jensenr30/cad/cheatsheets/CNC G Codes_files/g41-g42-Cutter-compensation.jpg

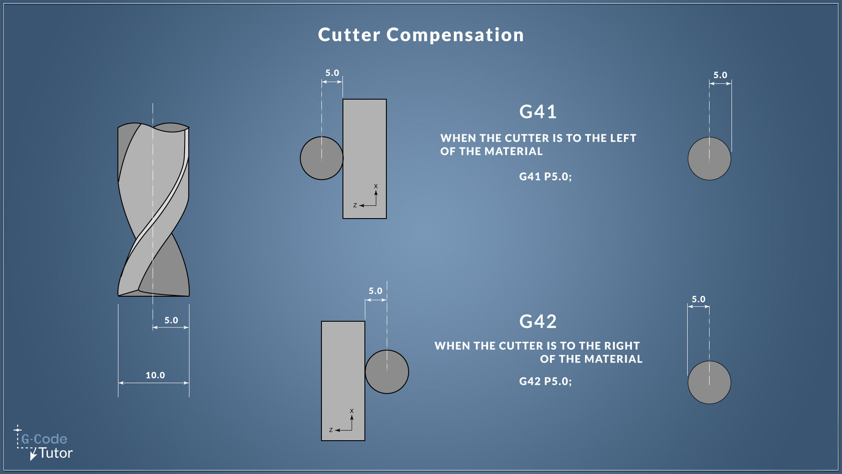
cheatsheets/CNC G Codes_files/g41-g42-Cutter-compensation.jpg
