jensenr30/cad/eagle6/555 stuff/555 blinker pcb.png

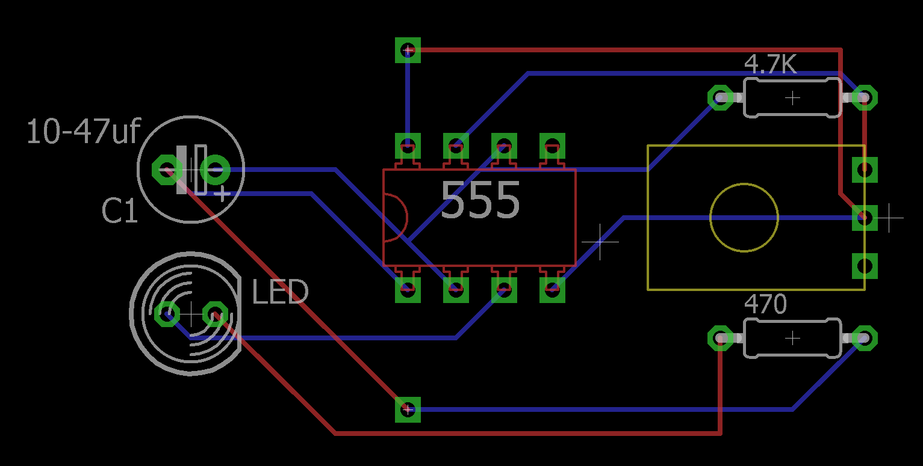
eagle6/555 stuff/555 blinker pcb.png
