jensenr30/cad/eagle6/dir.png

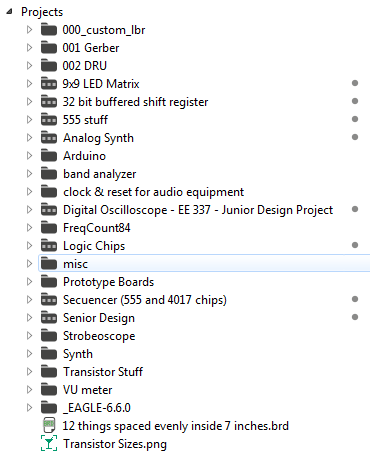
eagle6/dir.png
