jensenr30/cad/eagle6/misc/Logic Chips/AND gate.png

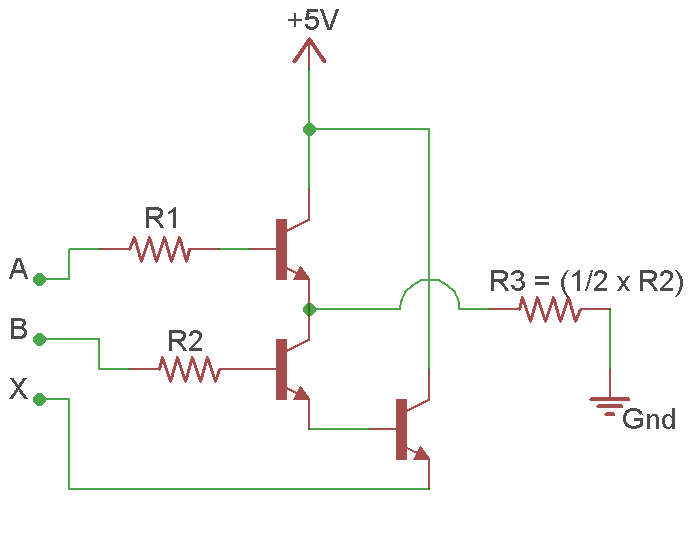
eagle6/misc/Logic Chips/AND gate.png
