jensenr30/cad/eagle6/misc/Logic Chips/D Latch Memory.png

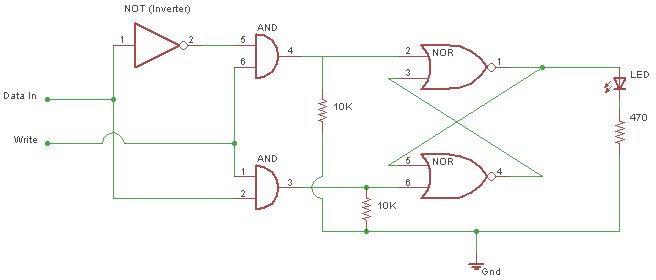
eagle6/misc/Logic Chips/D Latch Memory.png
