jensenr30/cad/eagle6/misc/noise generator output.jpg

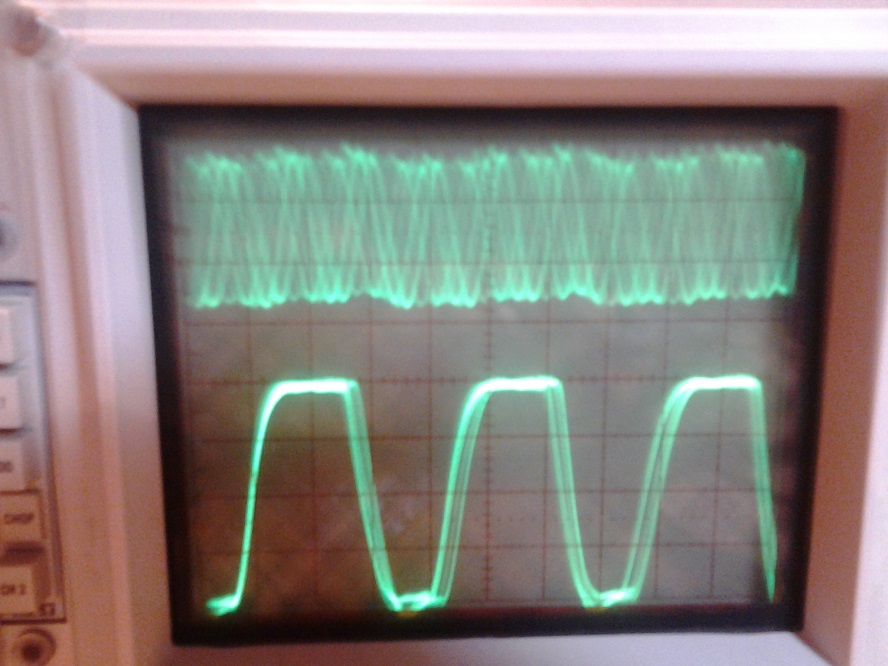
eagle6/misc/noise generator output.jpg
