jensenr30/cad/eagle6/misc/noise generator.jpg

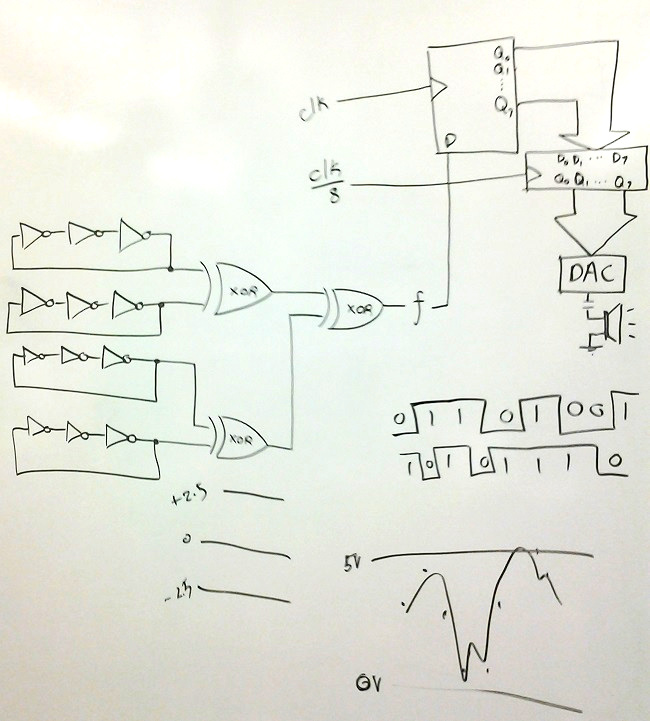
eagle6/misc/noise generator.jpg
