jensenr30/cad/eagle6/misc/people using my awful 555 AM harmonic radio transmitter/dangerous prototypes.png

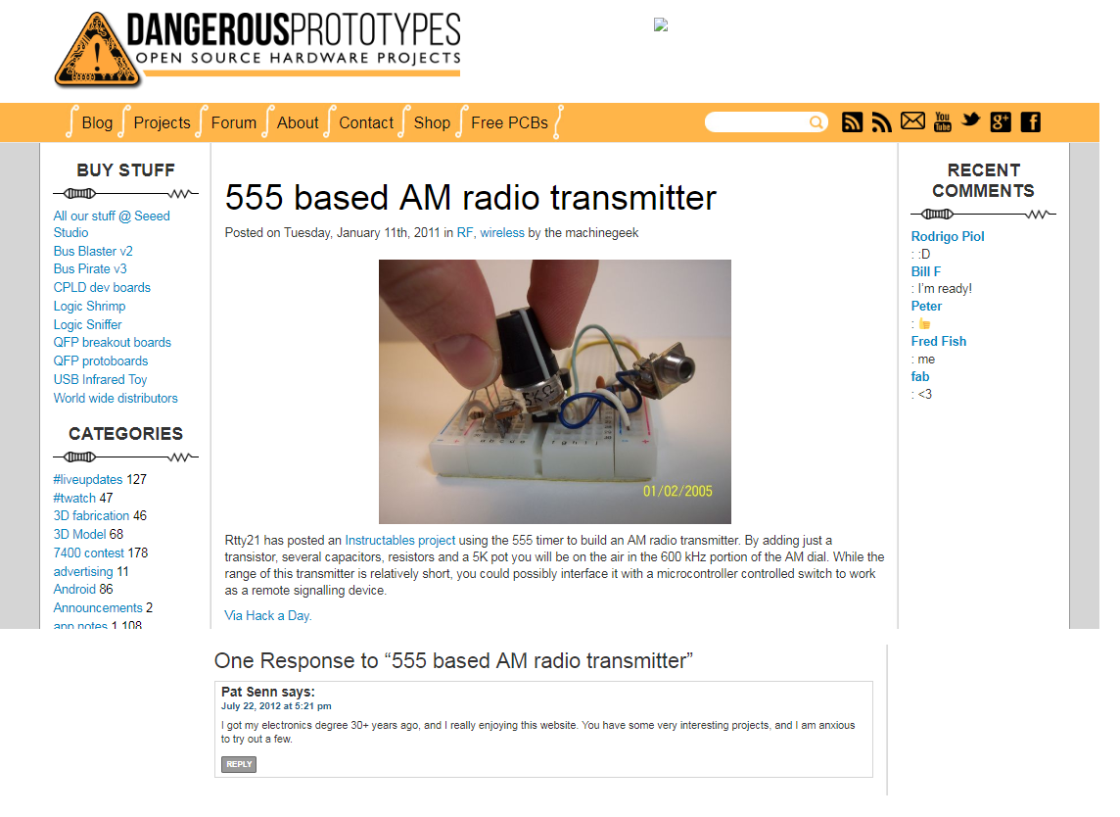
eagle6/misc/people using my awful 555 AM harmonic radio transmitter/dangerous prototypes.png
