jensenr30/cad/eagle6/misc/people using my awful 555 AM harmonic radio transmitter/Gainsville amature radio/Screenshot_1.png

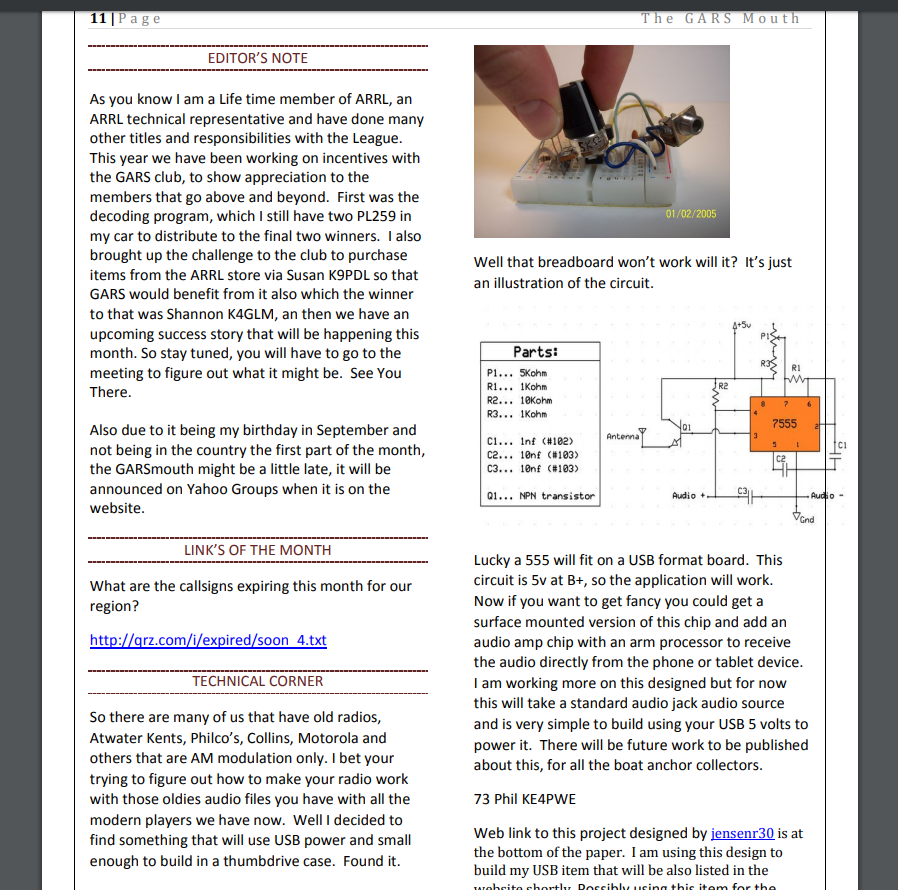
eagle6/misc/people using my awful 555 AM harmonic radio transmitter/Gainsville amature radio/Screenshot_1.png
