jensenr30/cad/eagle6/misc/sine8-200.png

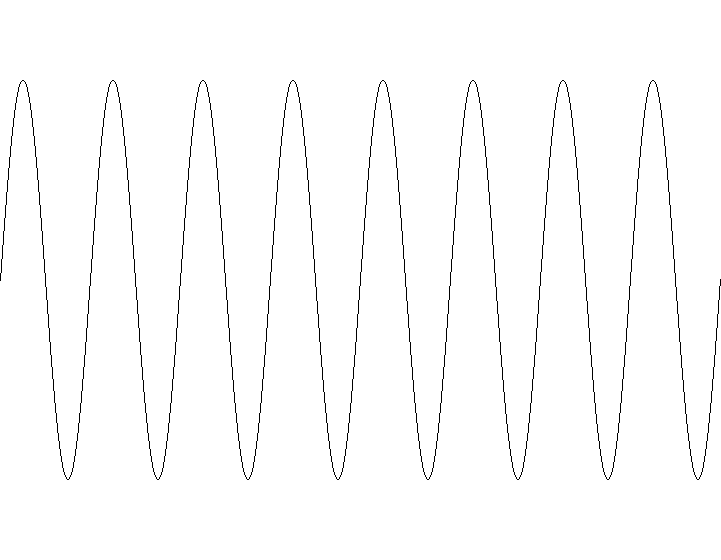
eagle6/misc/sine8-200.png
