jensenr30/cad/eagle6/misc/Transistor Sizes.png

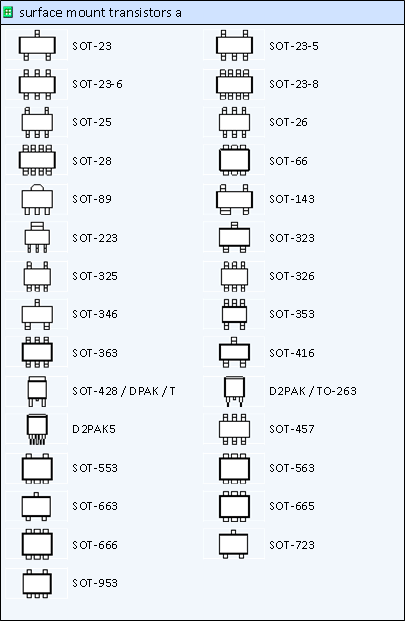
eagle6/misc/Transistor Sizes.png
