jensenr30/cad/eagle6/Prototype Boards/breakout board pack 1/render.png

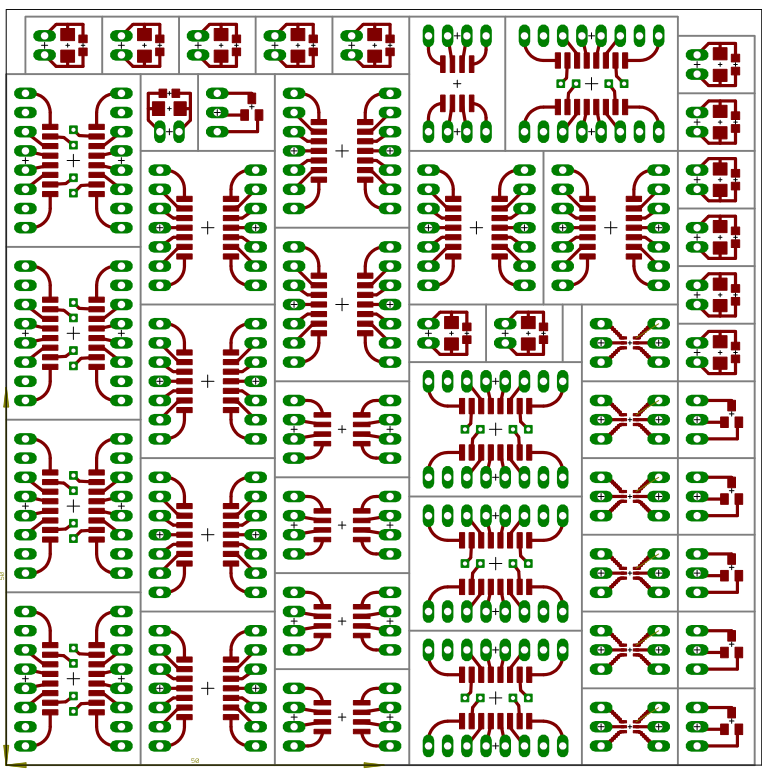
eagle6/Prototype Boards/breakout board pack 1/render.png
