jensenr30/cad/eagle6/Prototype Boards/pad-per-hole-and-rails/DirtyPCBOrder.png

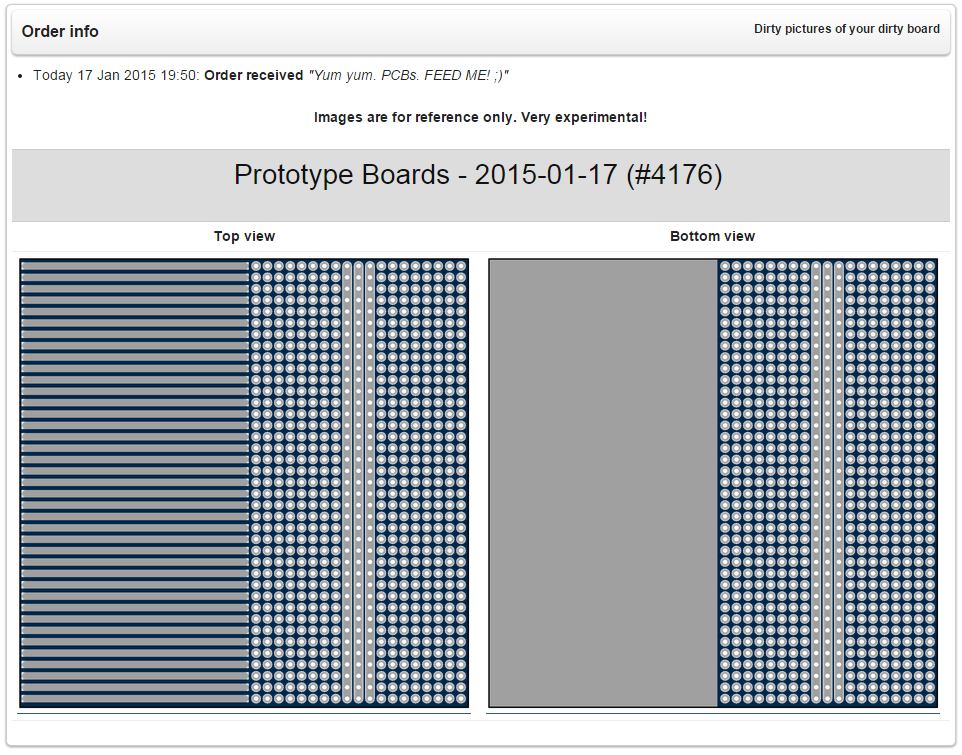
eagle6/Prototype Boards/pad-per-hole-and-rails/DirtyPCBOrder.png
