jensenr30/cad/eagle6/Prototype Boards/pad-per-hole-and-rails/render.png

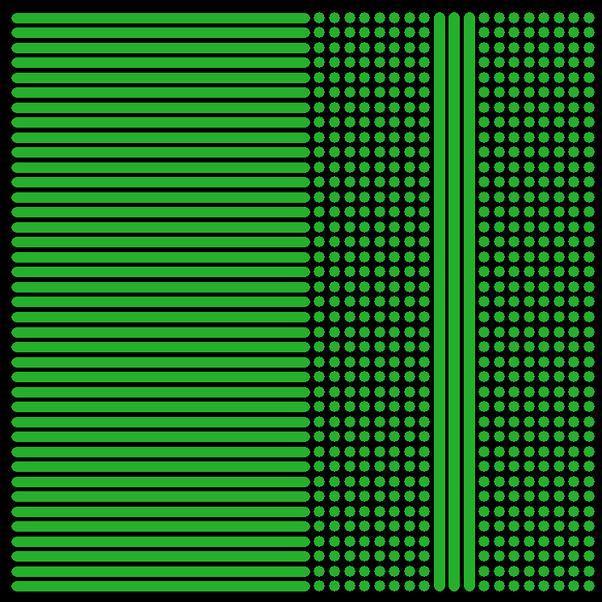
eagle6/Prototype Boards/pad-per-hole-and-rails/render.png
