jensenr30/cad/eagle6/Prototype Boards/surface mount pads/render.png

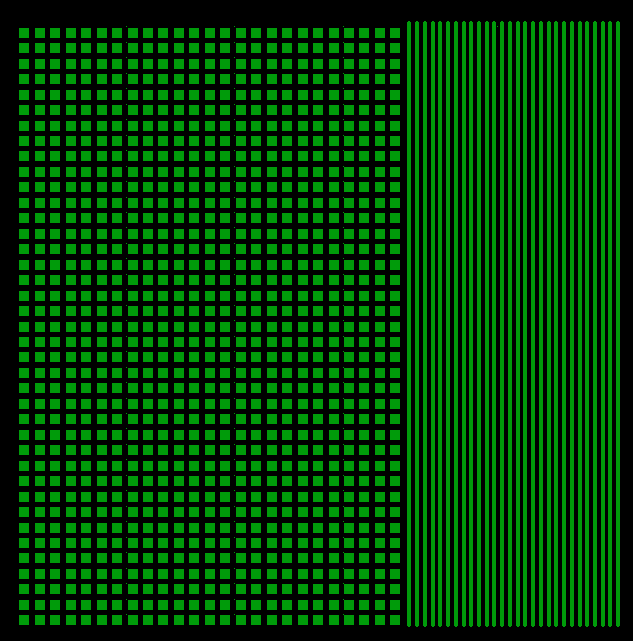
eagle6/Prototype Boards/surface mount pads/render.png
