jensenr30/cad/kicad4/XPhone/Input_Board/gerbers/Input Board-F.Fab.png

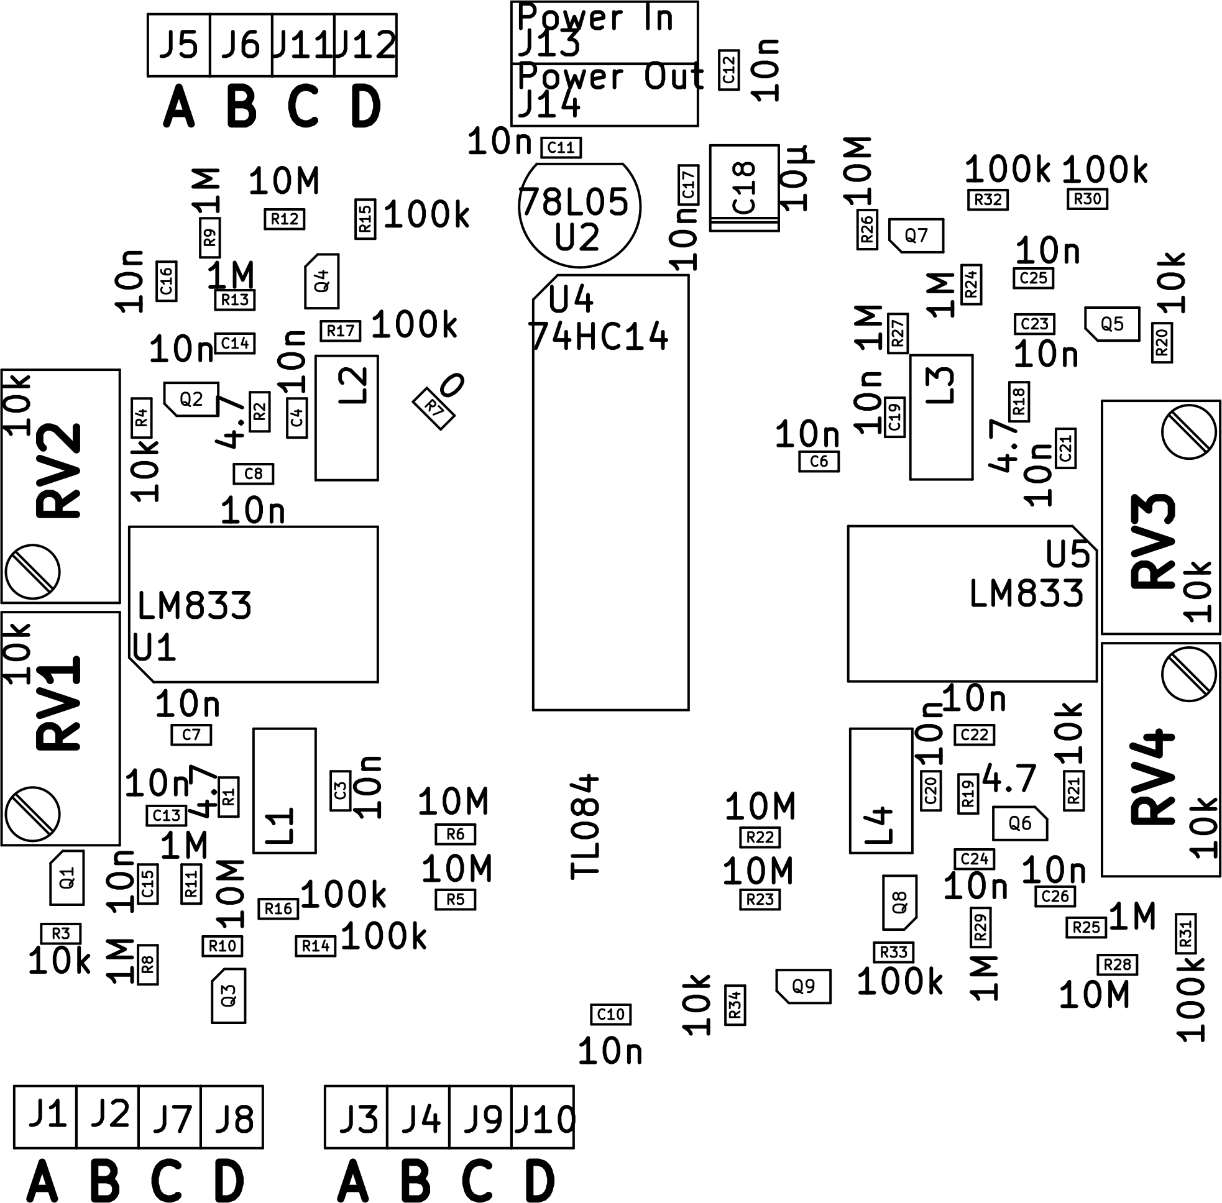
kicad4/XPhone/Input_Board/gerbers/Input Board-F.Fab.png
