jensenr30/cad/src/geography/u.s. states/wisconsin/wisconsin-from-google-maps.png

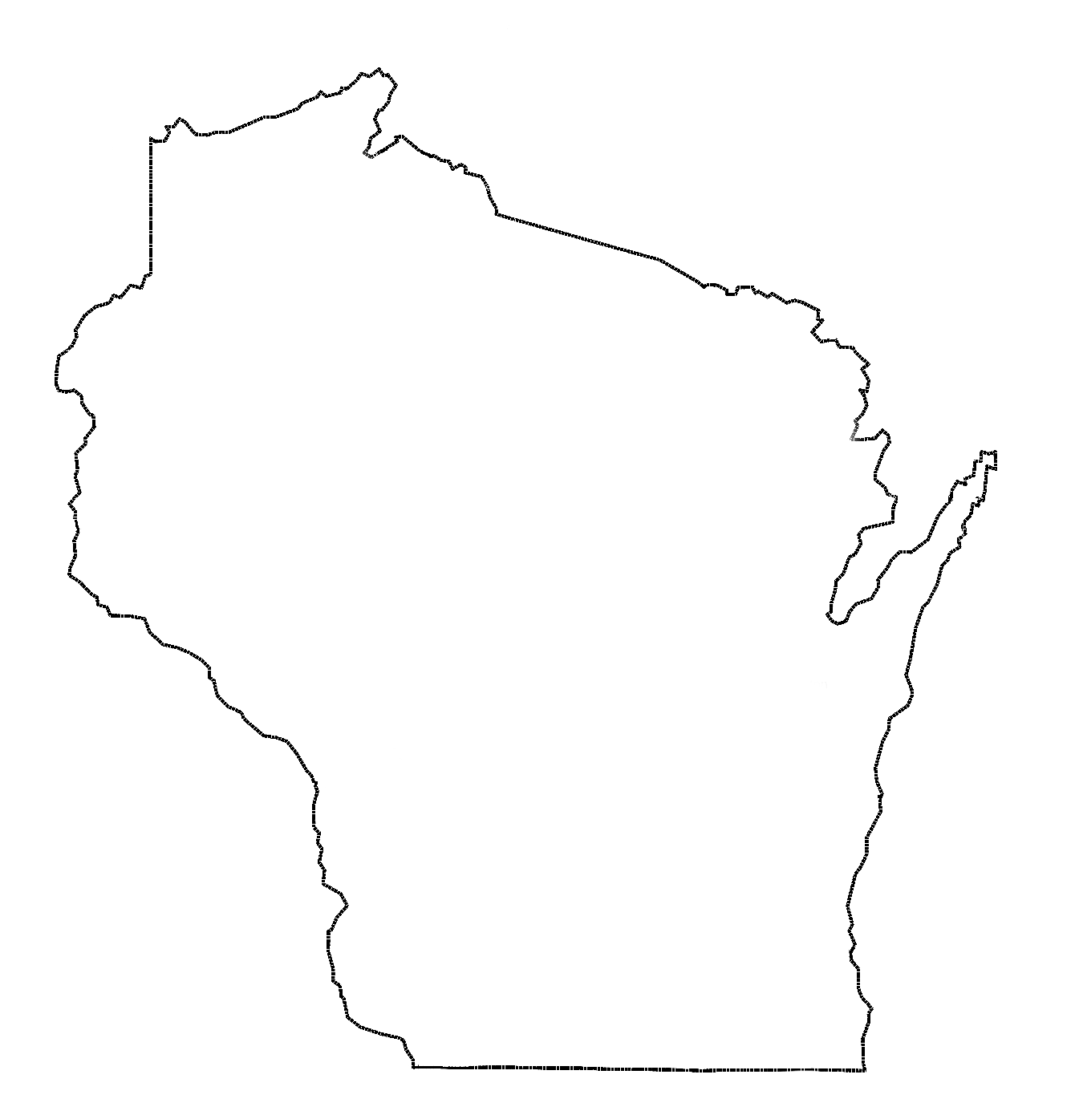
src/geography/u.s. states/wisconsin/wisconsin-from-google-maps.png
