jensenr30/cad/src/geography/u.s. states/wisconsin/wisconsin-silhouette-smooth-1.png

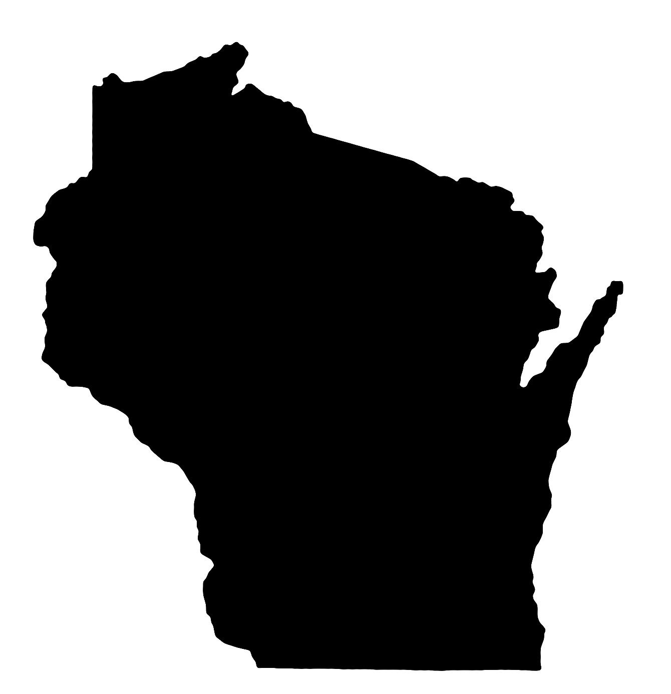
src/geography/u.s. states/wisconsin/wisconsin-silhouette-smooth-1.png
