jensenr30/cad/eagle6/8-Note Secuencer (555 and 4017 chips)/eight note sequencer.pdf

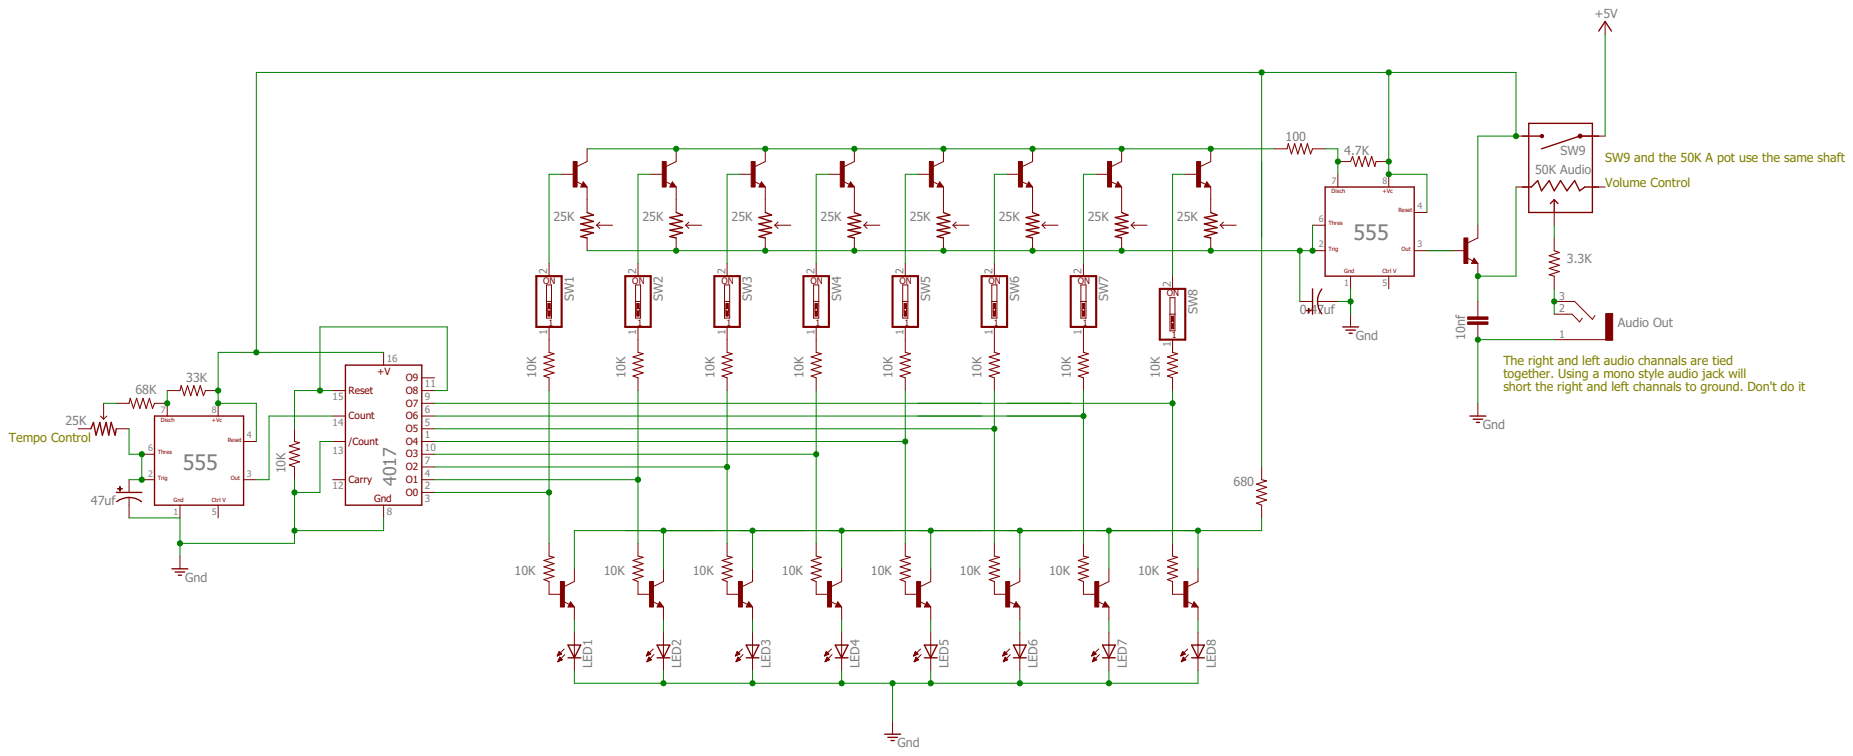
[picture p41: page 1]

SW9 and the 50K A pot use the same shaft Volume Control

The right and left audio channals are tied
together. Using a mono style audio jack will short the right and left channals to ground. Don't do it
