jensenr30/cad/eagle6/FreqCount84/FreqCount84.pdf

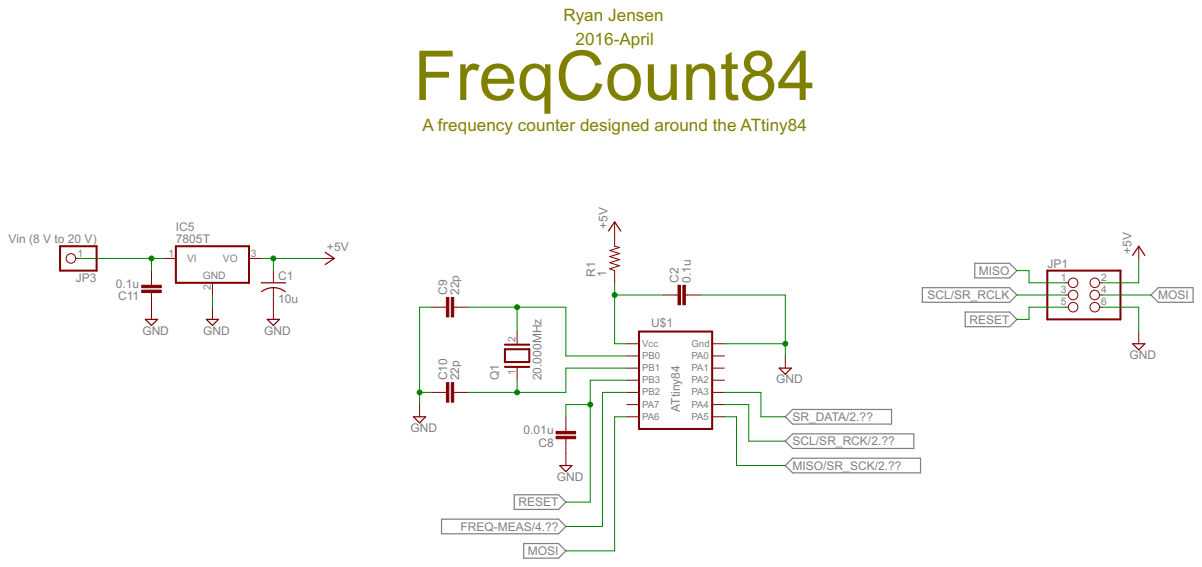
[picture p44: page 1]

A frequency counter designed around the ATtiny84

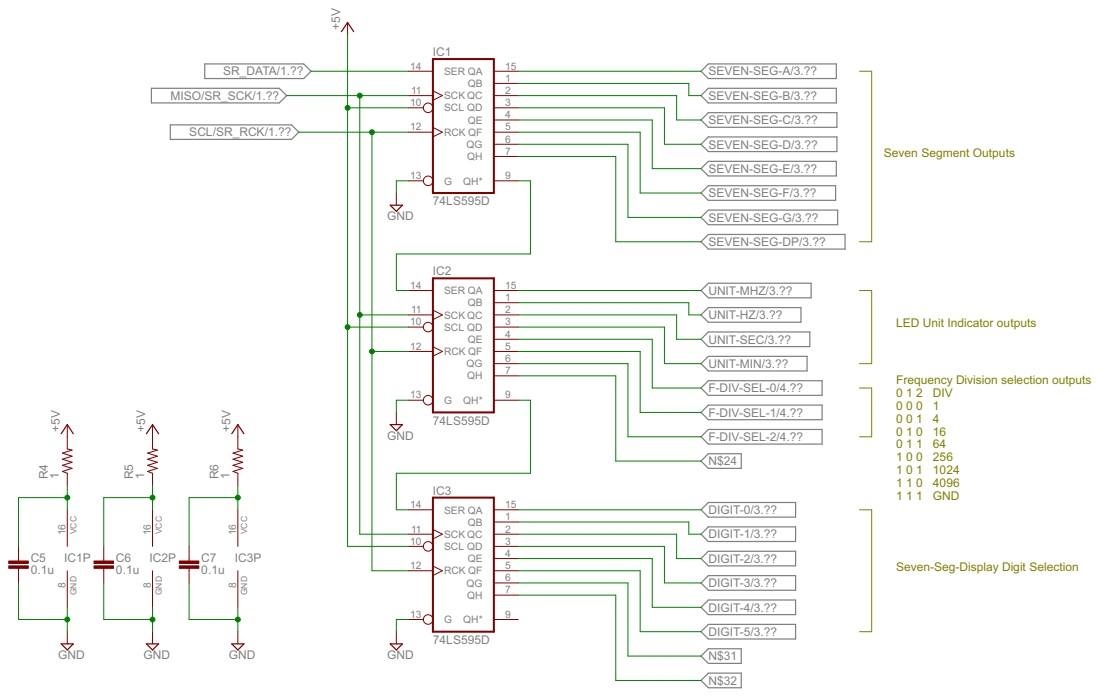
[picture p45: page 2]

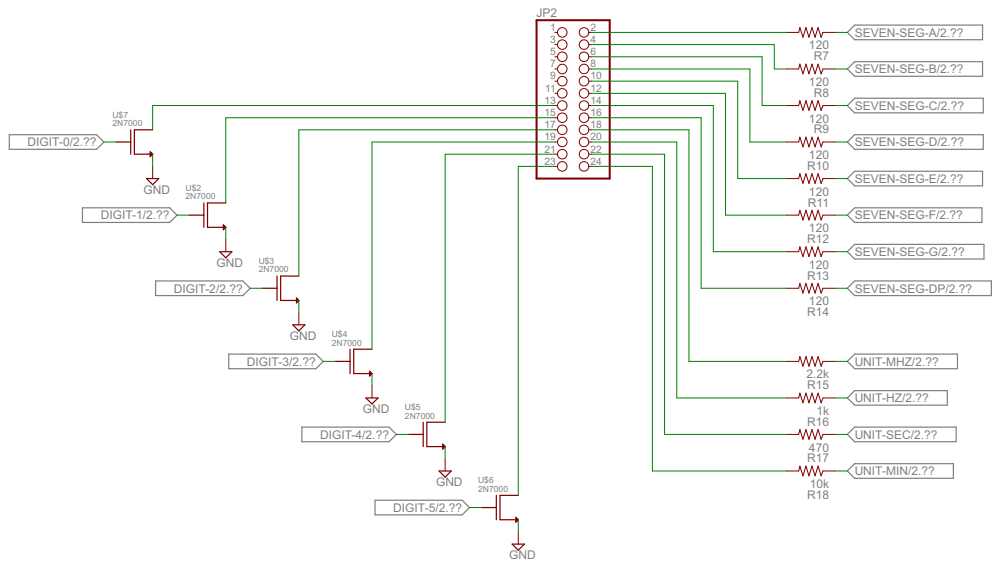
[picture p46: page 3]

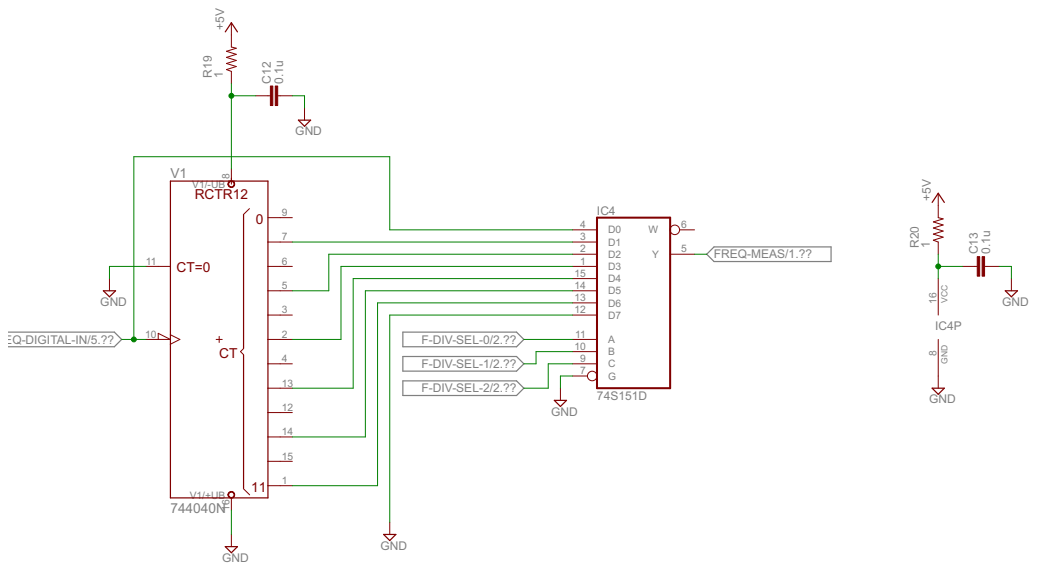
[picture p47: page 4]

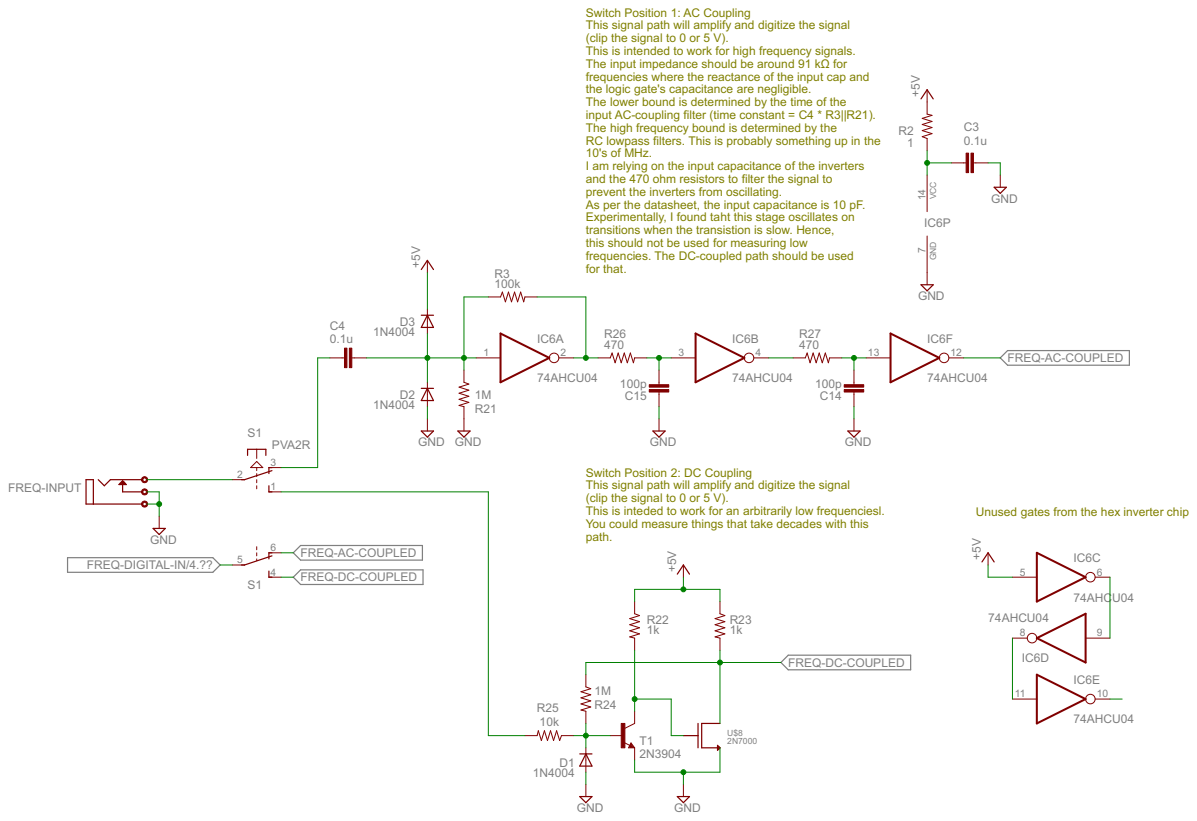
[picture p48: page 5]

Switch Position 1: AC Coupling
This signal path will amplify and digitize the signal
(clip the signal to 0 or 5 V). This is intended to work for high frequency signals. The input impedance should be around 91 kΩ for

frequencies where the reactance of the input cap and
the logic gate's capacitance are negligible. The lower bound is determined by the time of the

input AC-coupling filter (time constant = C4 * R3||R21). The high frequency bound is determined by the RC lowpass filters. This is probably something up in the

10's of MHz.
I am relying on the input capacitance of the inverters and the 470 ohm resistors to filter the signal to

prevent the inverters from oscillating. As per the datasheet, the input capacitance is 10 pF. Experimentally, I found taht this stage oscillates on

transitions when the transistion is slow. Hence,
this should not be used for measuring low
frequencies. The DC-coupled path should be used
for that.

Switch Position 2: DC Coupling
