jensenr30/cad/eagle6/misc/Reference Board.pdf

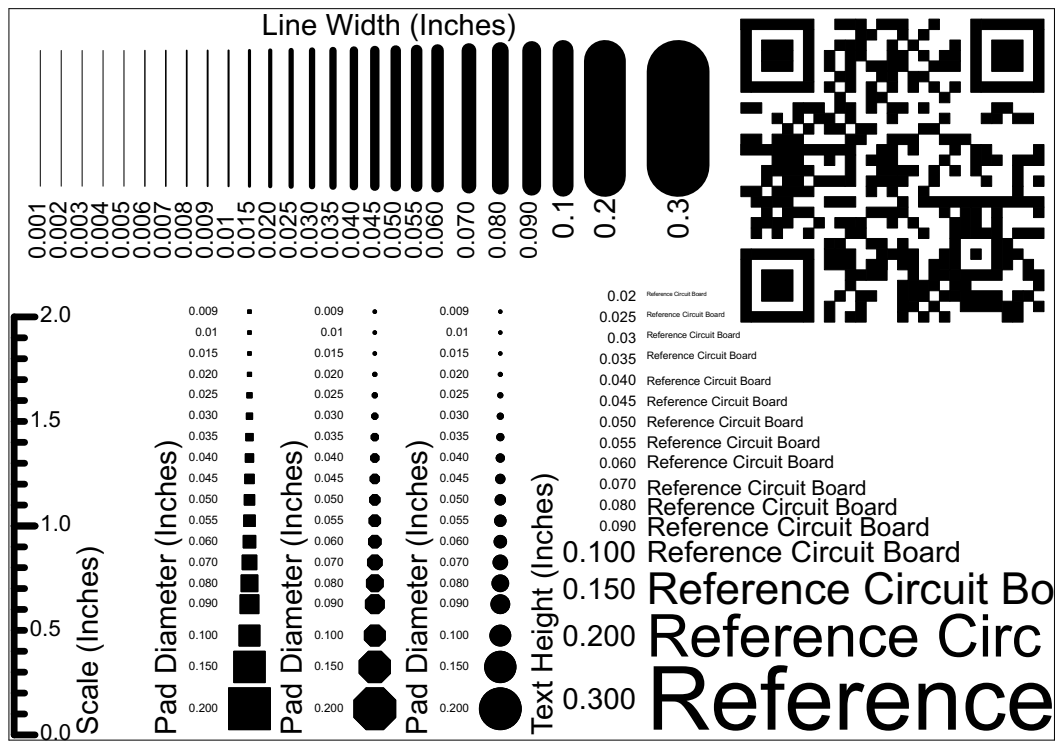
[picture p49: page 1]

Reference Circuit Board Reference Circuit Board Reference Circuit Board Reference Circuit Board Reference Circuit Board Reference Circuit Board Reference Circuit Board Reference Circuit Board Reference Circuit Board Reference Circuit Board Reference Circuit Bo
