jensenr30/cad/kicad4/SRBOB/SRBOB.pdf

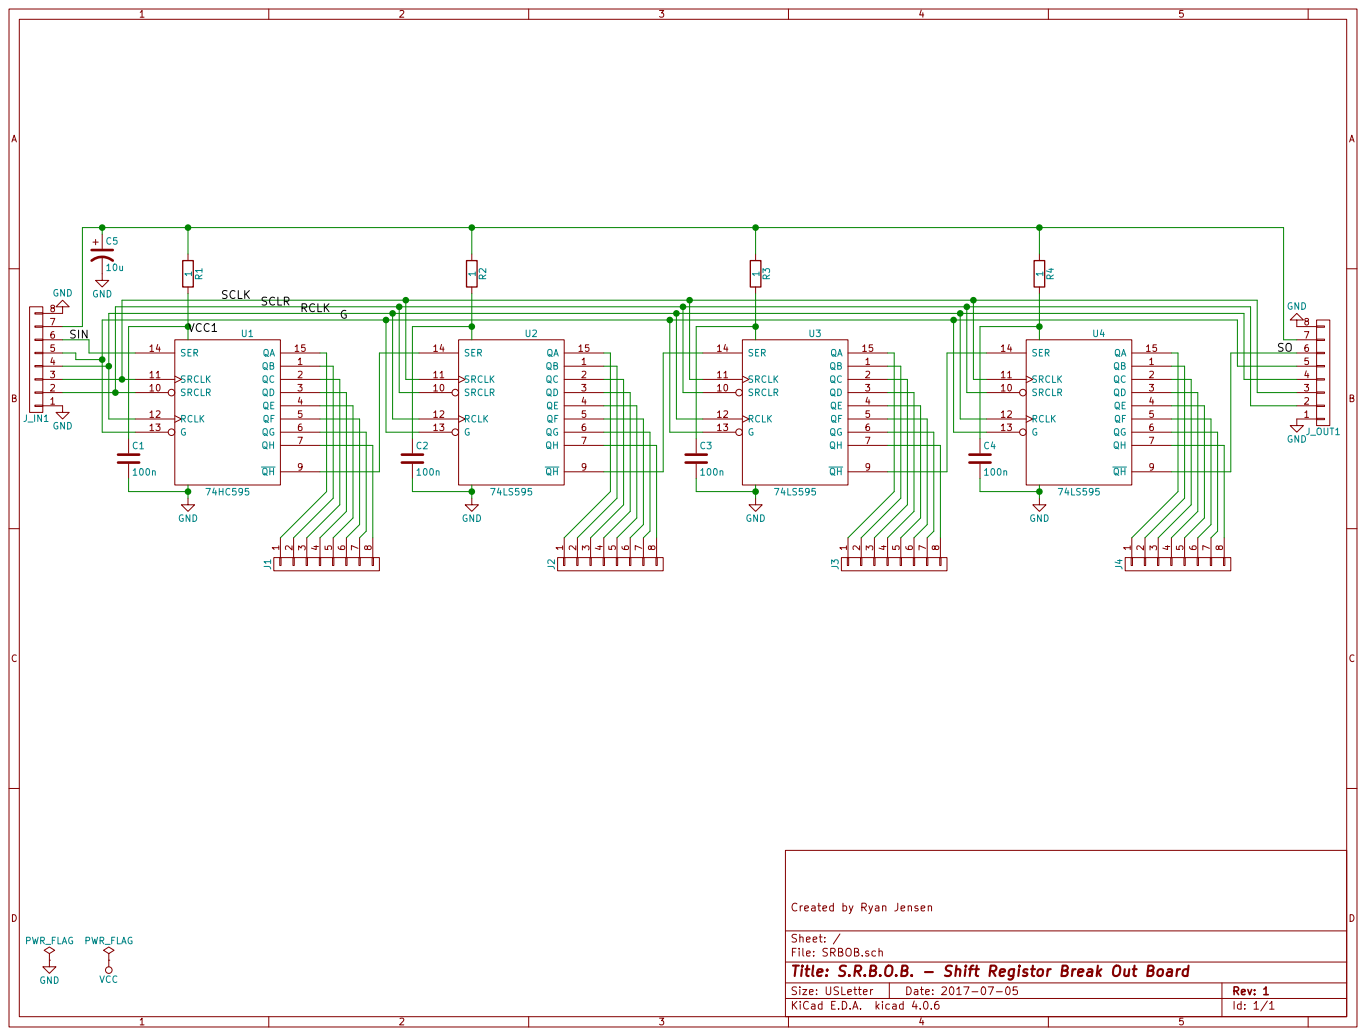
[picture p50: page 1]

File: SRBOB.sch Sheet: / Created by Ryan Jensen

Id: 1/1 Title: S.R.B.O.B. - Shift Registor Break Out Board
