jensenr30/cad/kicad4/XPhone/Input_Board/Input_Board Rev 1.1 black.pdf

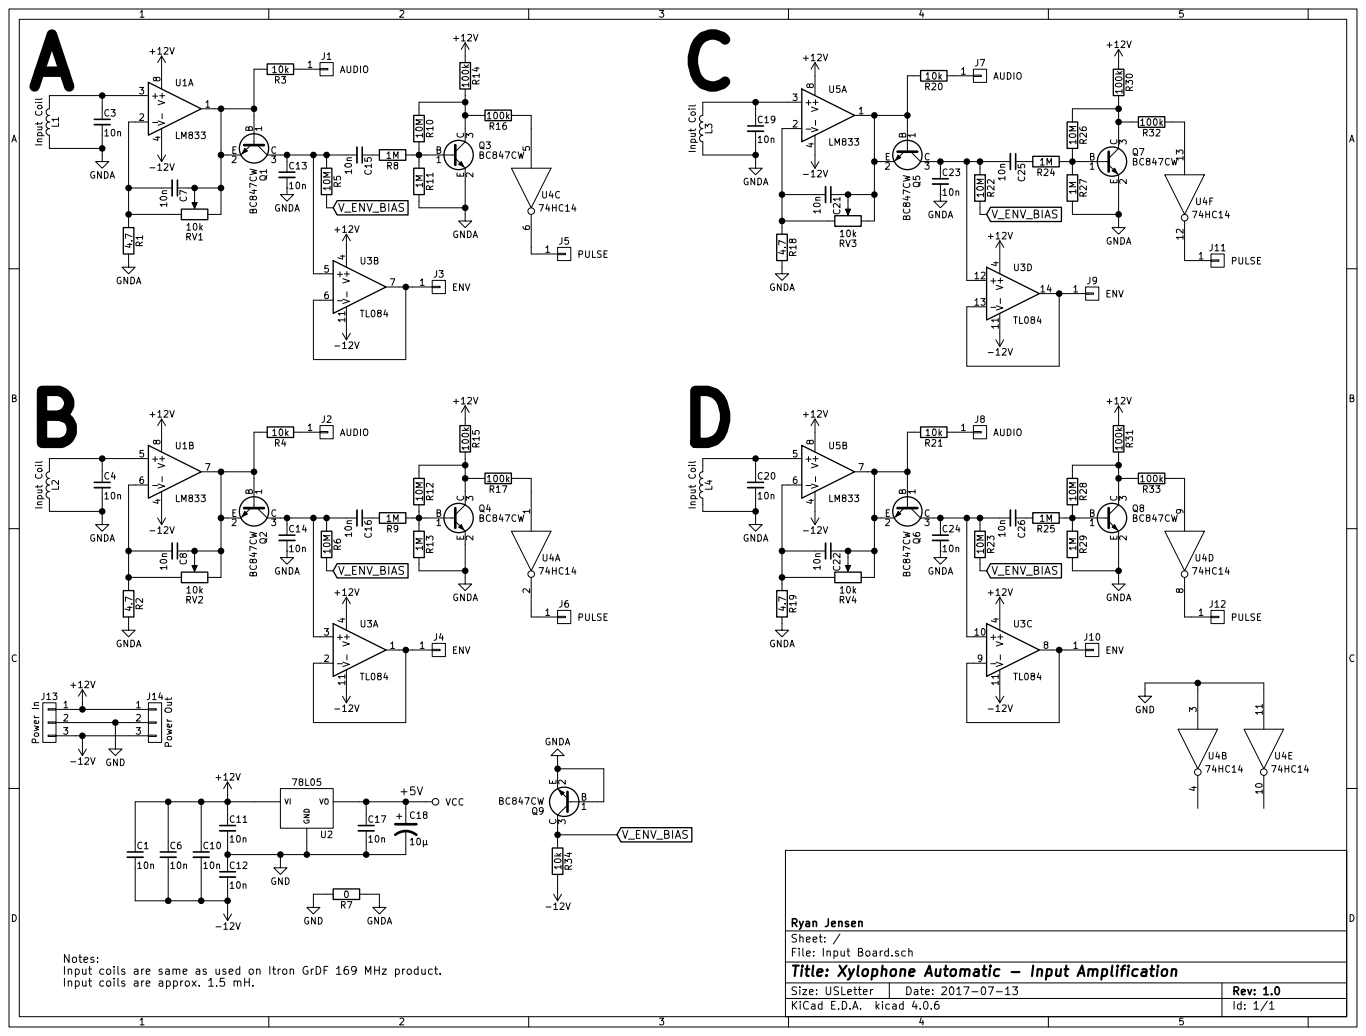
[picture p53: page 1]

File: Input Board.sch Sheet: / Ryan Jensen V- 4 V+

Input coils are same as used on Itron GrDF 169 MHz product.
Input coils are approx. 1.5 mH.

Id: 1/1 Title: Xylophone Automatic - Input Amplification
