jensenr30/cad/eagle6/Analog Synth/VCA-v2/2.0/VCA-v2.pdf

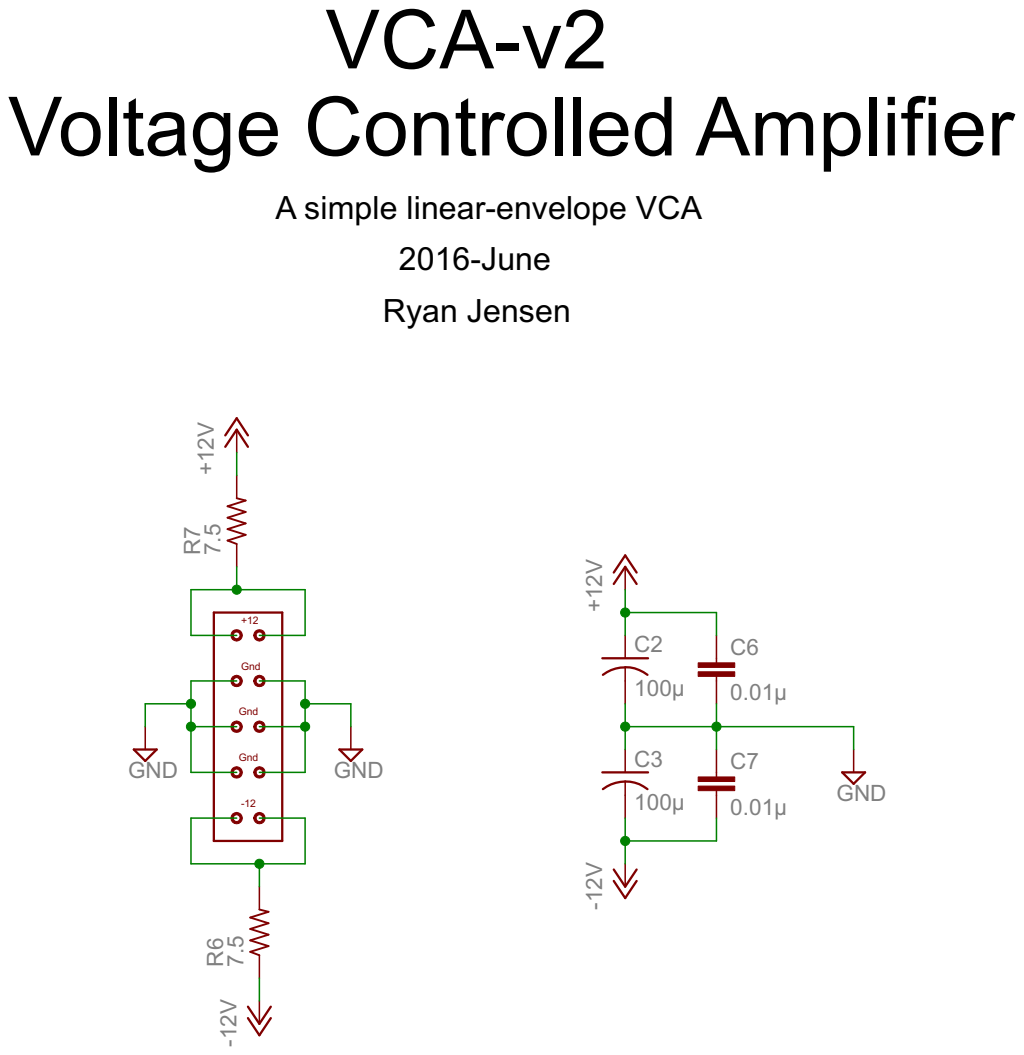
[picture p54: page 1]

A simple linear-envelope VCA

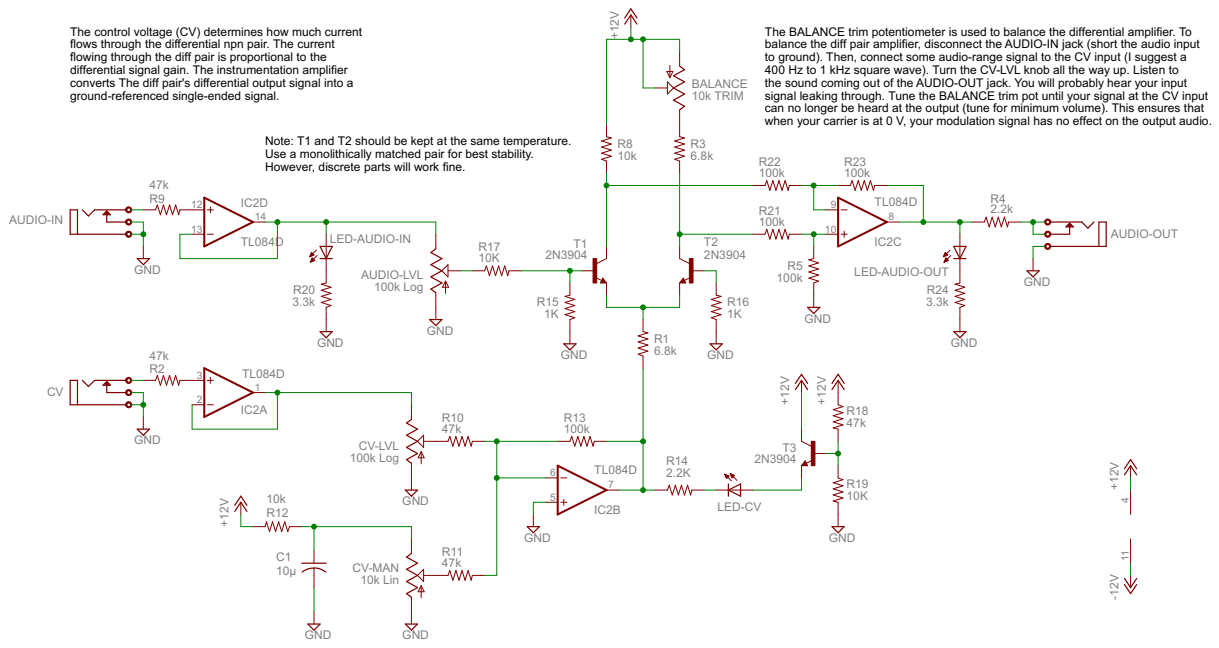
[picture p55: page 2]

The control voltage (CV) determines how much current
flows through the differential npn pair. The current
flowing through the diff pair is proportional to the
differential signal gain. The instrumentation amplifier converts The diff pair's differential output signal into a

The BALANCE trim potentiometer is used to balance the differential amplifier. To
balance the diff pair amplifier, disconnect the AUDIO-IN jack (short the audio input
to ground). Then, connect some audio-range signal to the CV input (I suggest a
400 Hz to 1 kHz square wave). Turn the CV-LVL knob all the way up. Listen to

the sound coming out of the AUDIO-OUT jack. You will probably hear your input signal leaking through. Tune the BALANCE trim pot until your signal at the CV input can no longer be heard at the output (tune for minimum volume). This ensures that when your carrier is at 0 V, your modulation signal has no effect on the output audio. Note: T1 and T2 should be kept at the same temperature. Use a monolithically matched pair for best stability. However, discrete parts will work fine.

ground-referenced single-ended signal.
