jensenr30/cad/kicad4/SRBOB/gerbers/pdfs/SRBOB-B.SilkS.pdf

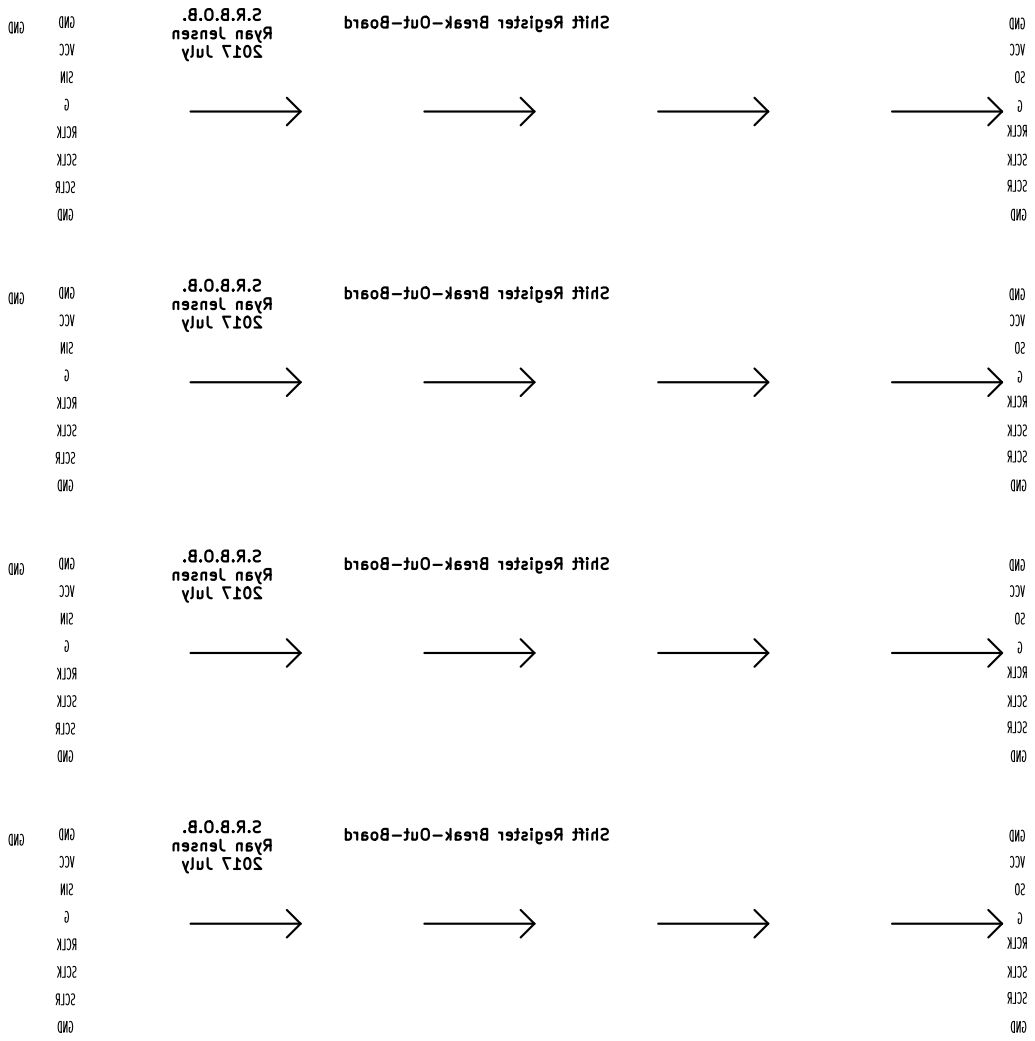
[picture p56: page 1]

RCLK GND GND GNDGND GND

Shift Register Break-Out-Board S.R.B.O.B. Ryan Jensen

2017 July Shift Register Break-Out-Board Shift Register Break-Out-Board Shift Register Break-Out-Board SCLK

RCLK GND GND GND
