jensenr30/cad/eagle6/Analog Synth/Keyboard Controller.pdf

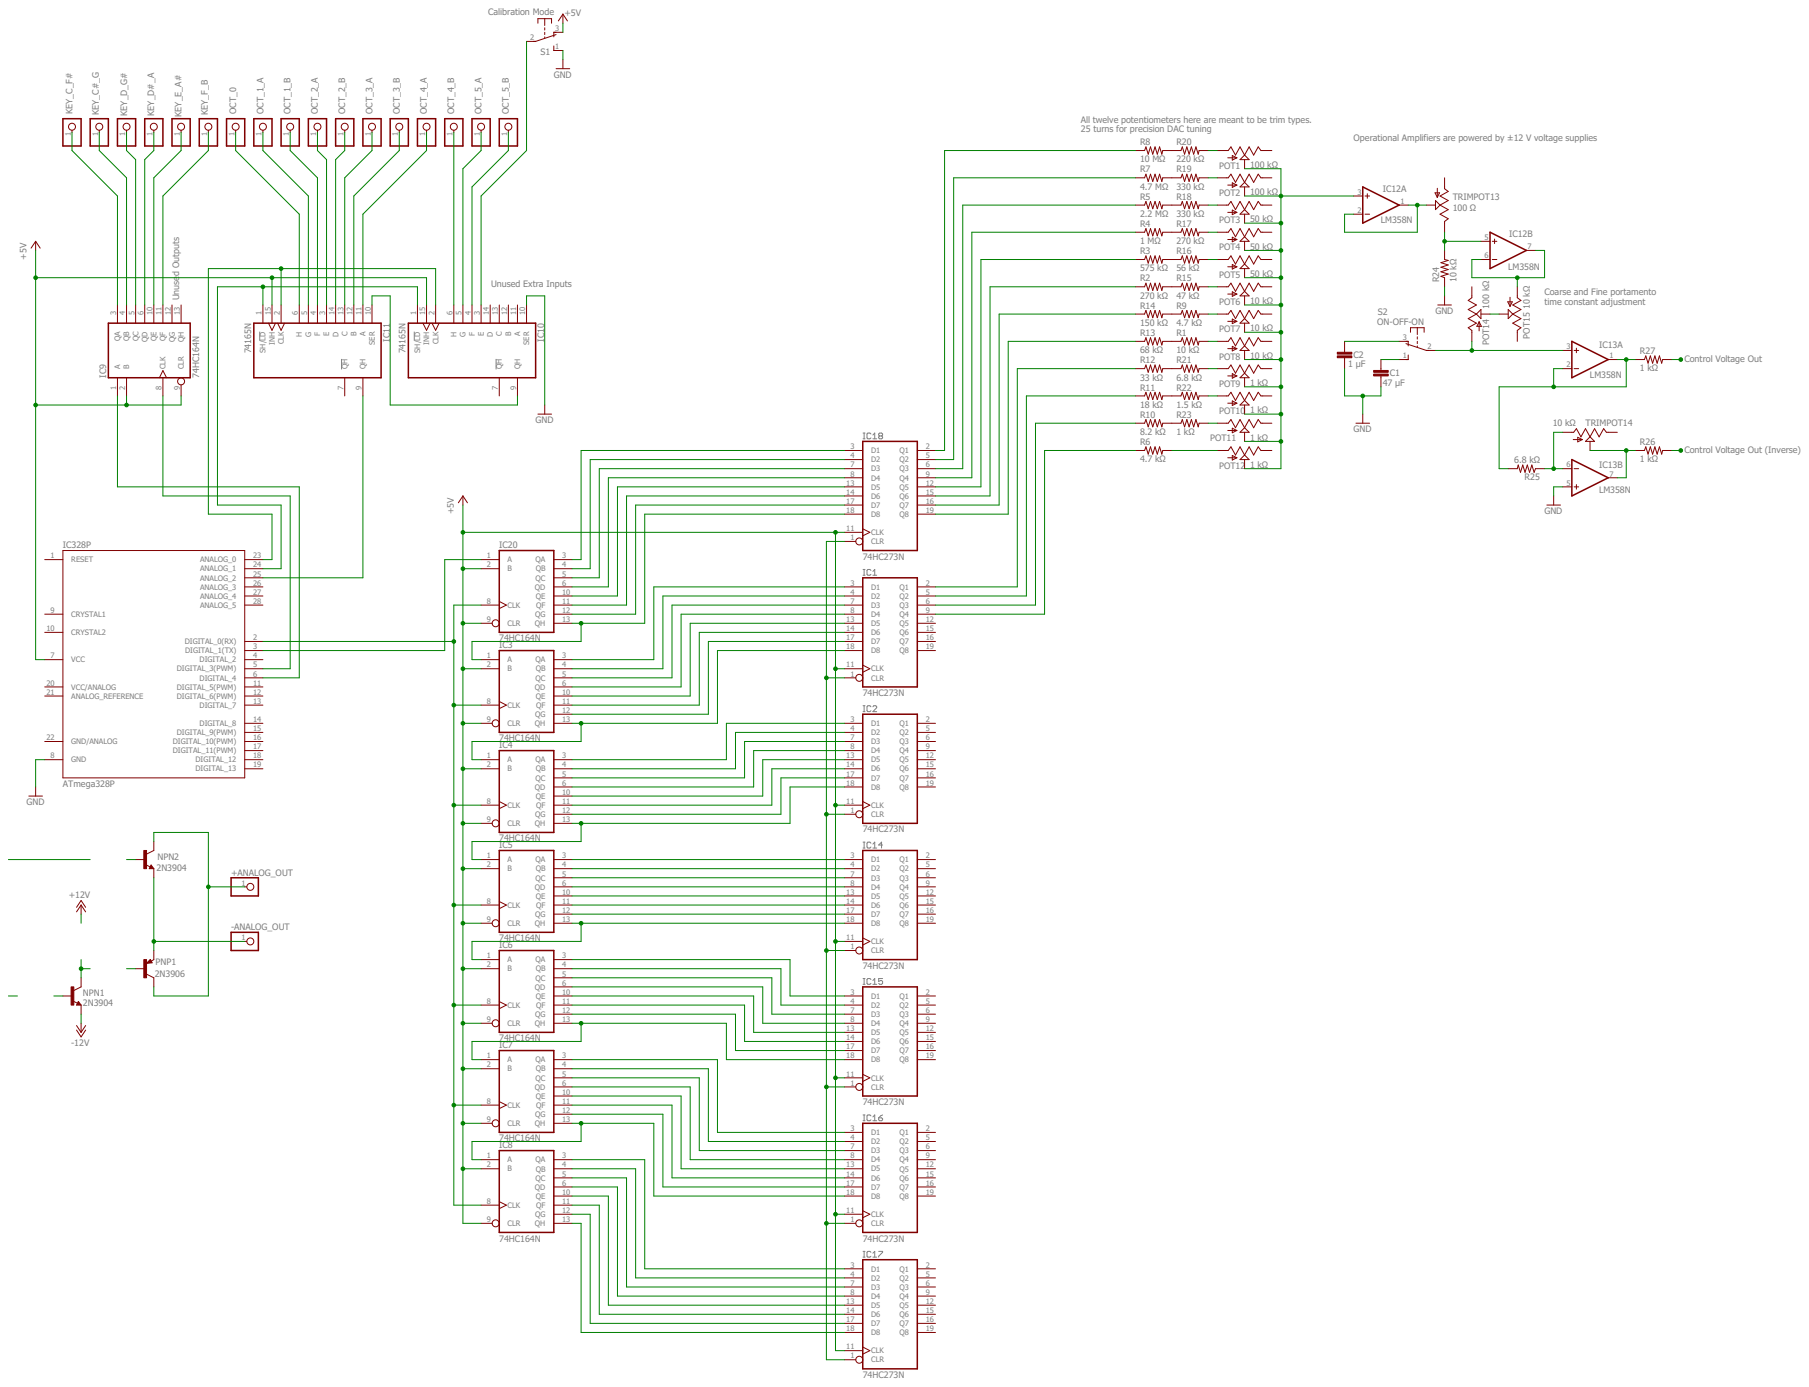
[picture p76: page 1]
