jensenr30/cad/eagle6/Analog Synth/Microphone Amplifier.pdf

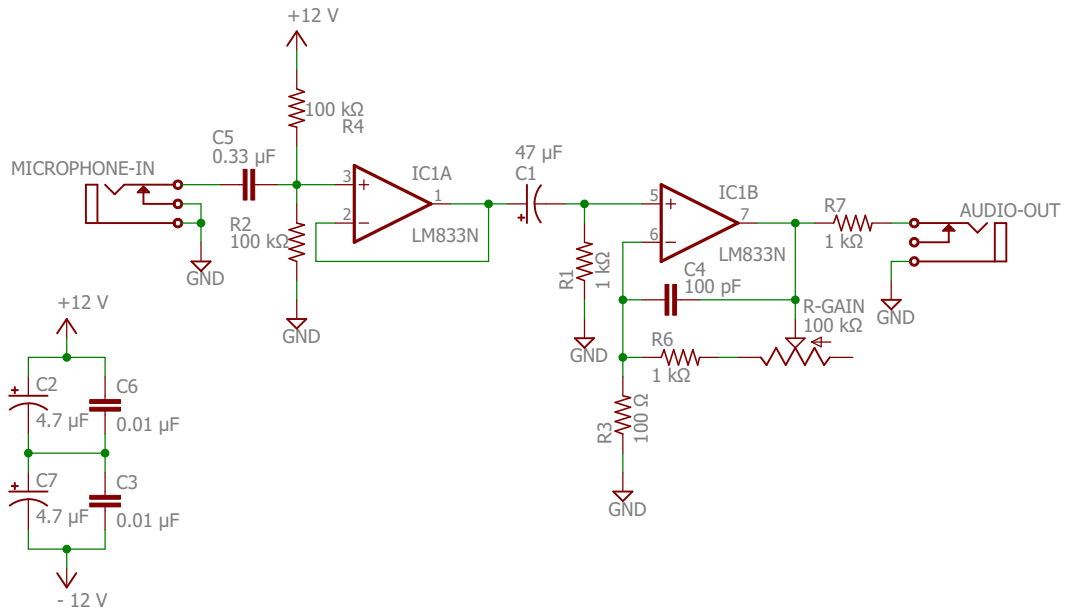
[picture p77: page 1]
