jensenr30/cad/eagle6/9x9 LED Matrix/9x9 LED Matrix.pdf

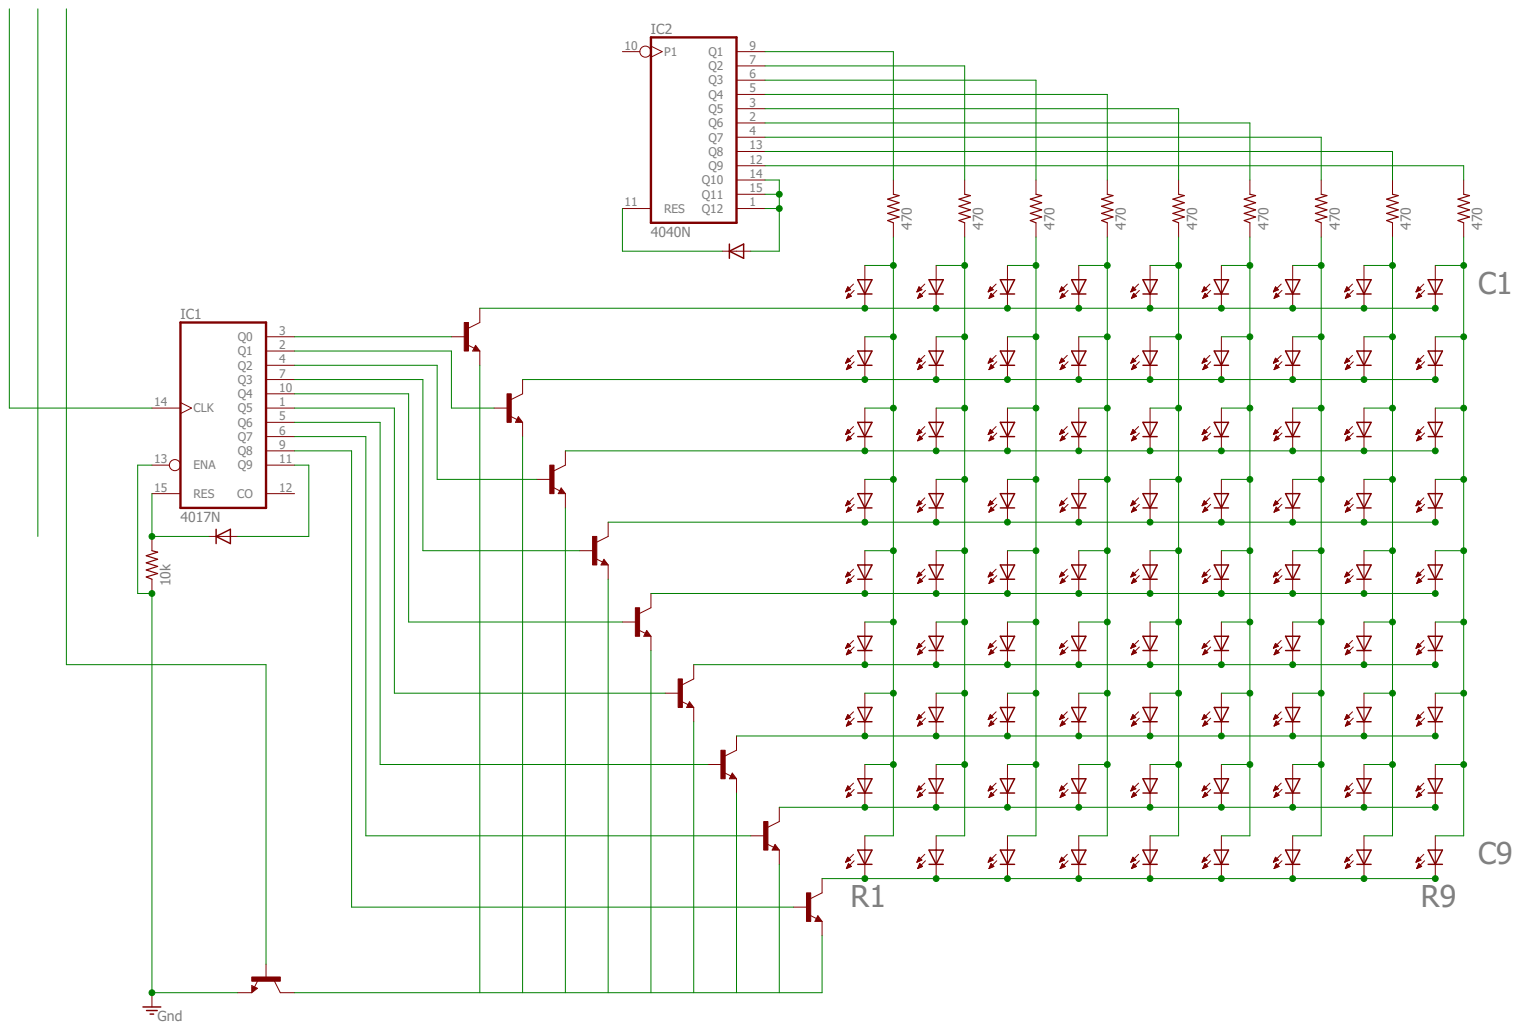
[picture p78: page 1]
