jensenr30/cad/eagle6/Arduino/4x6 LED Matrix.pdf

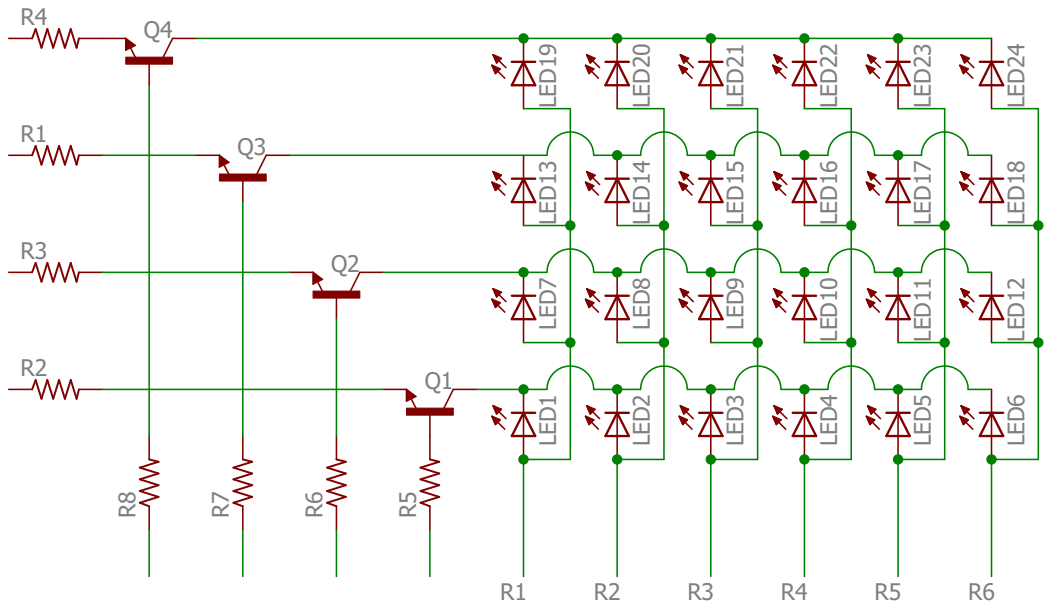
[picture p79: page 1]
