jensenr30/cad/eagle6/Arduino/9x9 LED Matrix.pdf

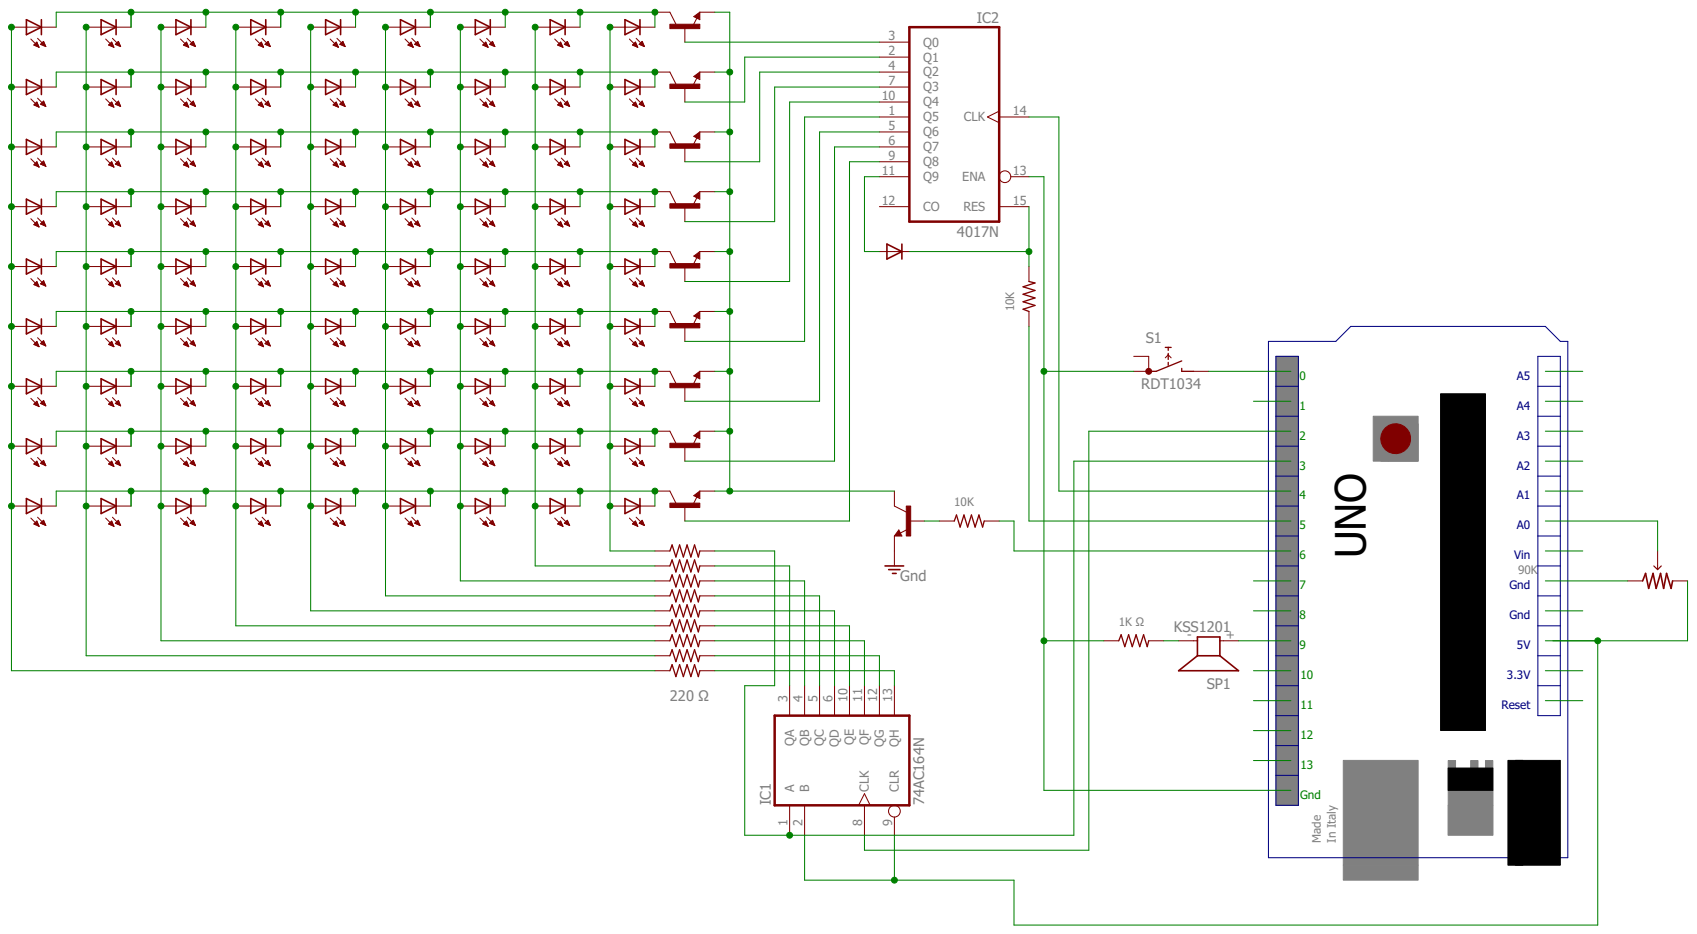
[picture p80: page 1]
