jensenr30/cad/eagle6/FreqCount84/FreqCount84.0.pdf

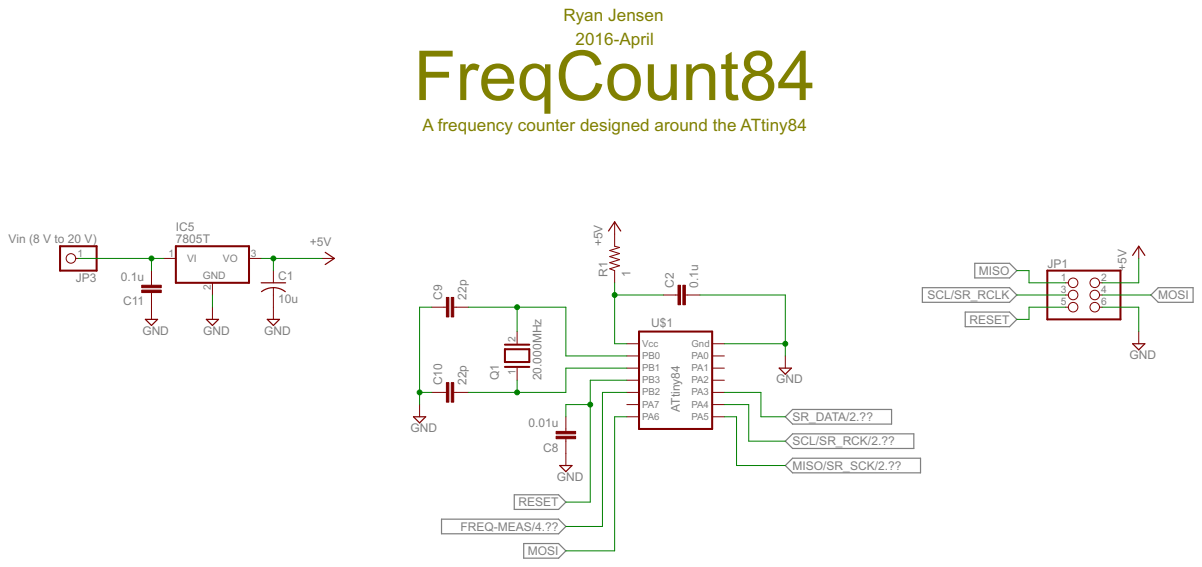
[picture p81: page 1]

A frequency counter designed around the ATtiny84

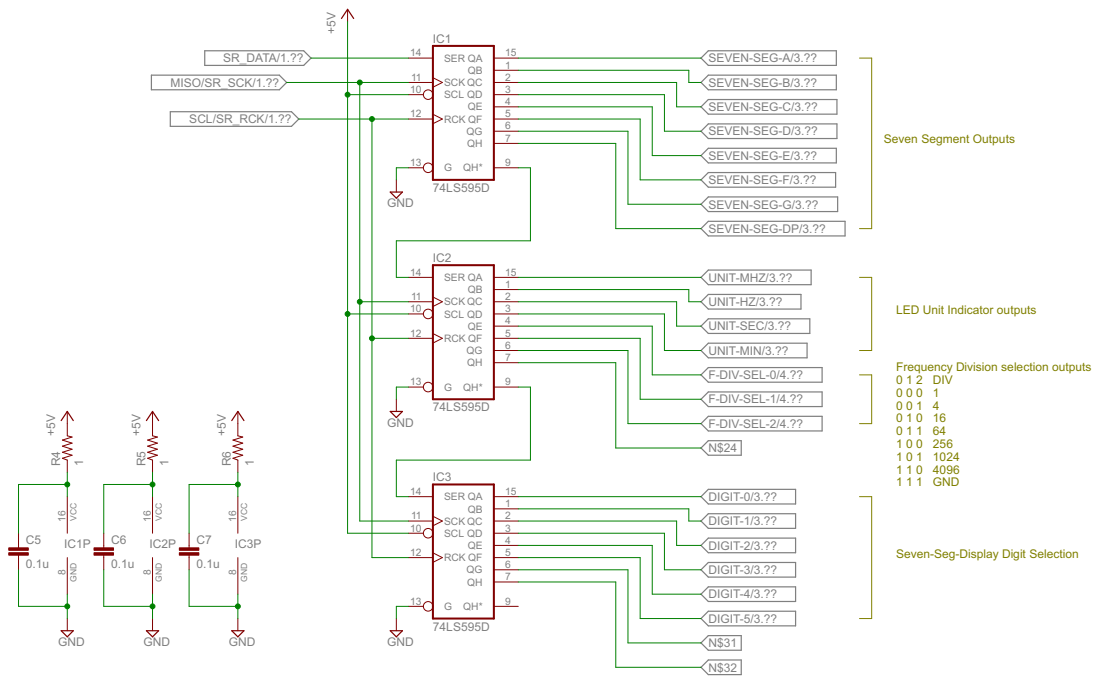
[picture p82: page 2]

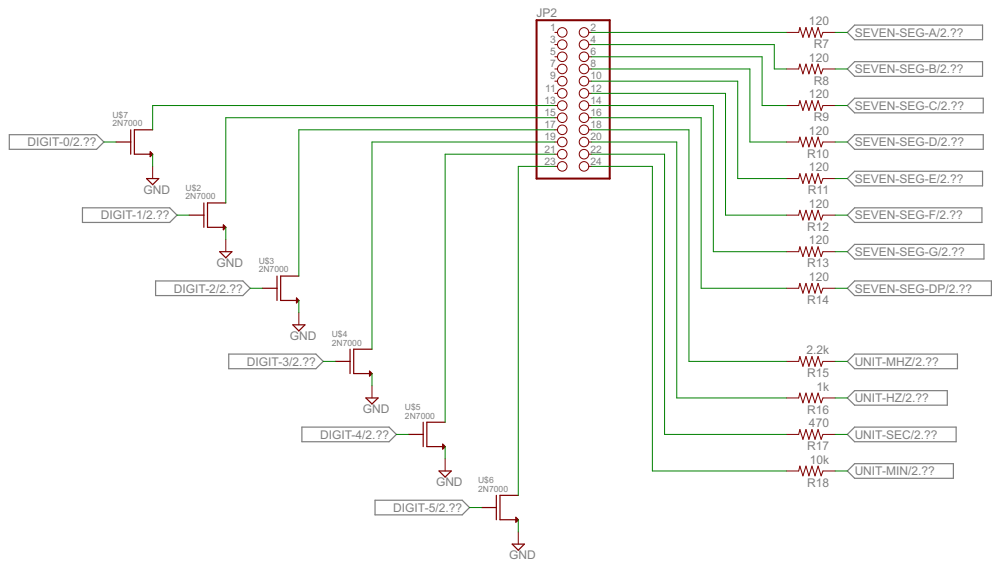
[picture p83: page 3]

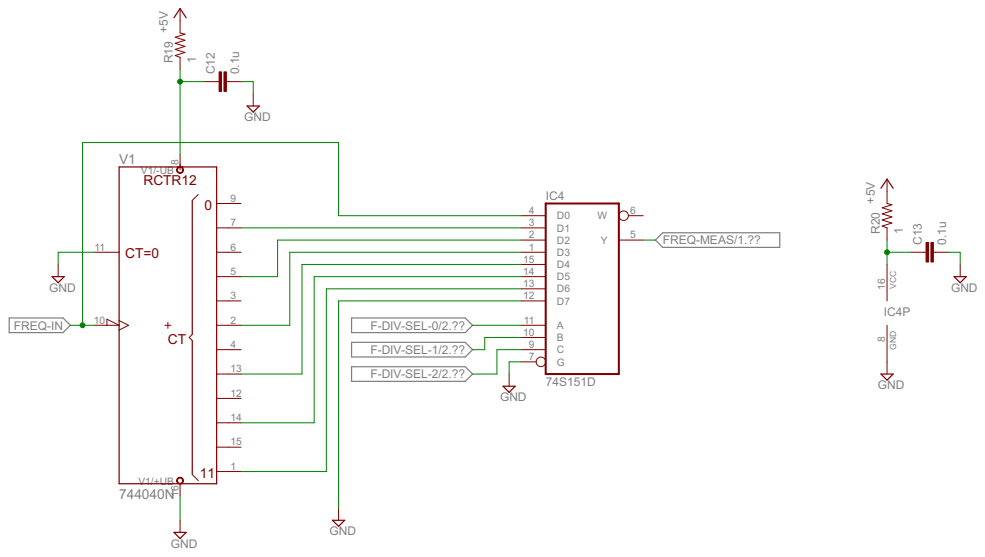
[picture p84: page 4]
