jensenr30/cad/eagle6/misc/Fractal Antenna.pdf

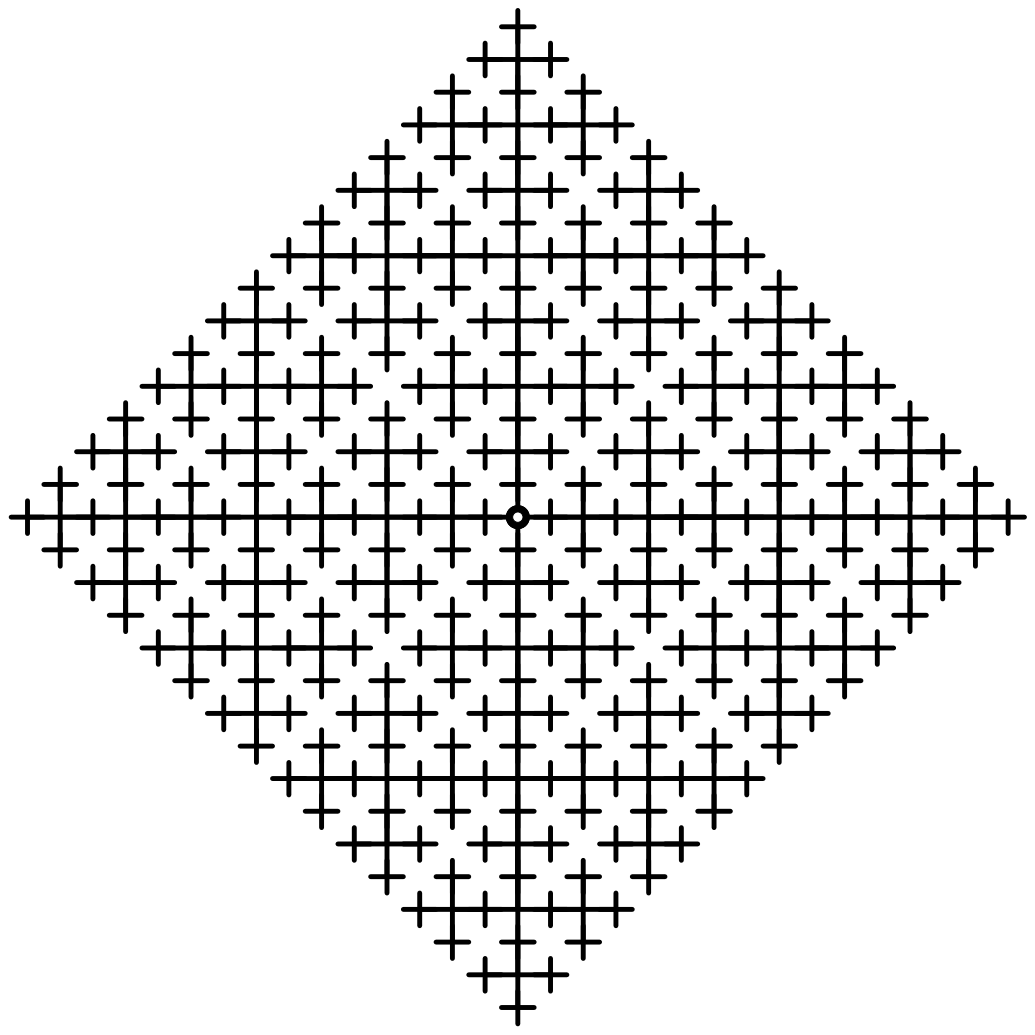
[picture p85: page 1]
