jensenr30/cad/eagle6/VU meter/VU Meter Silkscreen.pdf

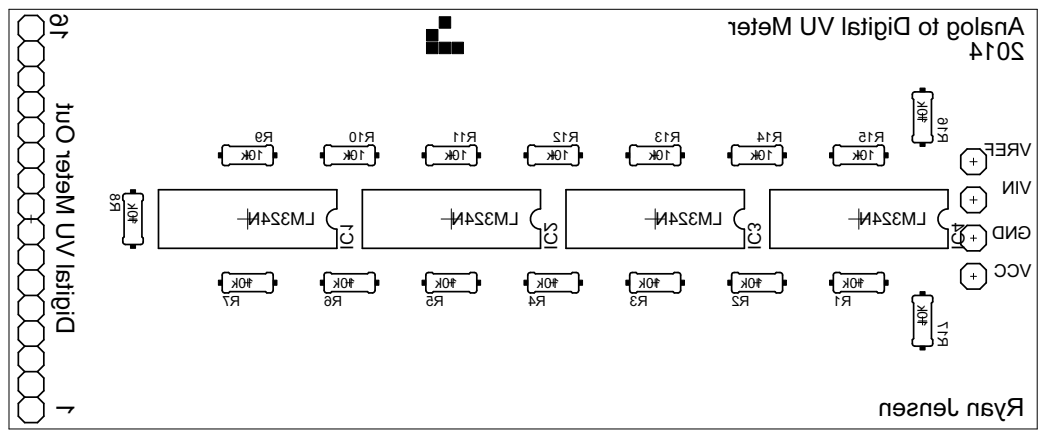
[picture p86: page 1]

N423 ML N423 ML N423 ML N423 ML k01 k01 k01 k01 k01 k01 k01 10k k01 k01 k01 k01 k01 k01 k01 10k 10k IC1 IC2 IC3 IC4 7R 6R 5R 4R 3R 2R 1R R8 9R 01R 11R 21R 31R 41R 51R R16 R17 FERV DNGNI V CCV Digital VU Meter Out 1 16r et e M UVl ati gi Dot gol anA 4102 nesneJ nay R
