jensenr30/cad/eagle6/VU meter/VU Meter.pdf

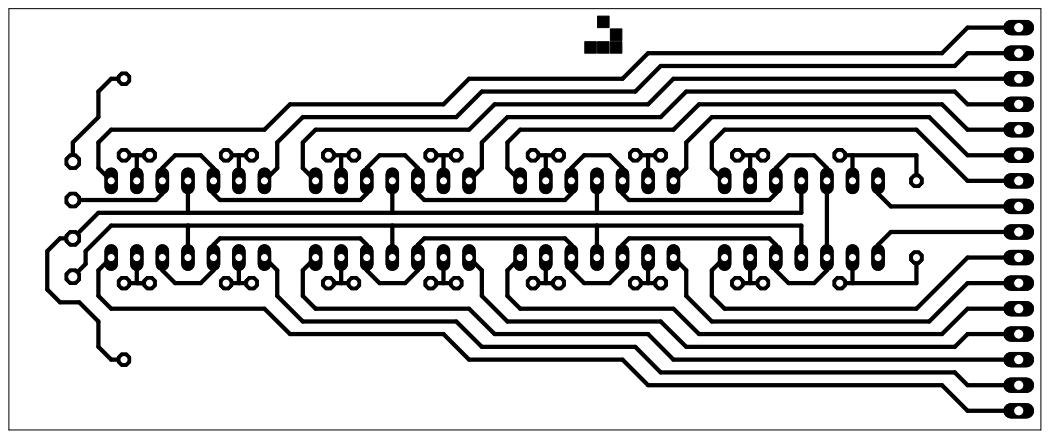
[picture p87: page 1]
