jensenr30/cad/kicad8/expression-pedal-to-pwm/Rev 1/Rev1.pdf

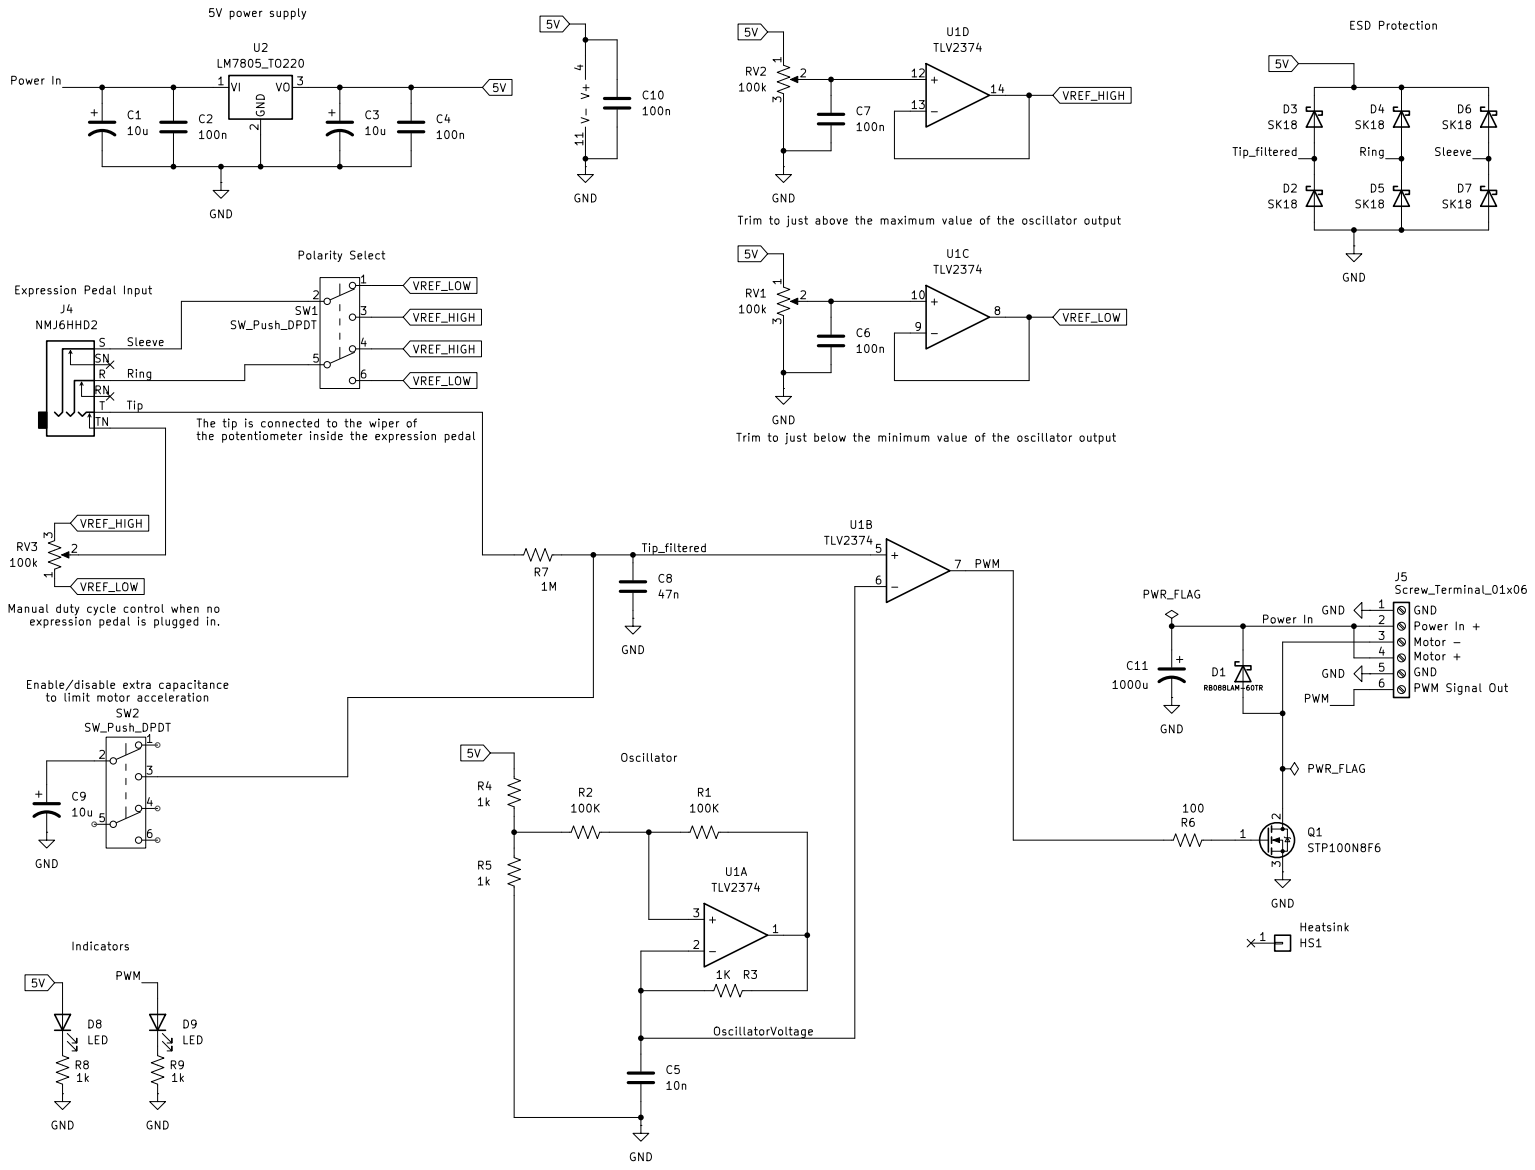
[picture p88: page 1]
