jensenr30/cad/eagle6/Analog Synth/Front Panels/Frequency Divider.pdf

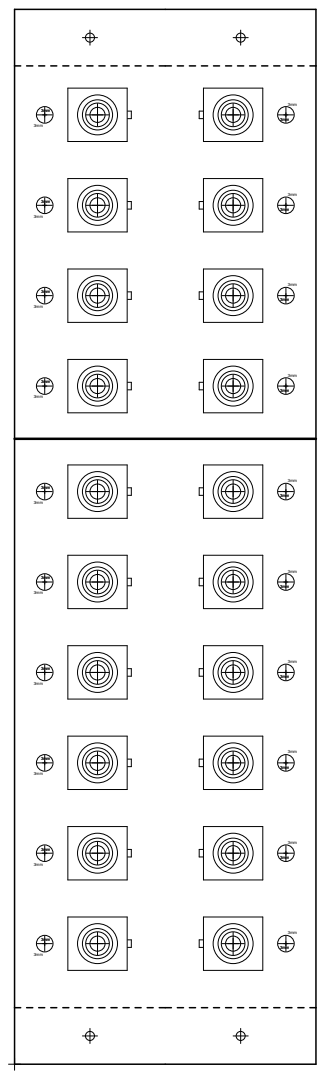
[picture p89: page 1]
