jensenr30/cad/eagle6/Analog Synth/Front Panels/Power Supply Panel.pdf

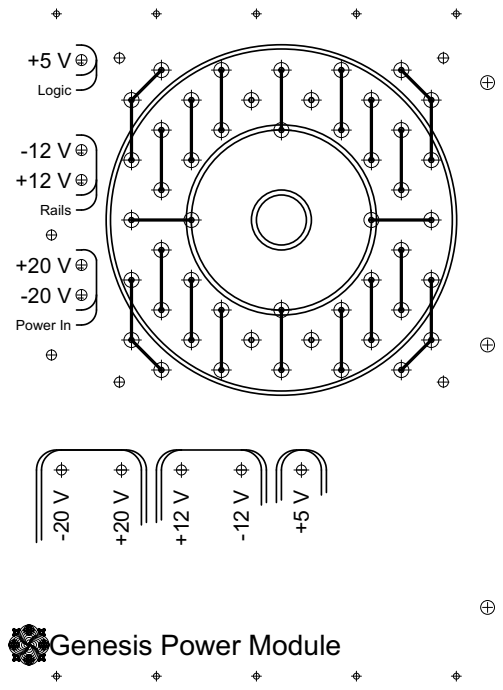
[picture p90: page 1]
