jensenr30/cad/eagle6/Analog Synth/Front Panels/VCA-v2.pdf

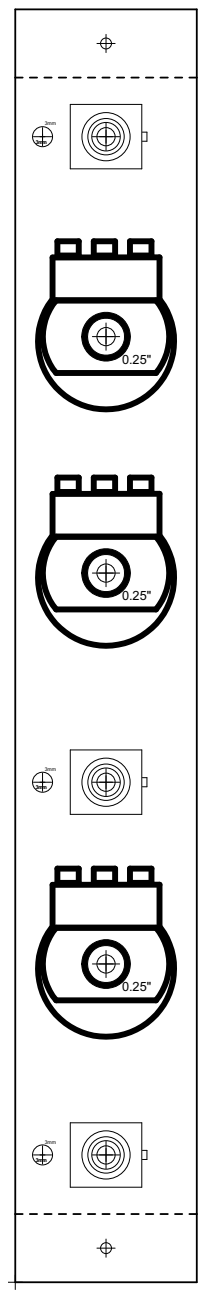
[picture p91: page 1]
