jensenr30/cad/eagle6/Analog Synth/PS-VCO/PS-VCO PCB.pdf

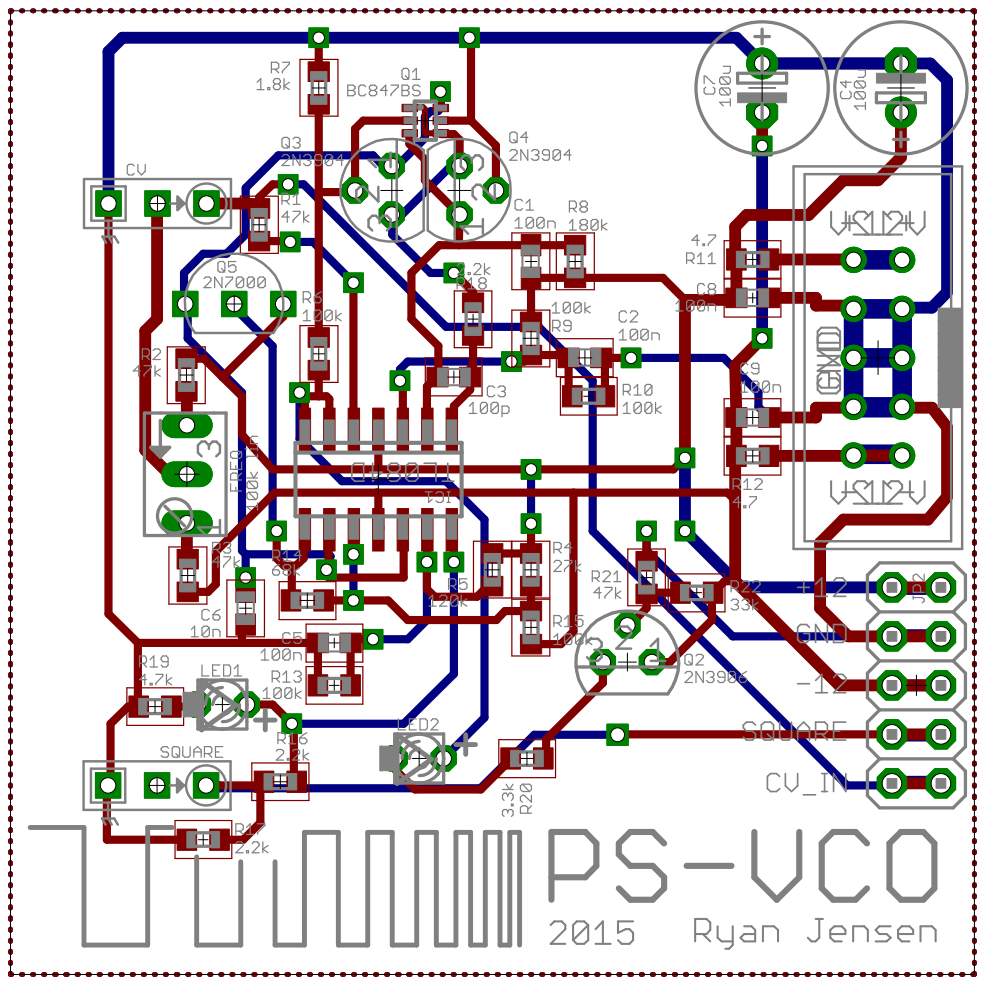
[picture p92: page 1]
