jensenr30/cad/eagle6/Analog Synth/PS-VCO/PS-VCO SCH.pdf

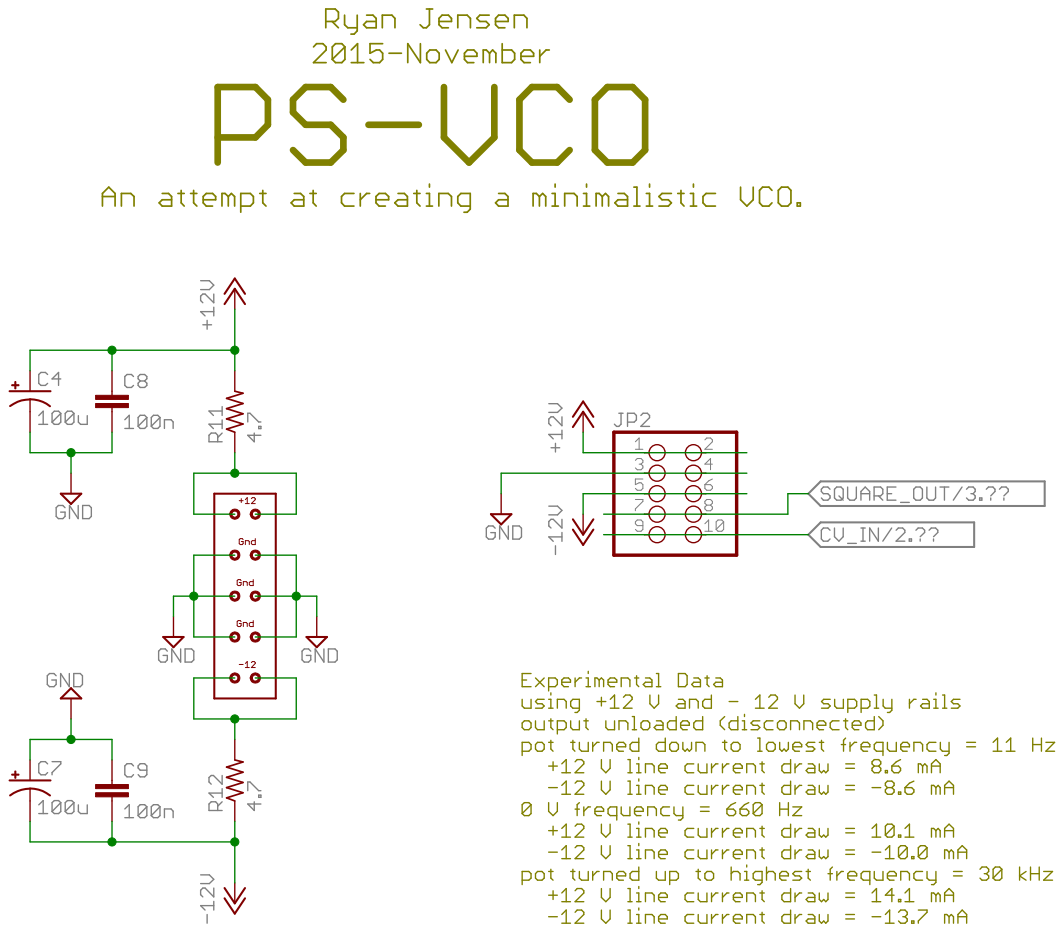
[picture p93: page 1]

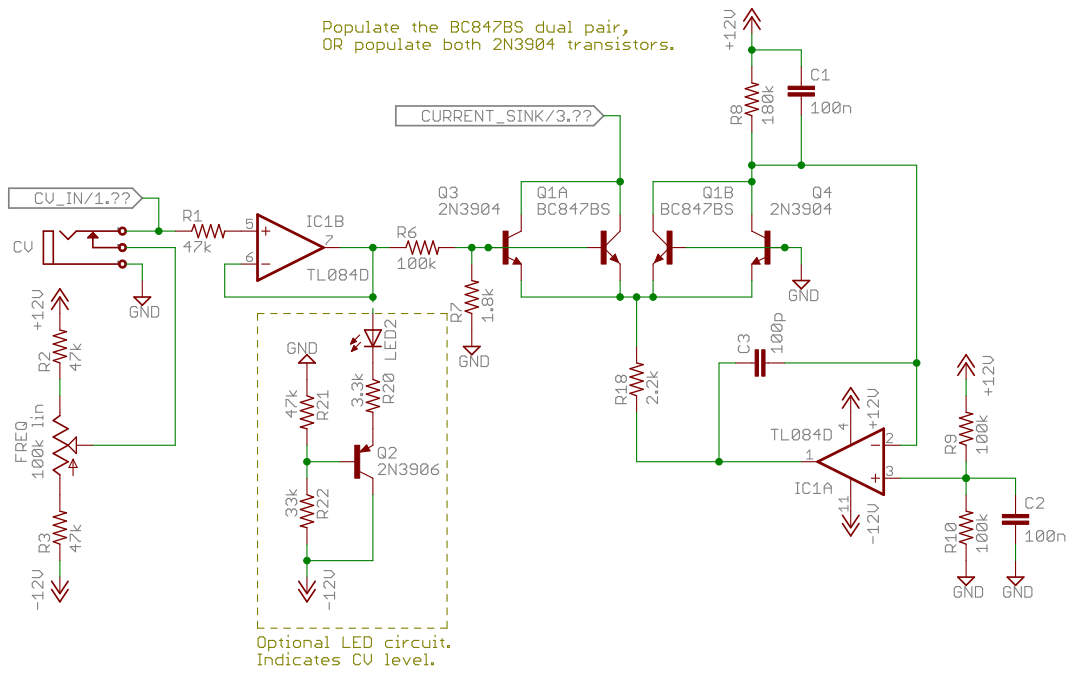
[picture p94: page 2]

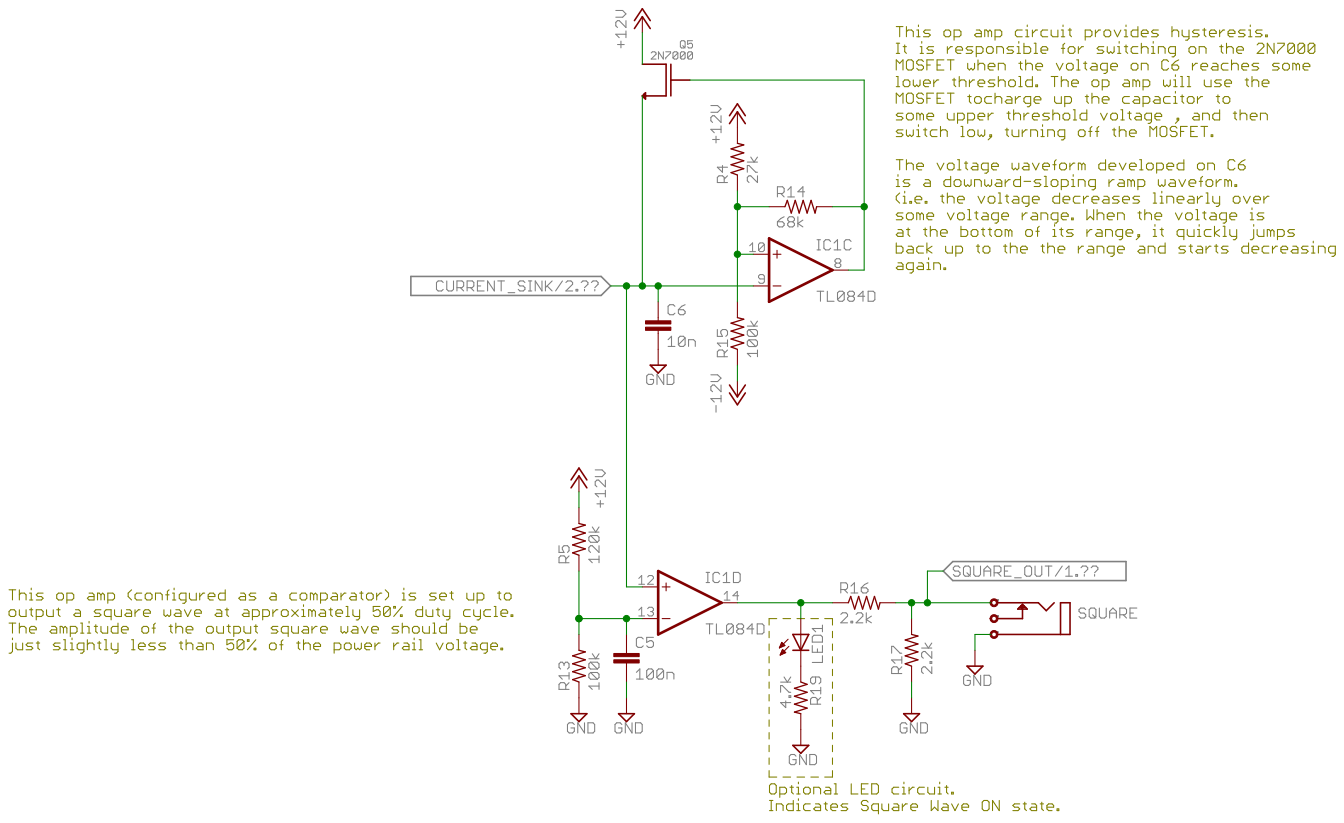
[picture p95: page 3]
