jensenr30/cad/eagle6/Analog Synth/PS-VCO/PS-VCO.pdf

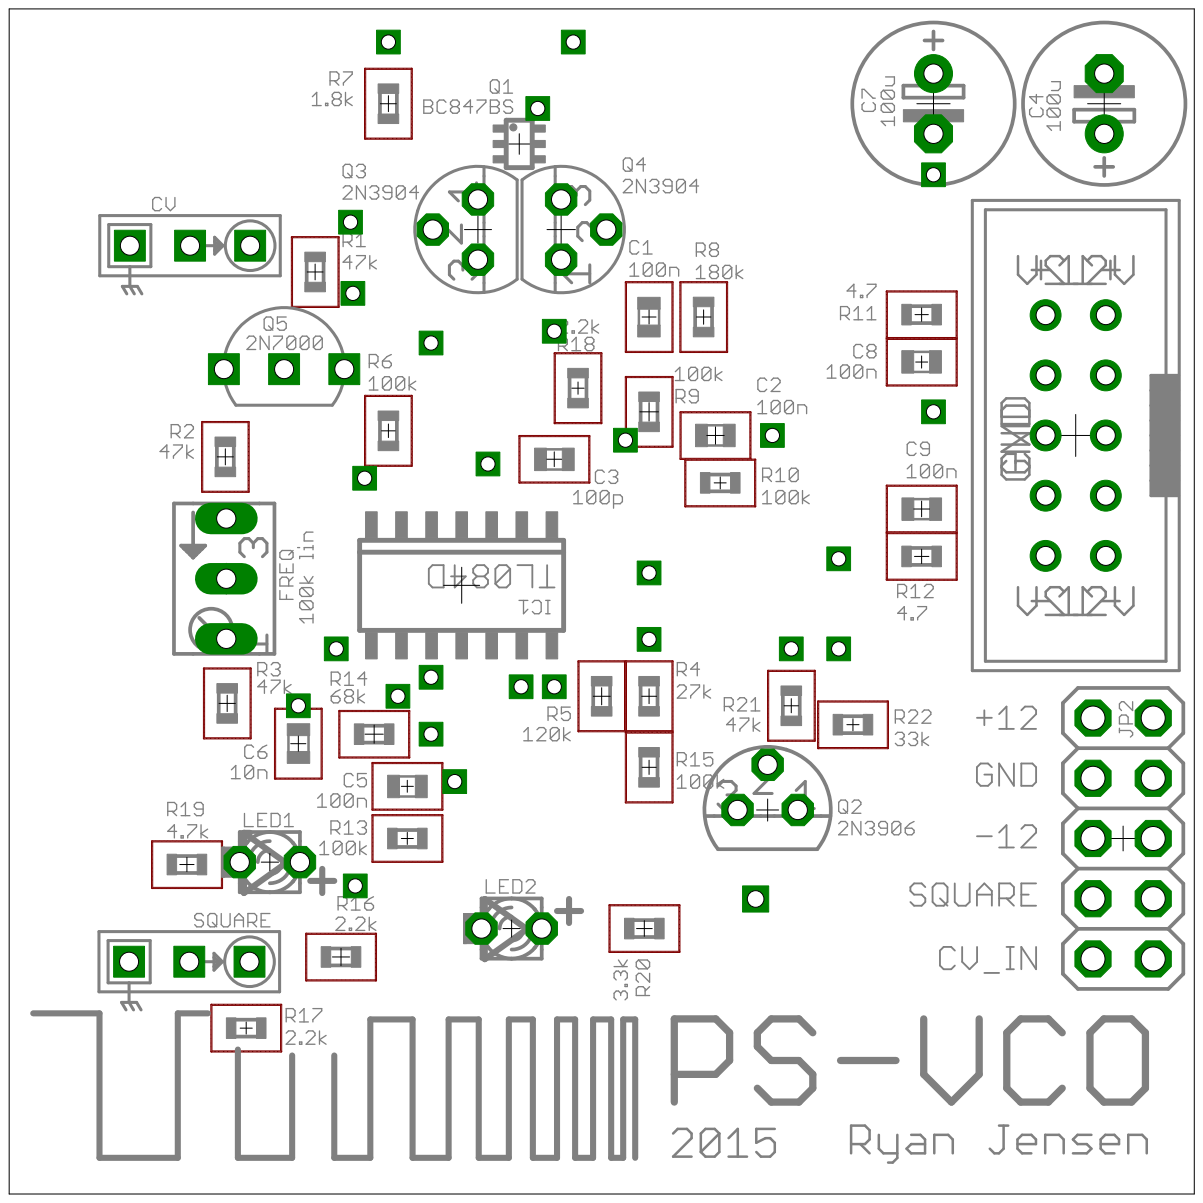
[picture p96: page 1]
