jensenr30/cad/eagle6/Analog Synth/ScreamFilter/ScreamFilter Back Copper.pdf

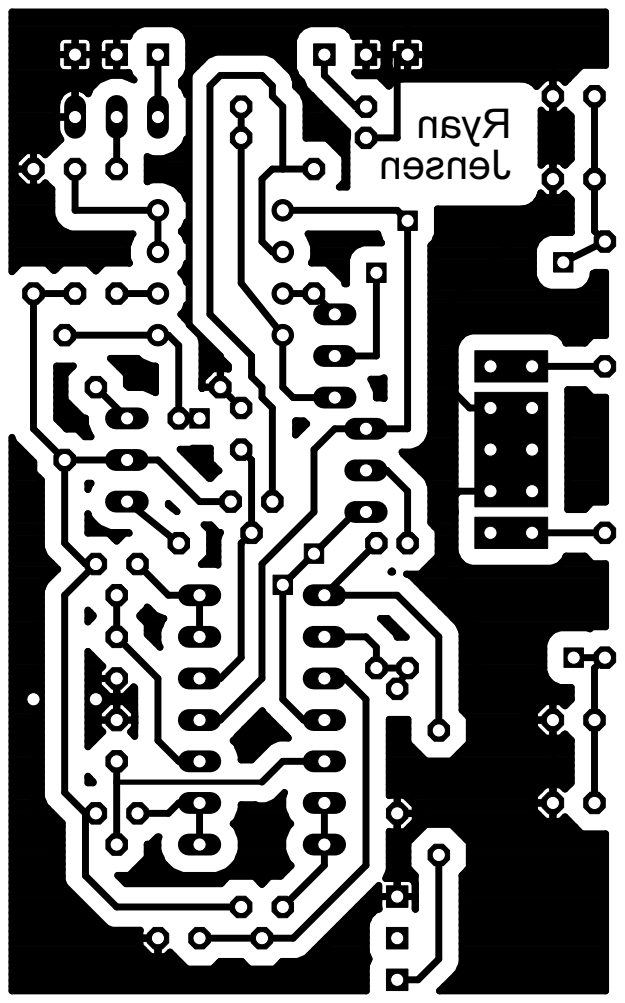
[picture p97: page 1]
