jensenr30/cad/eagle6/Analog Synth/ScreamFilter/ScreamFilter Front SilkScreen.pdf

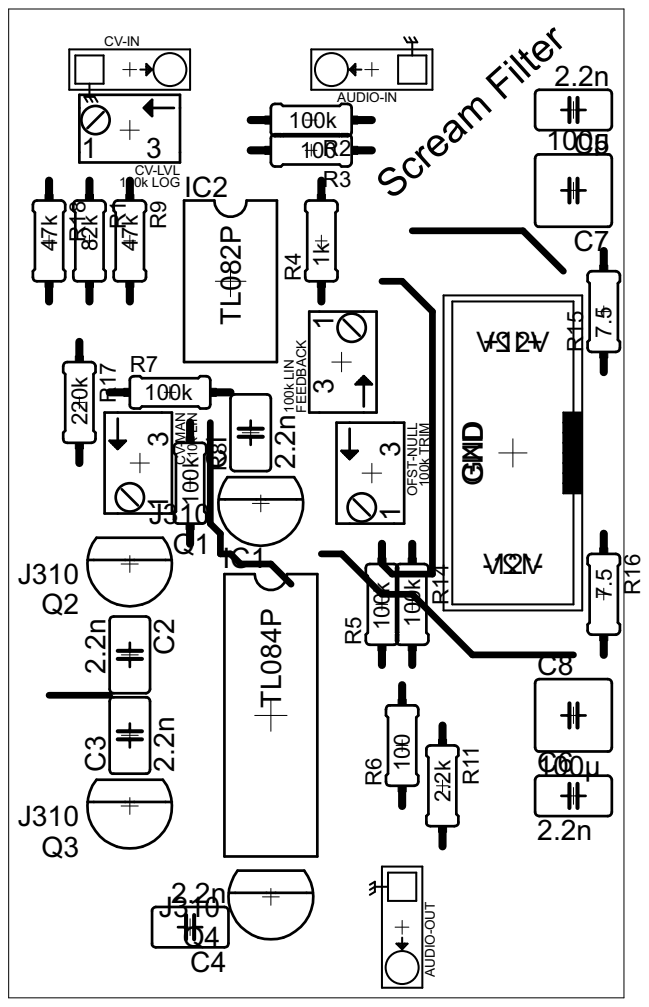
[picture p98: page 1]
