jensenr30/cad/eagle6/Analog Synth/ScreamFilter/ScreamFilter v1.1.pdf

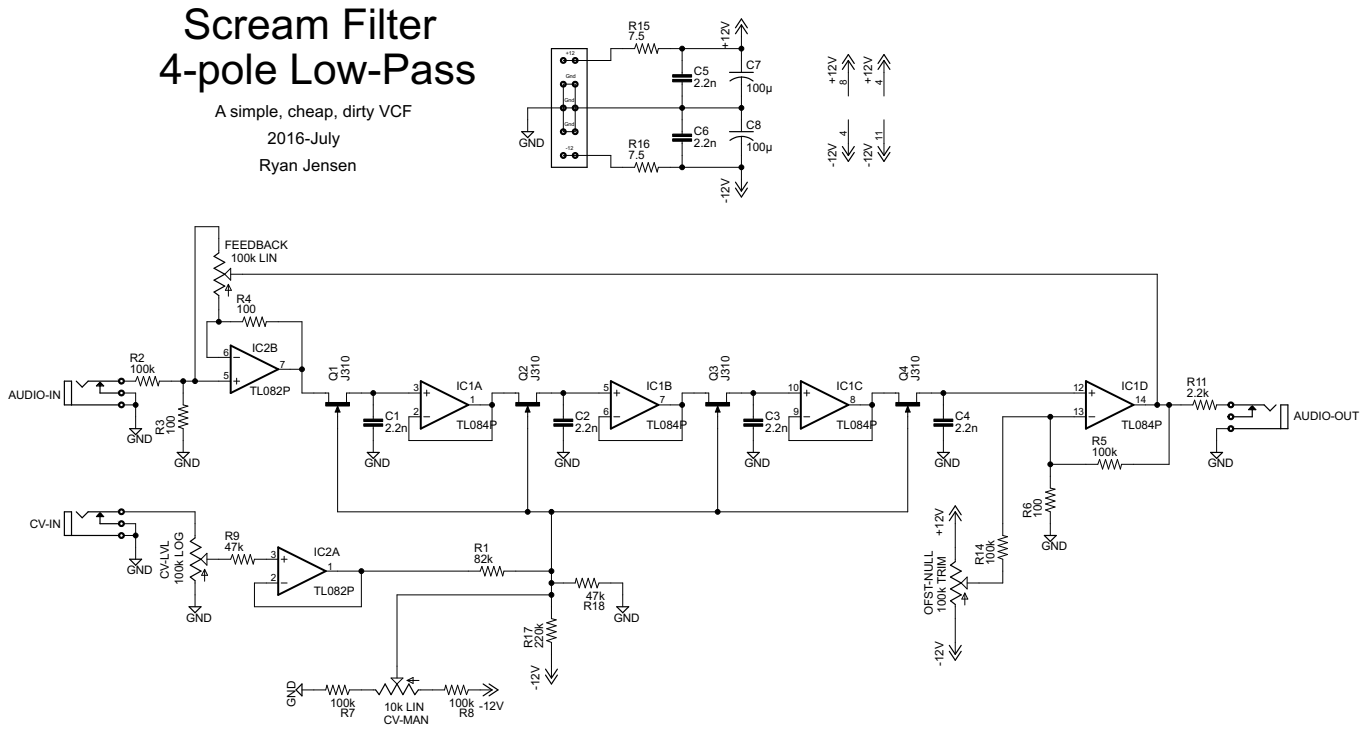
[picture p99: page 1]
