jensenr30/cad/eagle6/Analog Synth/VCA-v2/VCA-v2.1 ASY BLACK.pdf

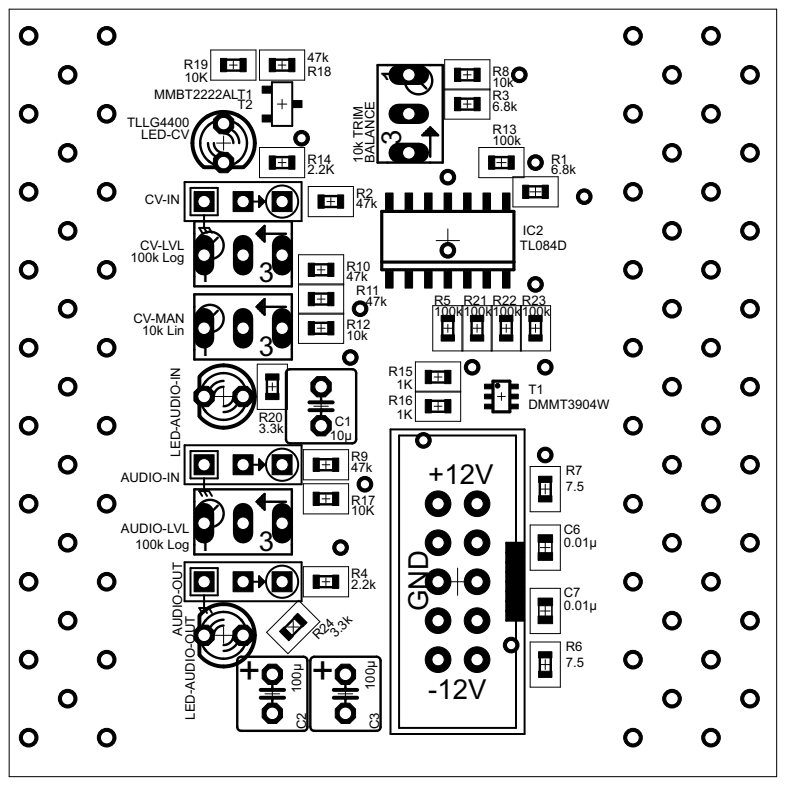
[picture p100: page 1]
