jensenr30/cad/eagle6/Analog Synth/VCA-v2/VCA-v2.1 ASY.pdf

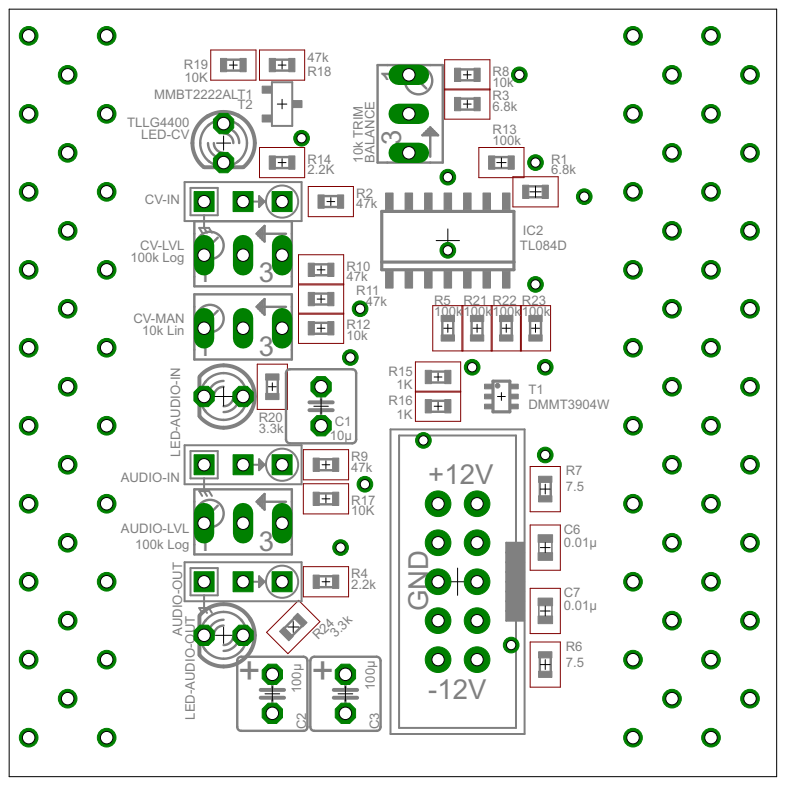
[picture p101: page 1]
