jensenr30/cad/eagle6/Analog Synth/VCO-v2/VCO-v2.2.pdf

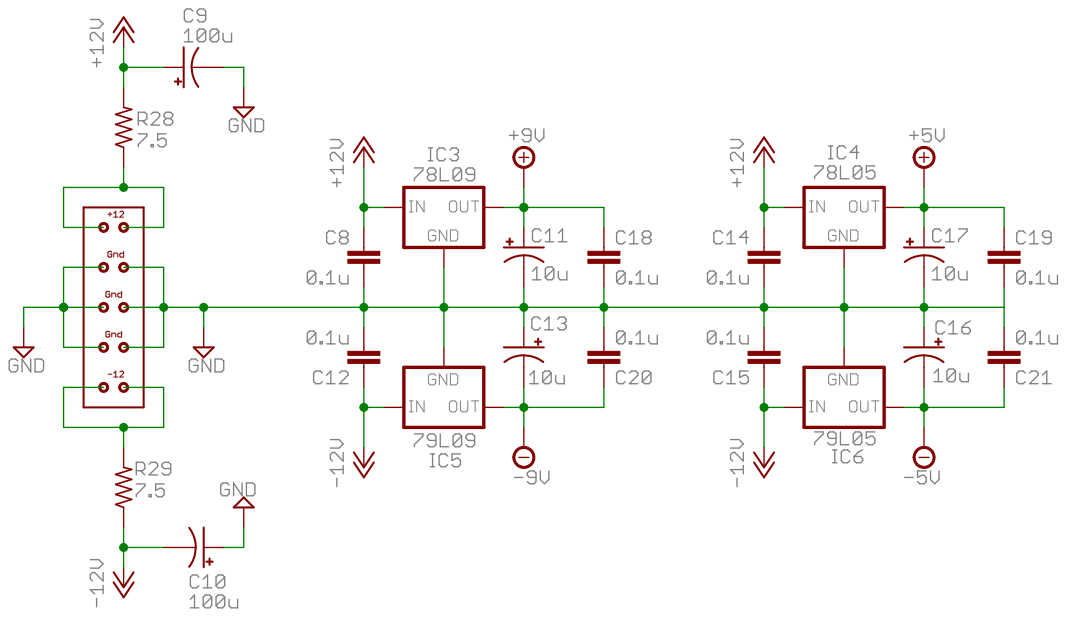
[picture p102: page 1]

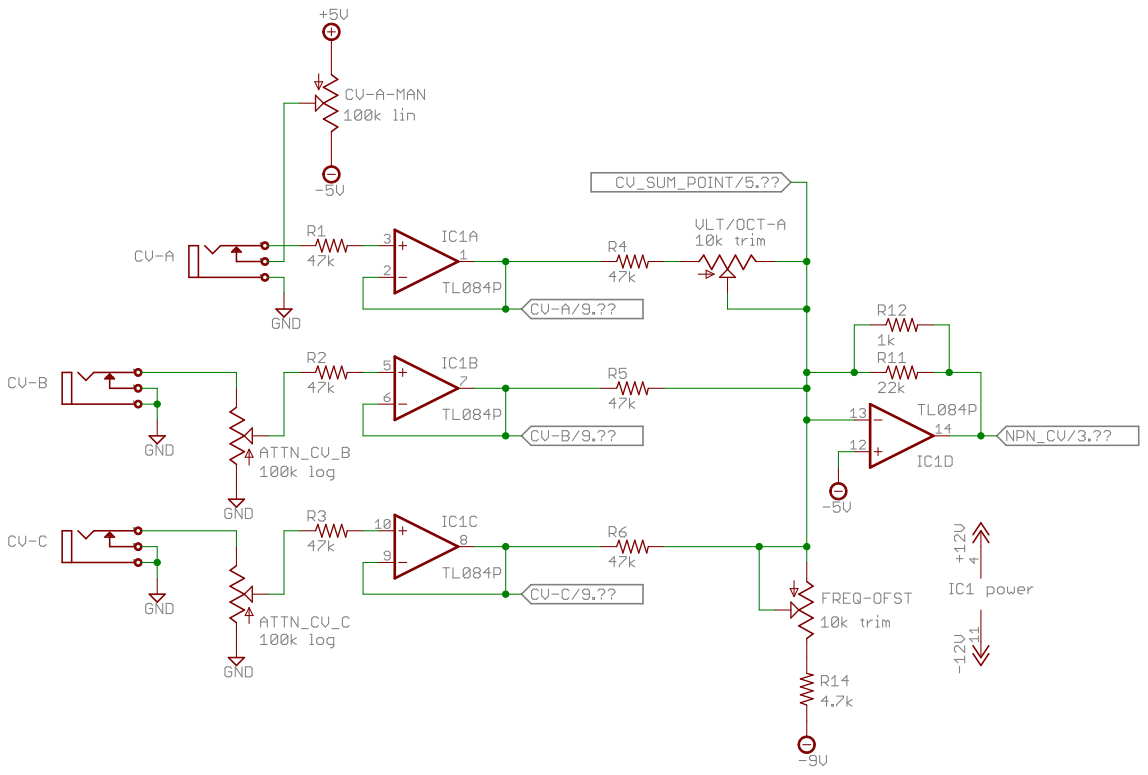
[picture p103: page 2]

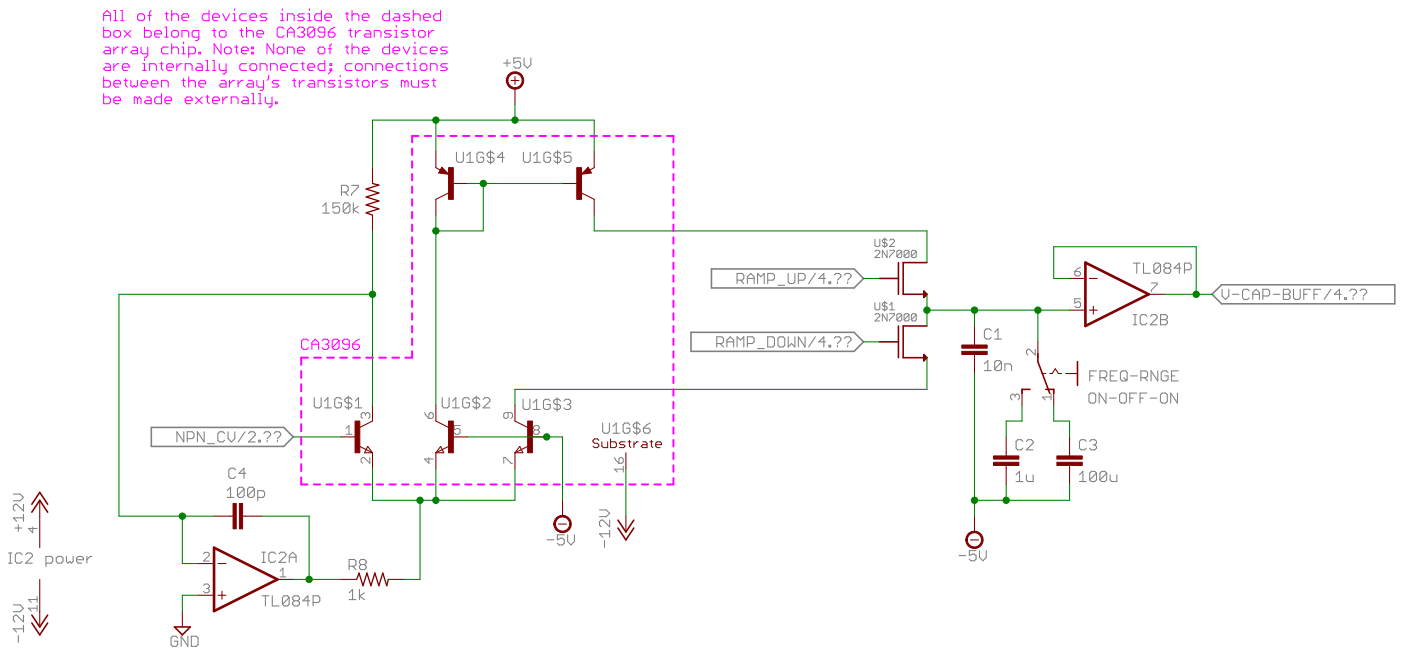
[picture p104: page 3]

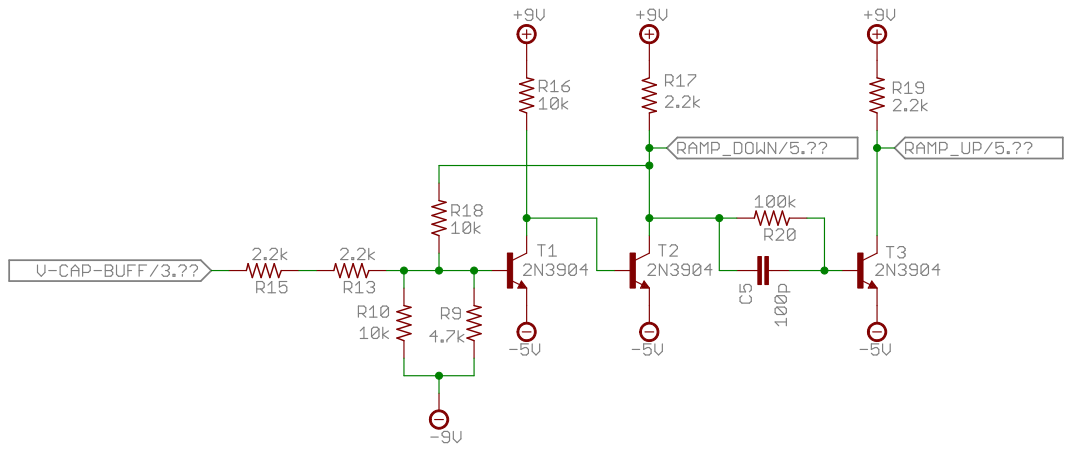
[picture p105: page 4]

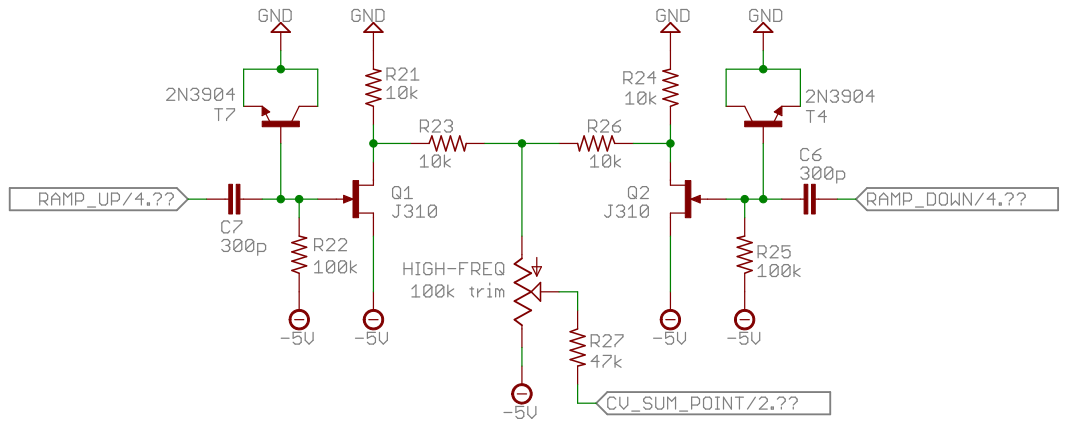
[picture p106: page 5]

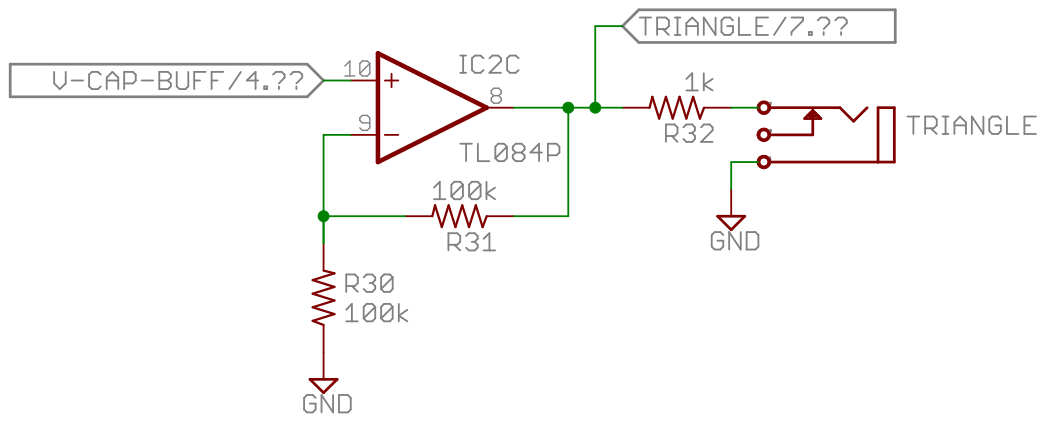
[picture p107: page 6]

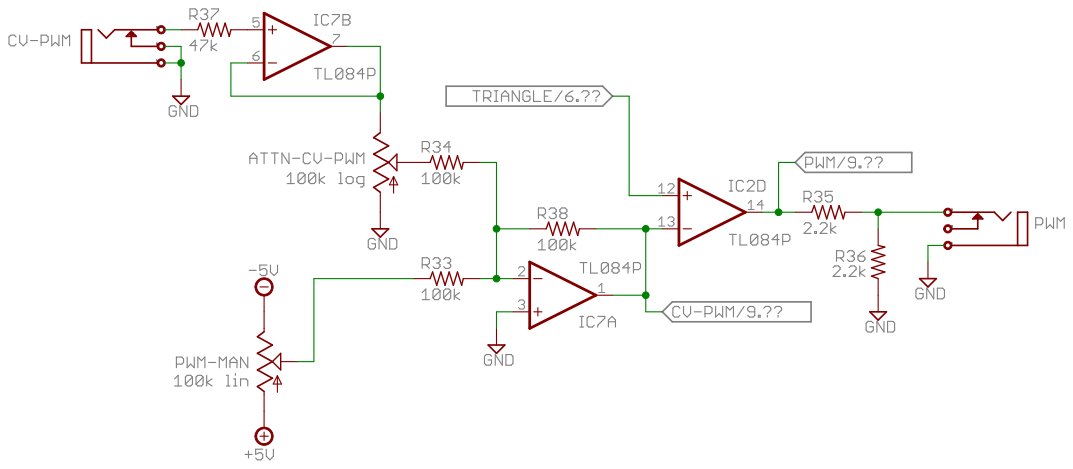
[picture p108: page 7]

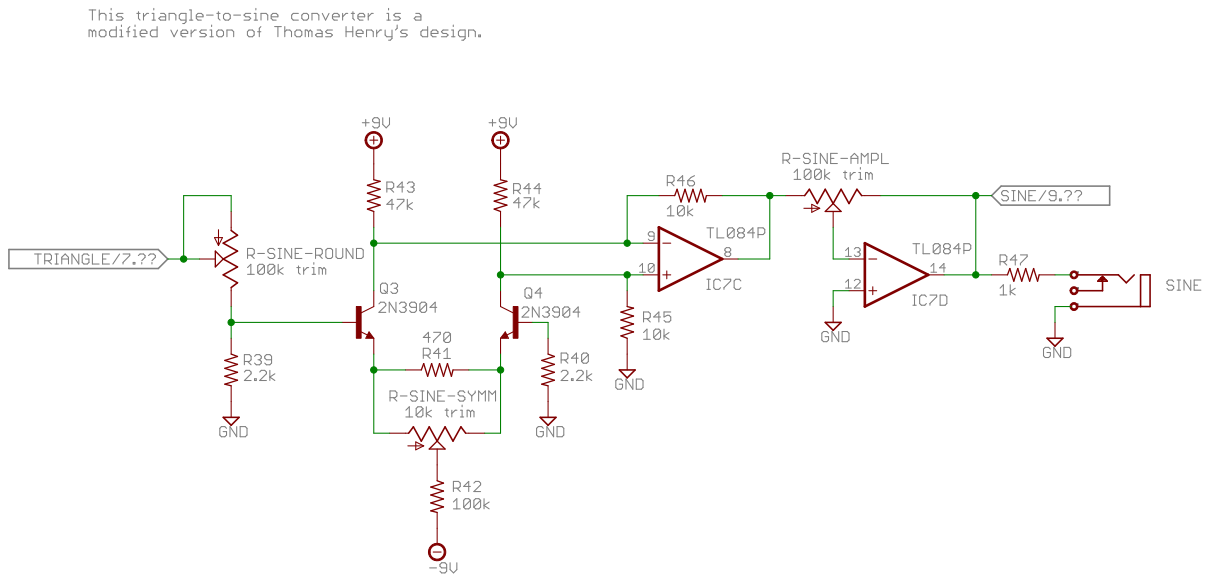
[picture p109: page 8]

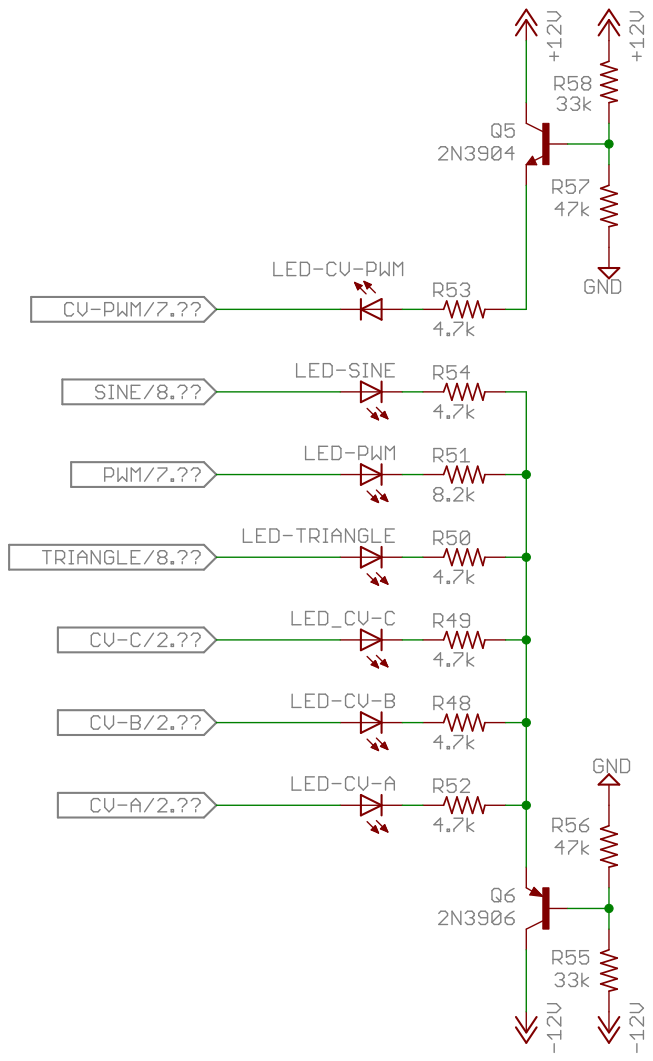
[picture p110: page 9]
