jensenr30/cad/kicad4/XPhone/Input_Board/gerbers/Input Board-B.Cu.pdf

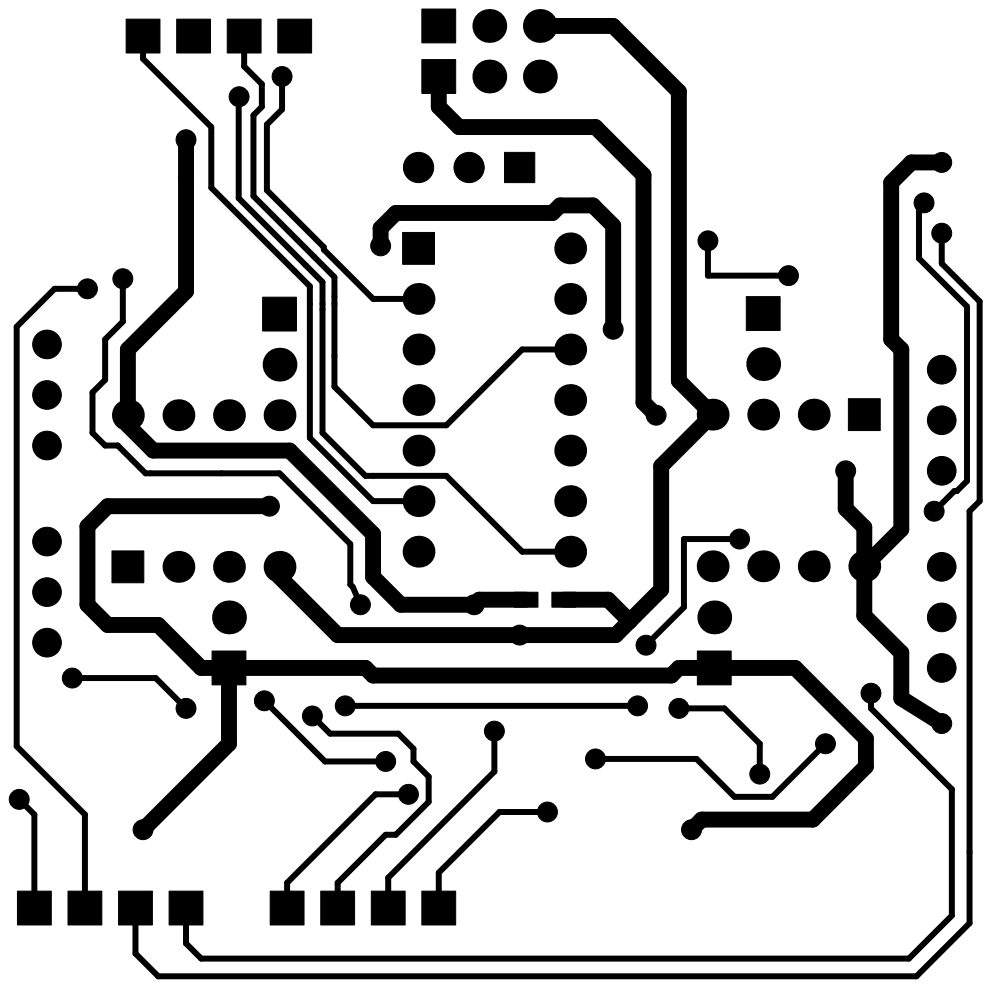
[picture p111: page 1]
