jensenr30/cad/kicad4/XPhone/Input_Board/gerbers/Input Board-B.Fab.pdf

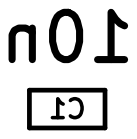
[picture p112: page 1]
