jensenr30/cad/kicad4/XPhone/Input_Board/gerbers/Input Board-B.Mask.pdf

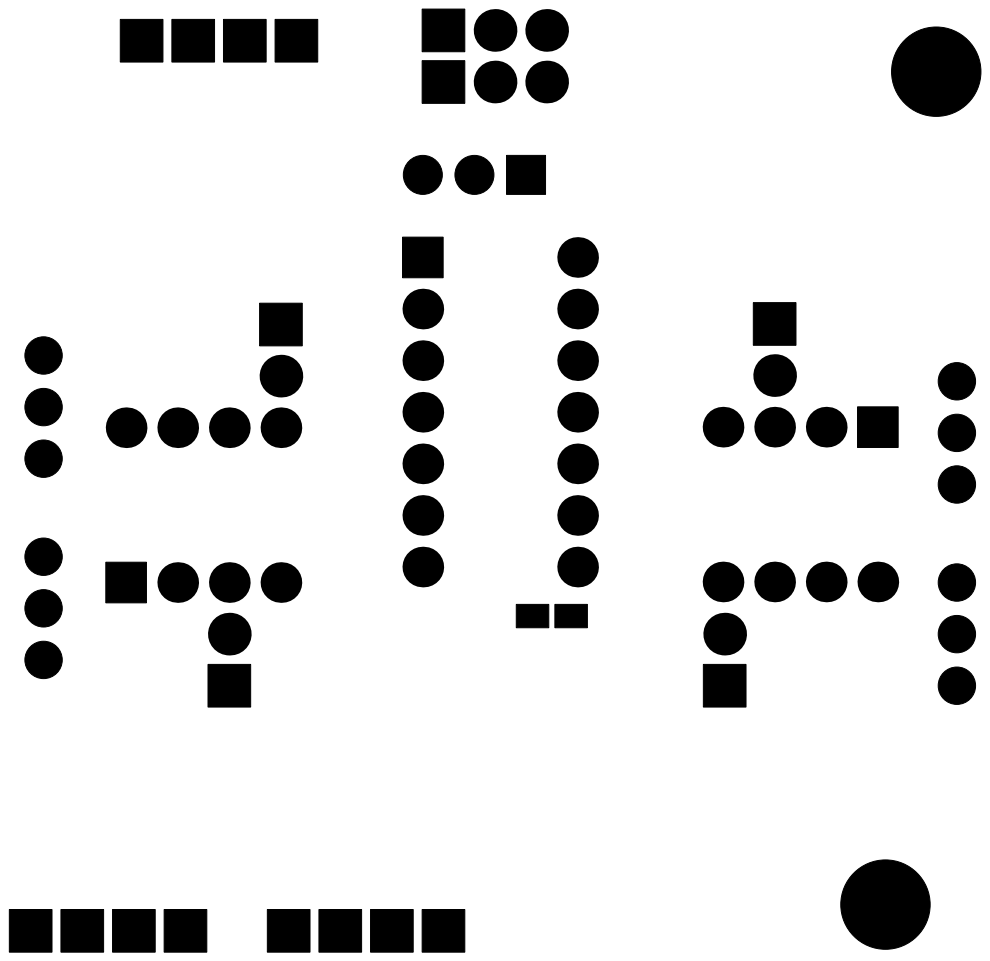
[picture p113: page 1]
