jensenr30/cad/kicad4/XPhone/Input_Board/gerbers/Input Board-B.SilkS.pdf

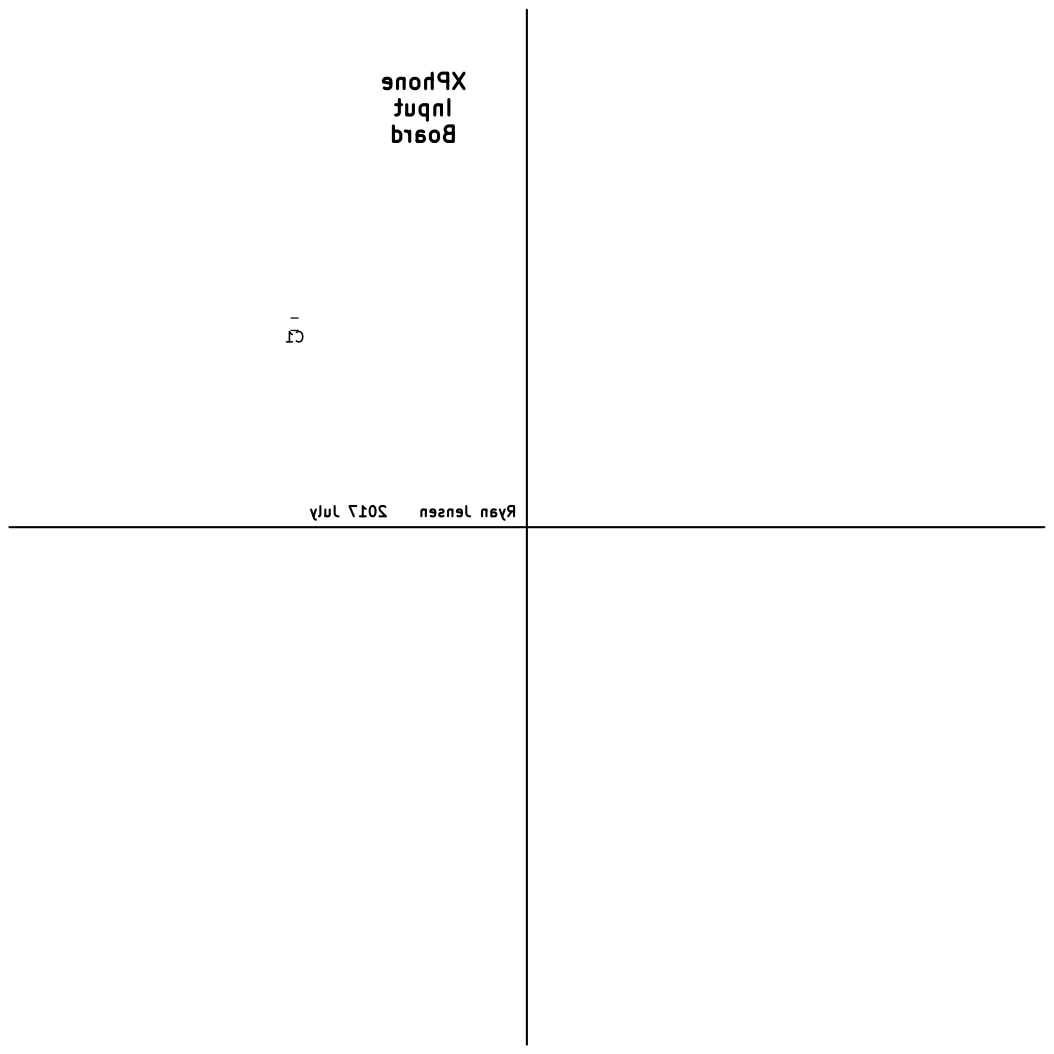
[picture p114: page 1]

Ryan Jensen 2017 July XPhone
