jensenr30/cad/kicad4/XPhone/Input_Board/gerbers/Input Board-F.Cu.pdf

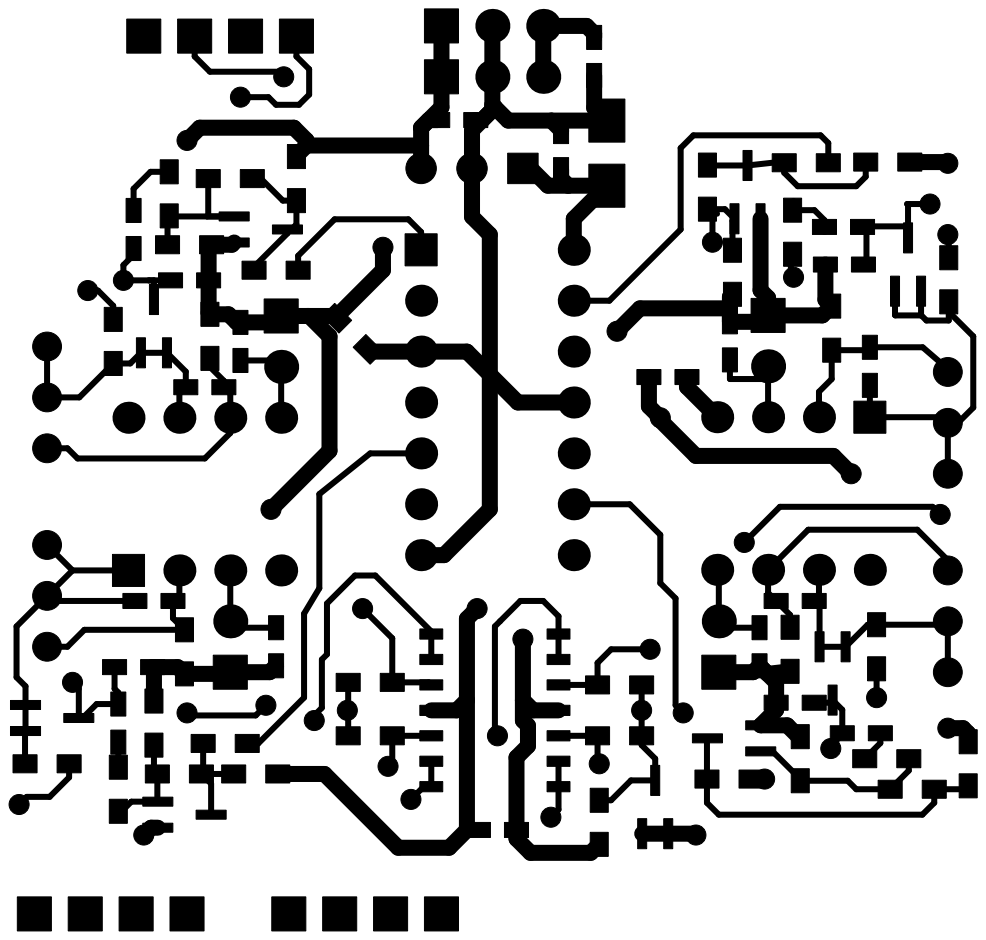
[picture p115: page 1]
