jensenr30/cad/kicad4/XPhone/Input_Board/gerbers/Input Board-F.Fab.pdf

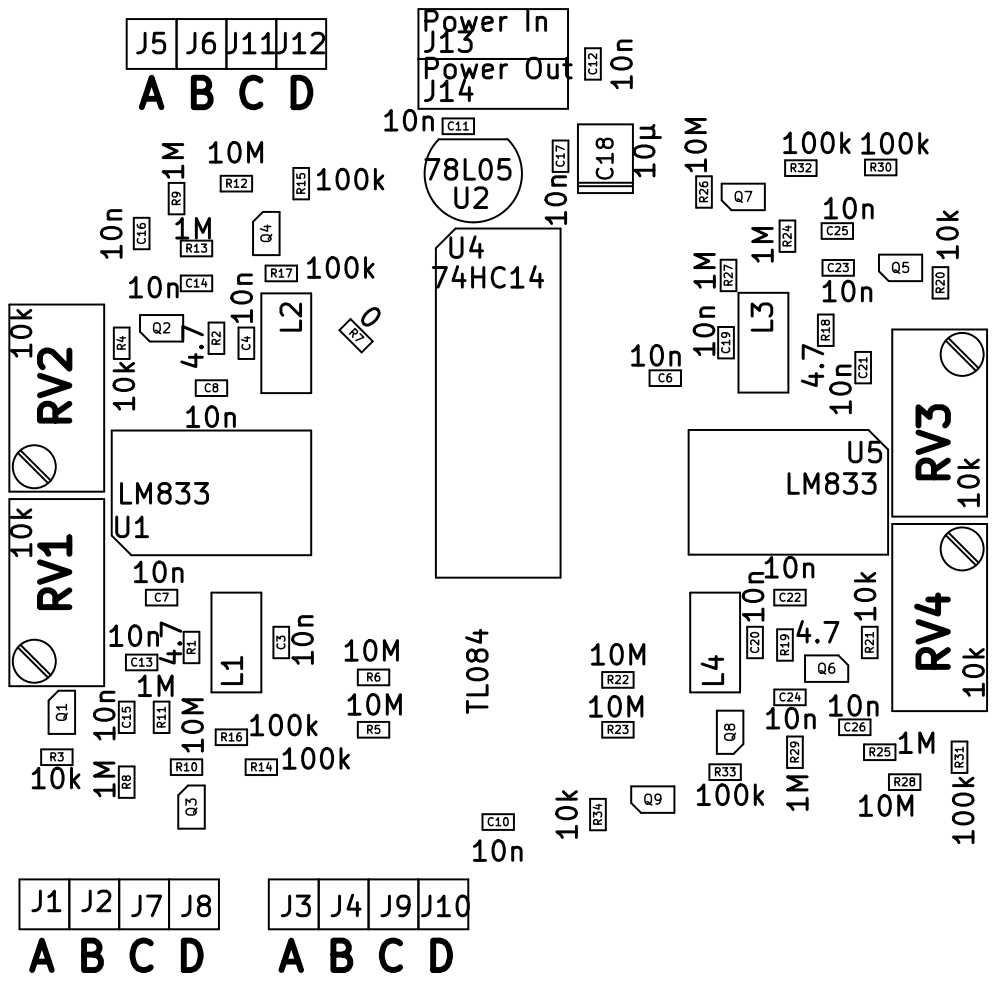
[picture p116: page 1]
