jensenr30/cad/kicad4/XPhone/Input_Board/gerbers/Input Board-F.Mask.pdf

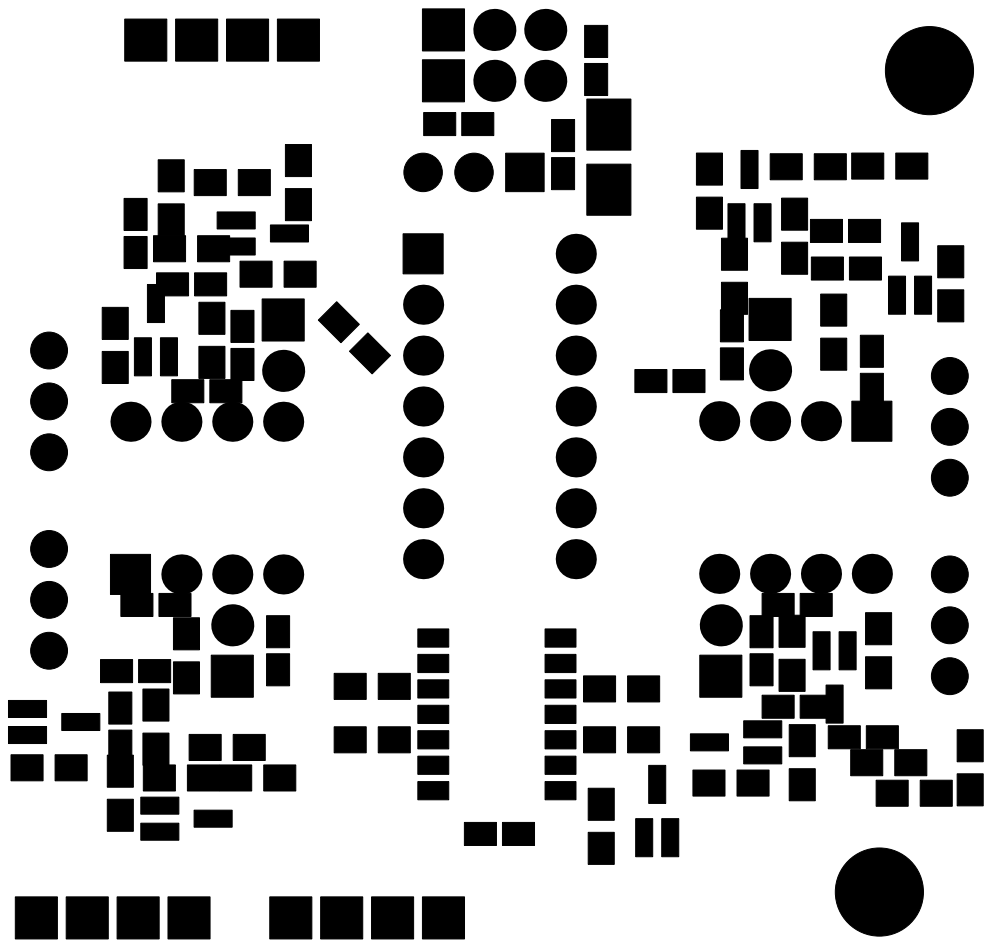
[picture p117: page 1]
