jensenr30/cad/kicad4/XPhone/Input_Board/gerbers/Input Board-F.SilkS.pdf

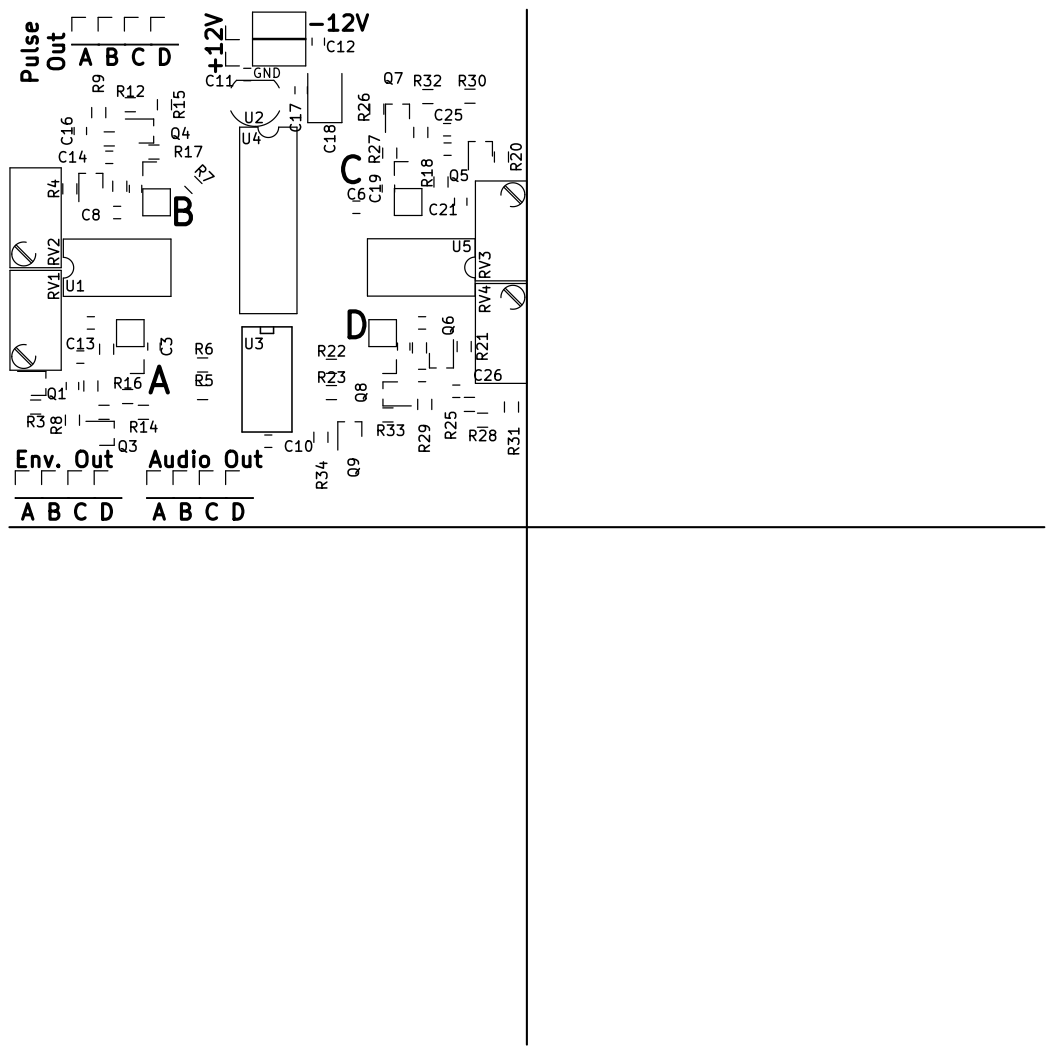
[picture p118: page 1]
