jensenr30/cad/kicad4/SRBOB/gerbers/pdfs/SRBOB-B.Cu.pdf

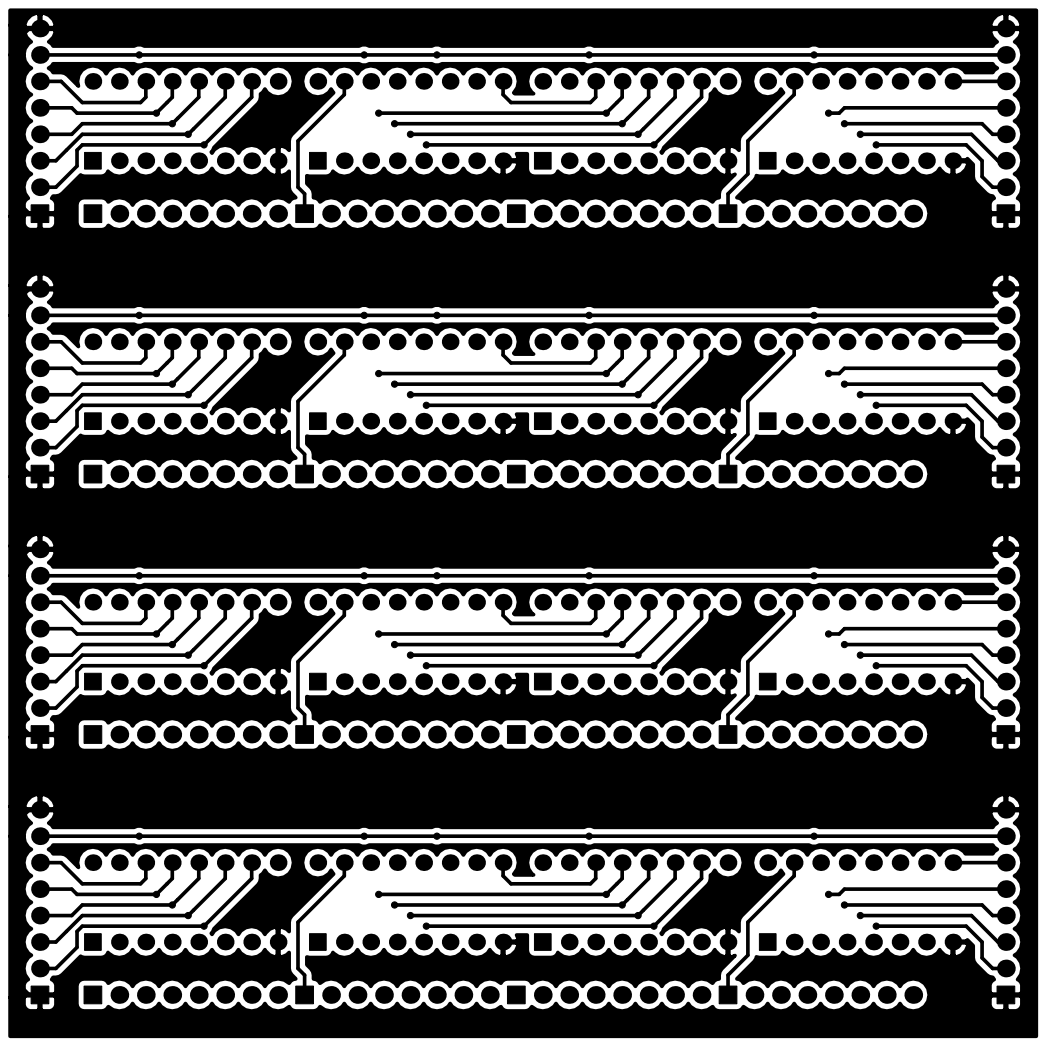
[picture p119: page 1]
