jensenr30/cad/kicad4/SRBOB/gerbers/pdfs/SRBOB-B.Mask.pdf

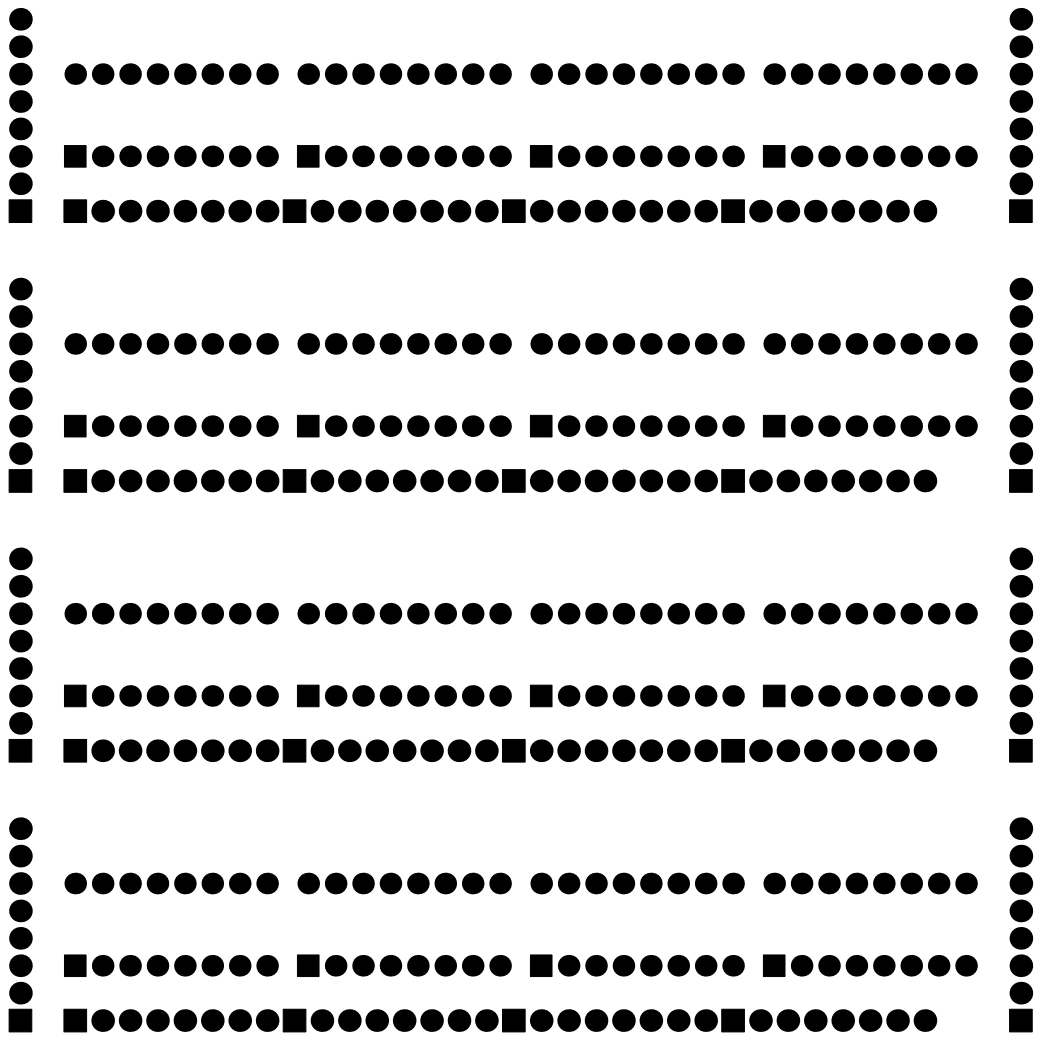
[picture p120: page 1]
