jensenr30/cad/kicad4/SRBOB/gerbers/pdfs/SRBOB-F.Cu.pdf

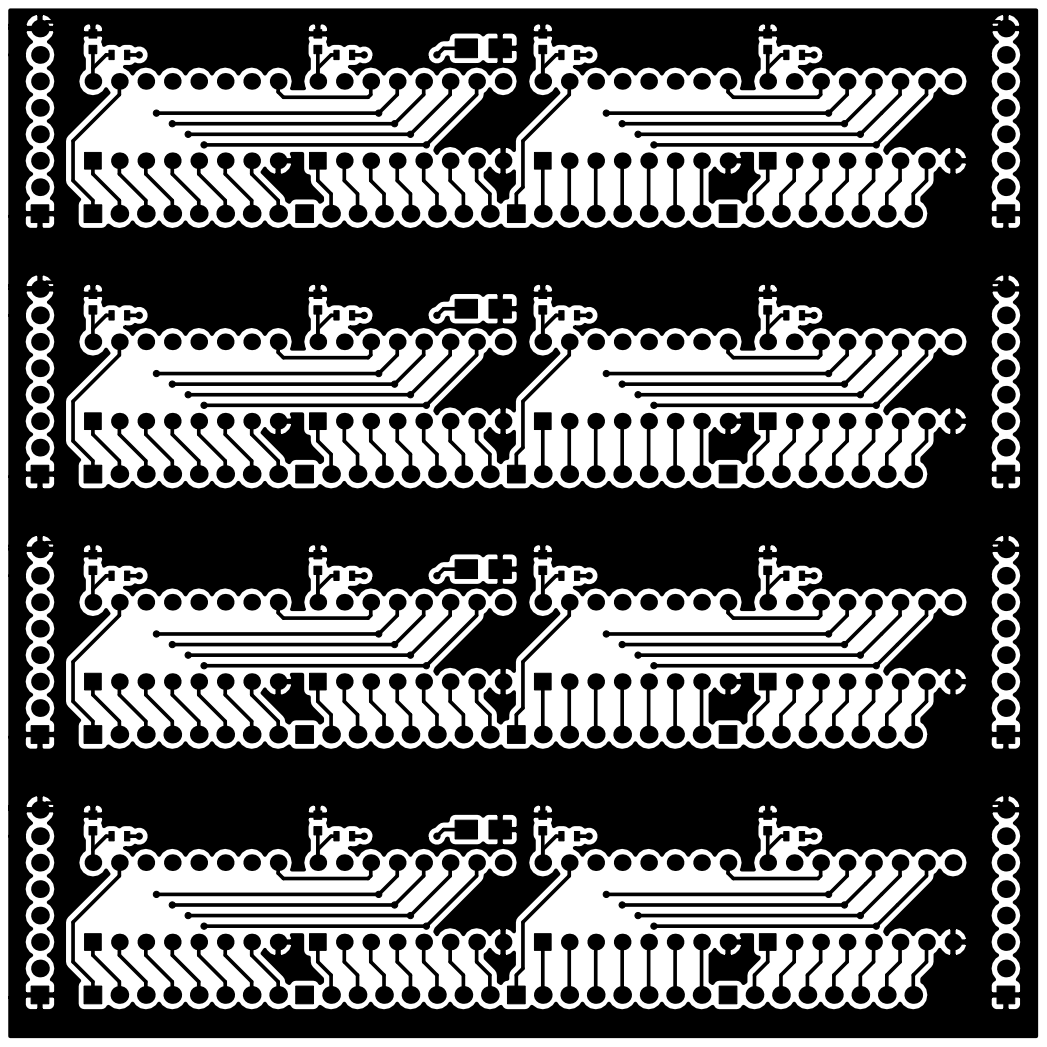
[picture p121: page 1]
