jensenr30/cad/kicad4/SRBOB/gerbers/pdfs/SRBOB-F.Mask.pdf

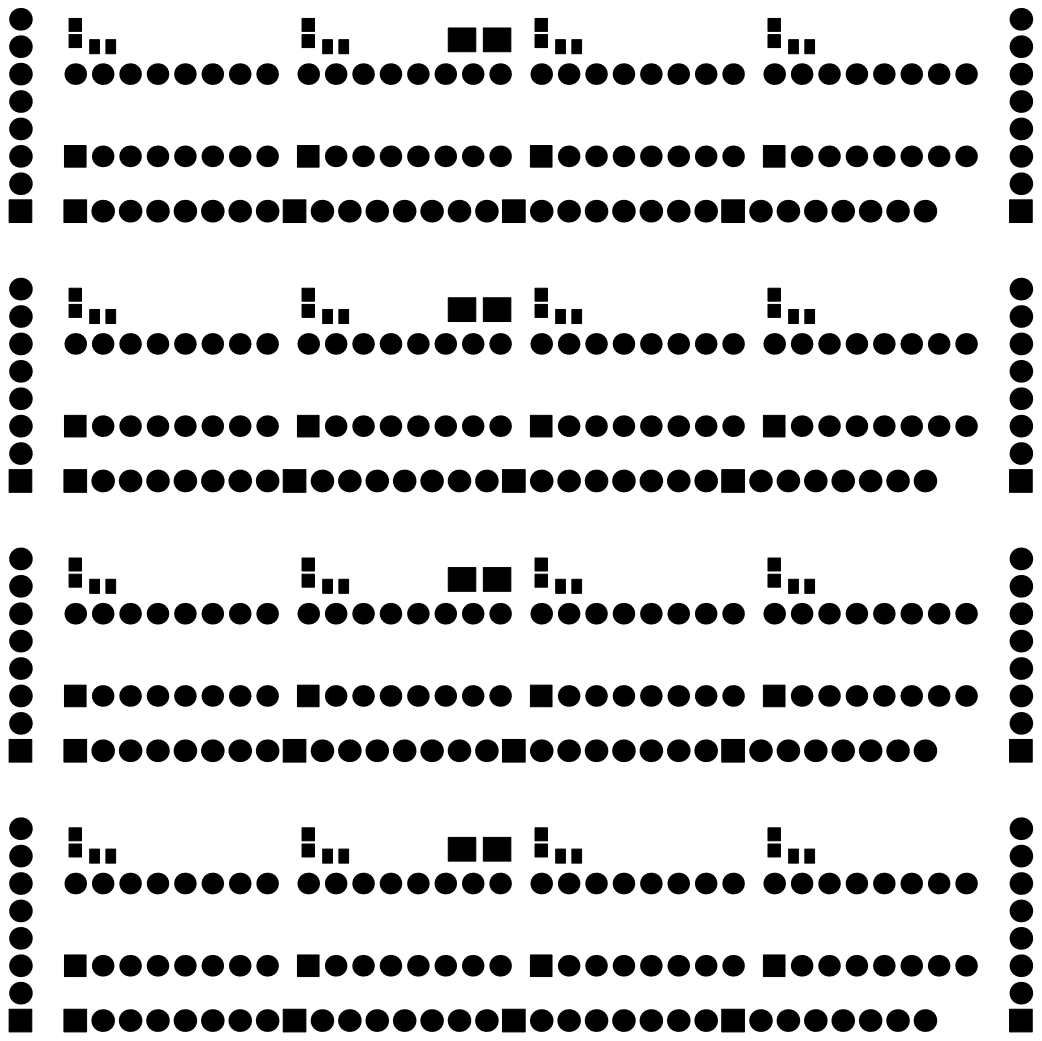
[picture p122: page 1]
