jensenr30/cad/eagle6/Prototype Boards/breakout board pack 1/panelized/pdf exports/BOT breakout1_laid_out.pdf

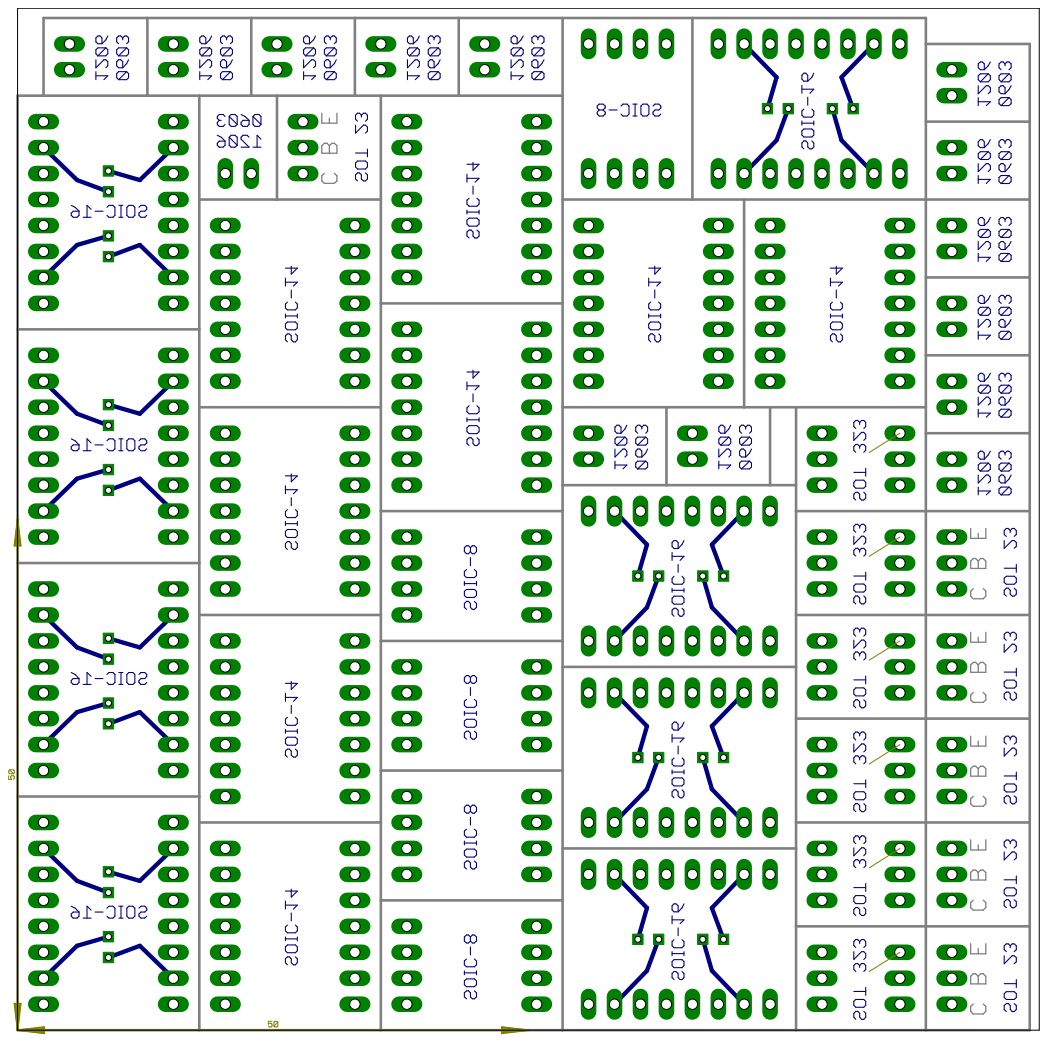
[picture p123: page 1]
