jensenr30/cad/eagle6/Prototype Boards/breakout board pack 1/panelized/pdf exports/TOP breakout1_laid_out.pdf

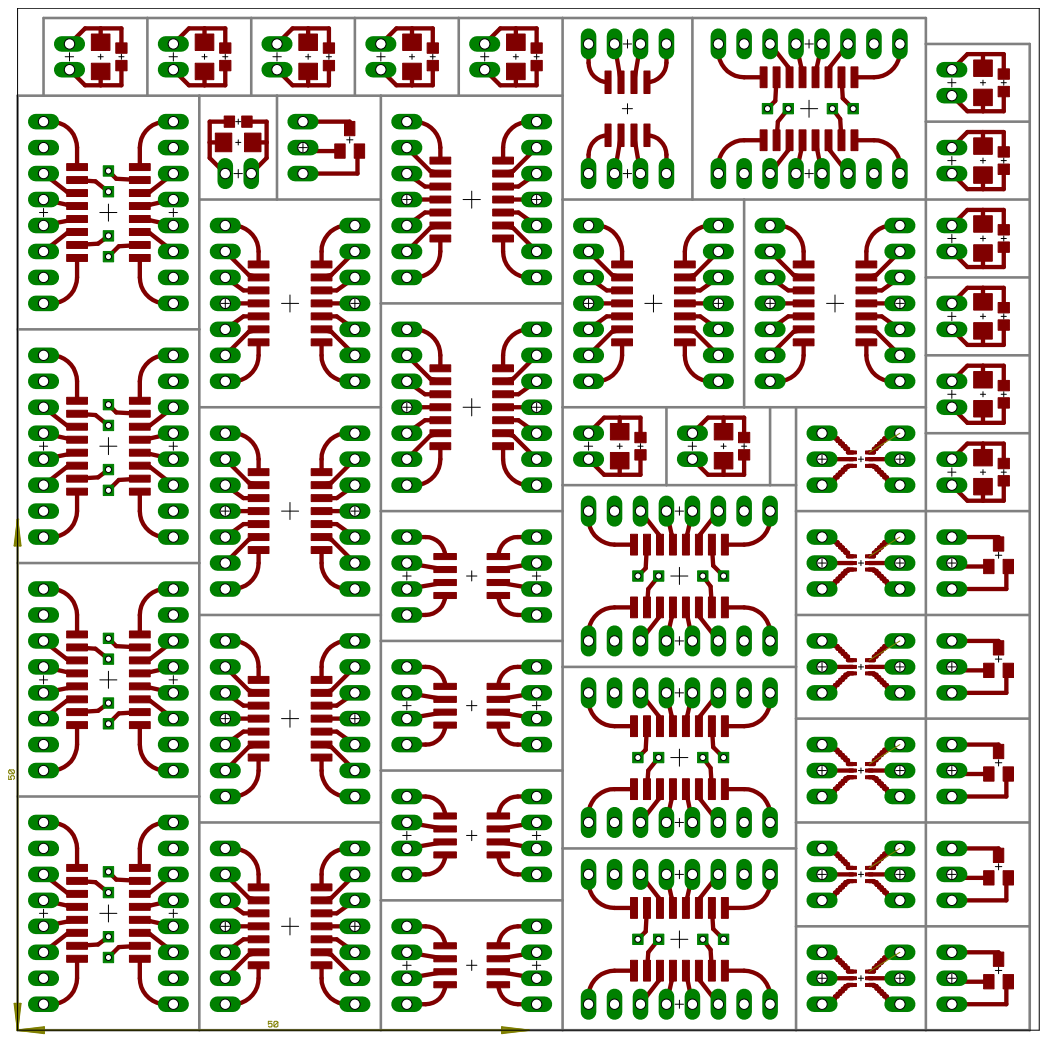
[picture p124: page 1]
