jensenr30/cad/kicad4/XPhone/Input_Board/gerbers/panel/Input Board-B.Cu.pdf

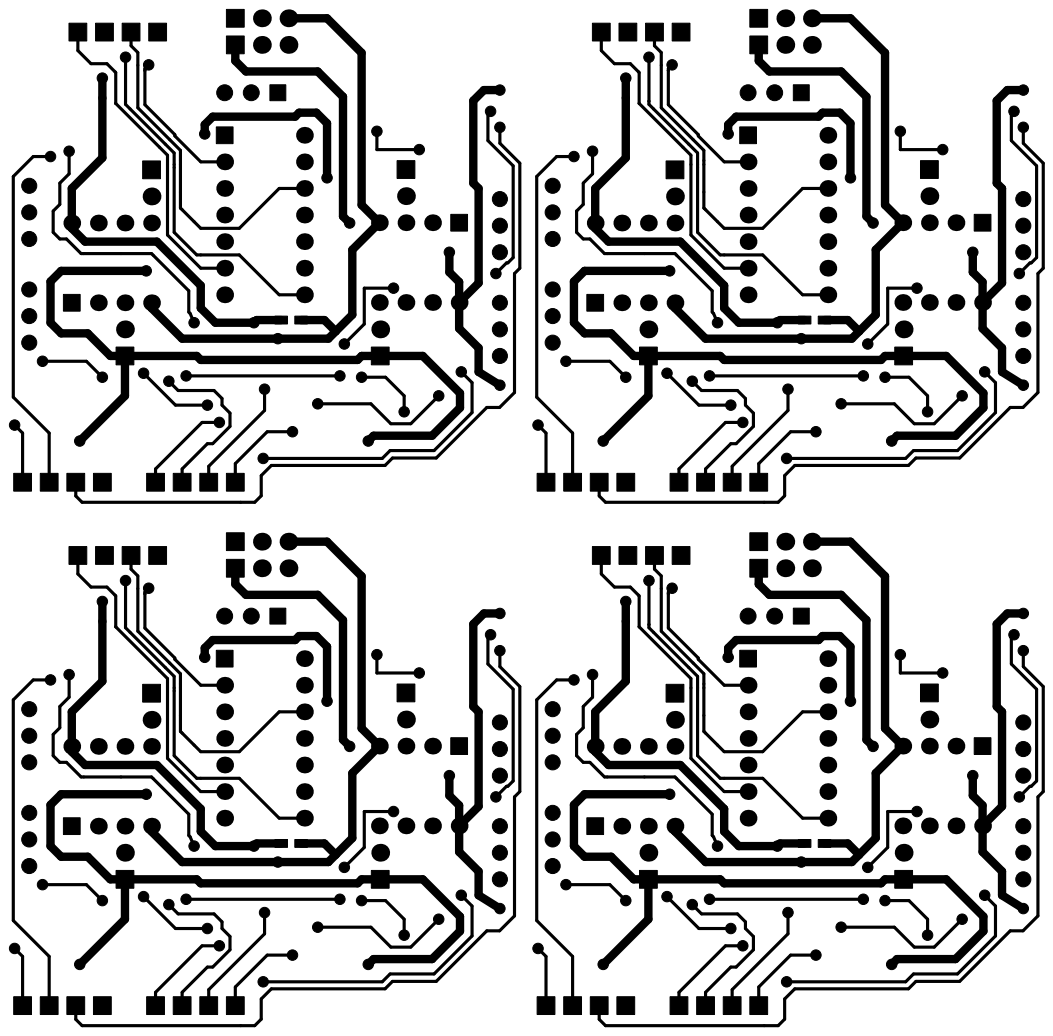
[picture p125: page 1]
