jensenr30/cad/kicad4/XPhone/Input_Board/gerbers/panel/Input Board-B.Fab.pdf

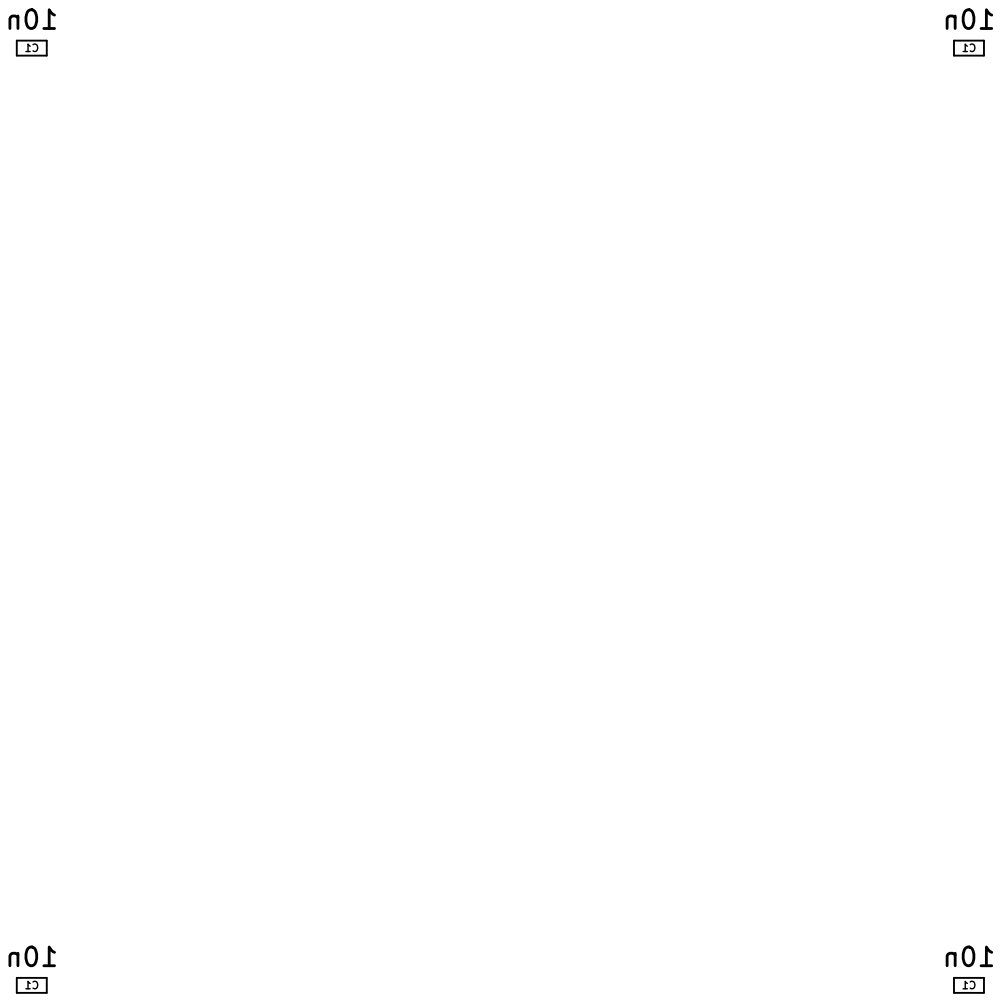
[picture p126: page 1]
