jensenr30/cad/kicad4/XPhone/Input_Board/gerbers/panel/Input Board-B.Mask.pdf

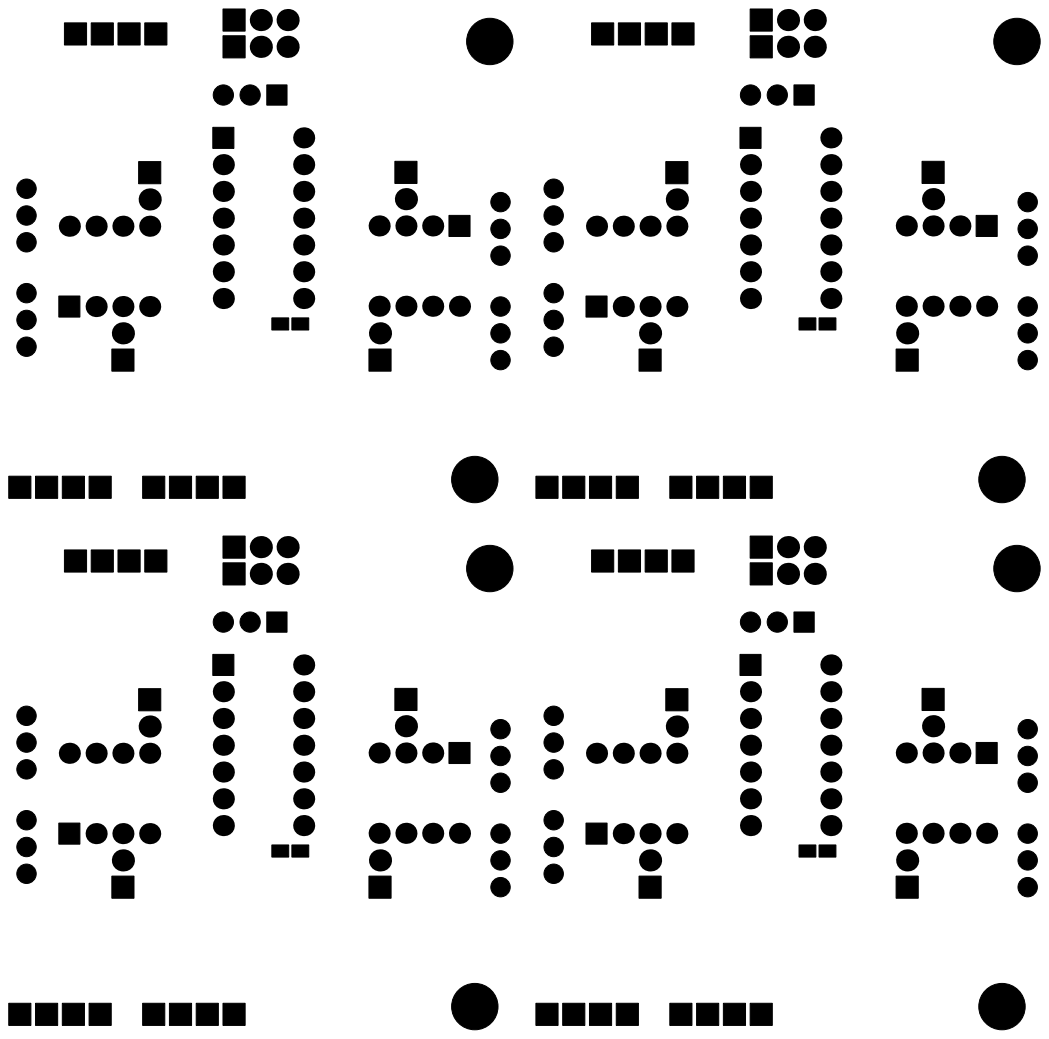
[picture p127: page 1]
