jensenr30/cad/kicad4/XPhone/Input_Board/gerbers/panel/Input Board-B.SilkS.pdf

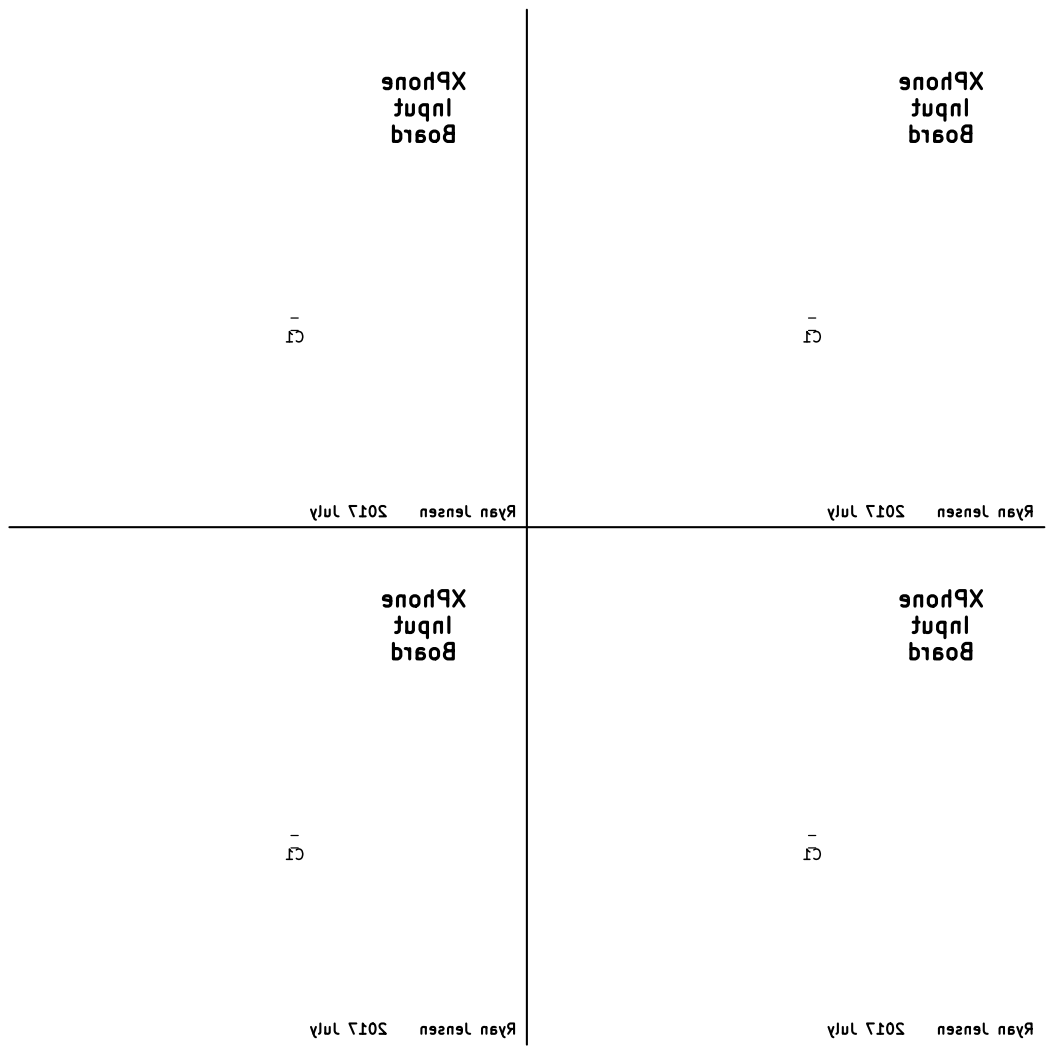
[picture p128: page 1]

Ryan Jensen 2017 July Ryan Jensen 2017 July Ryan Jensen 2017 July Ryan Jensen 2017 July XPhone
