jensenr30/cad/kicad4/XPhone/Input_Board/gerbers/panel/Input Board-F.Cu.pdf

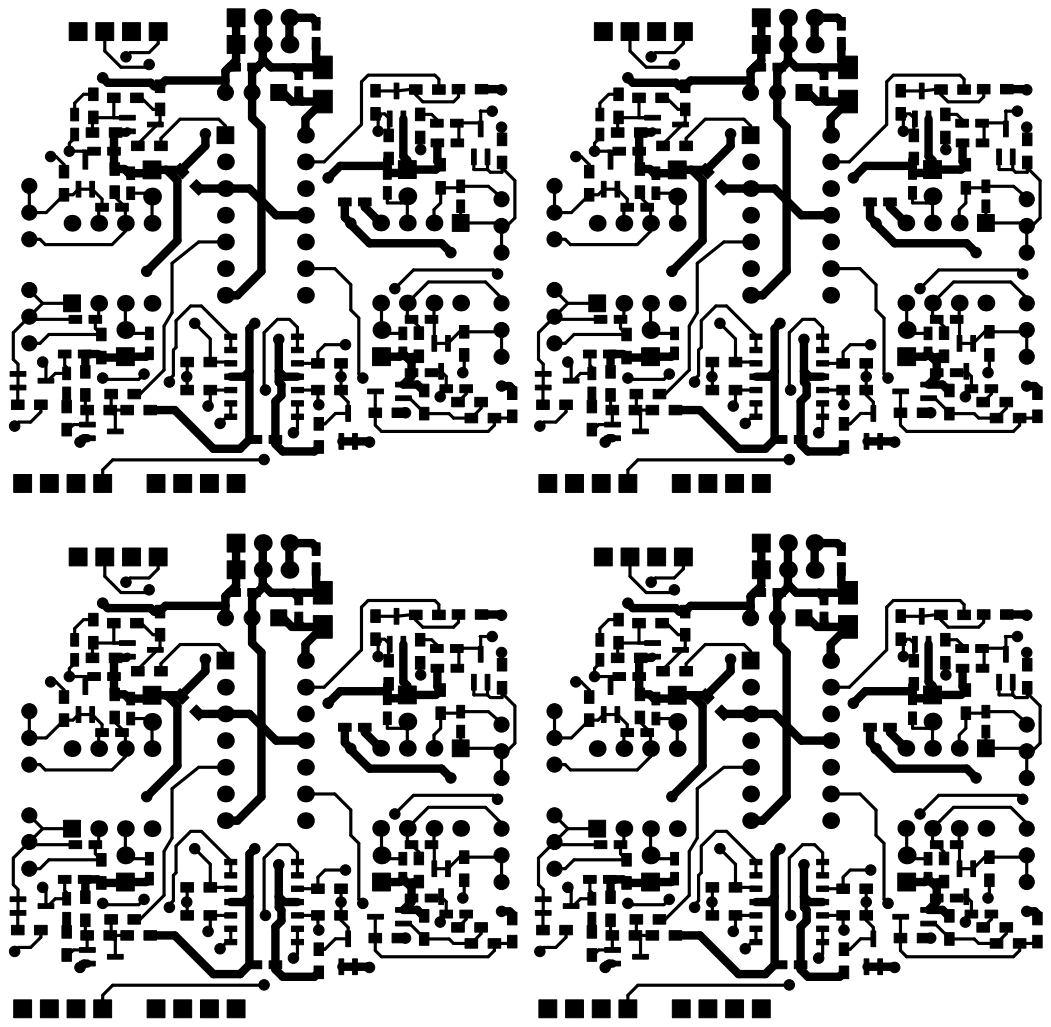
[picture p129: page 1]
