jensenr30/cad/kicad4/XPhone/Input_Board/gerbers/panel/Input Board-F.Fab.pdf

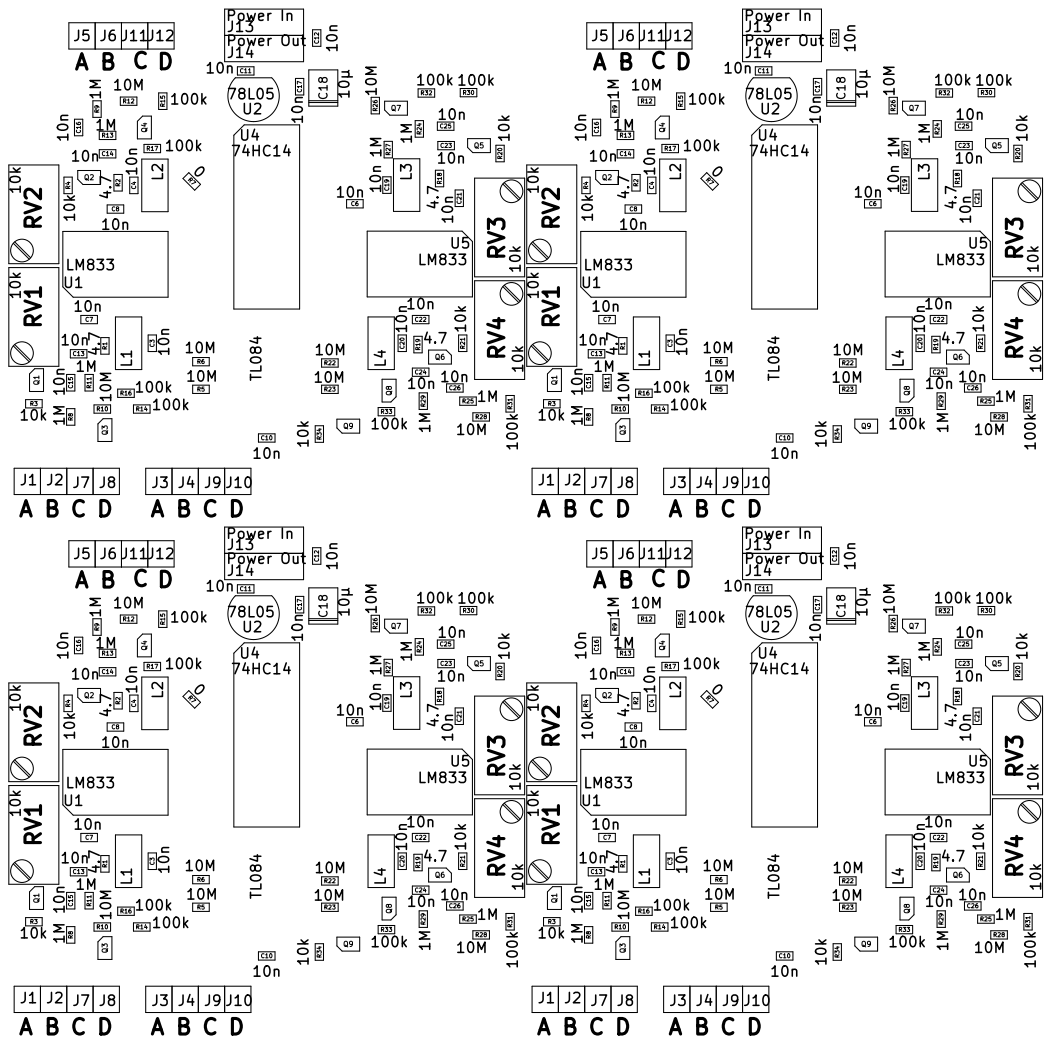
[picture p130: page 1]
