jensenr30/cad/kicad4/XPhone/Input_Board/gerbers/panel/Input Board-F.Mask.pdf

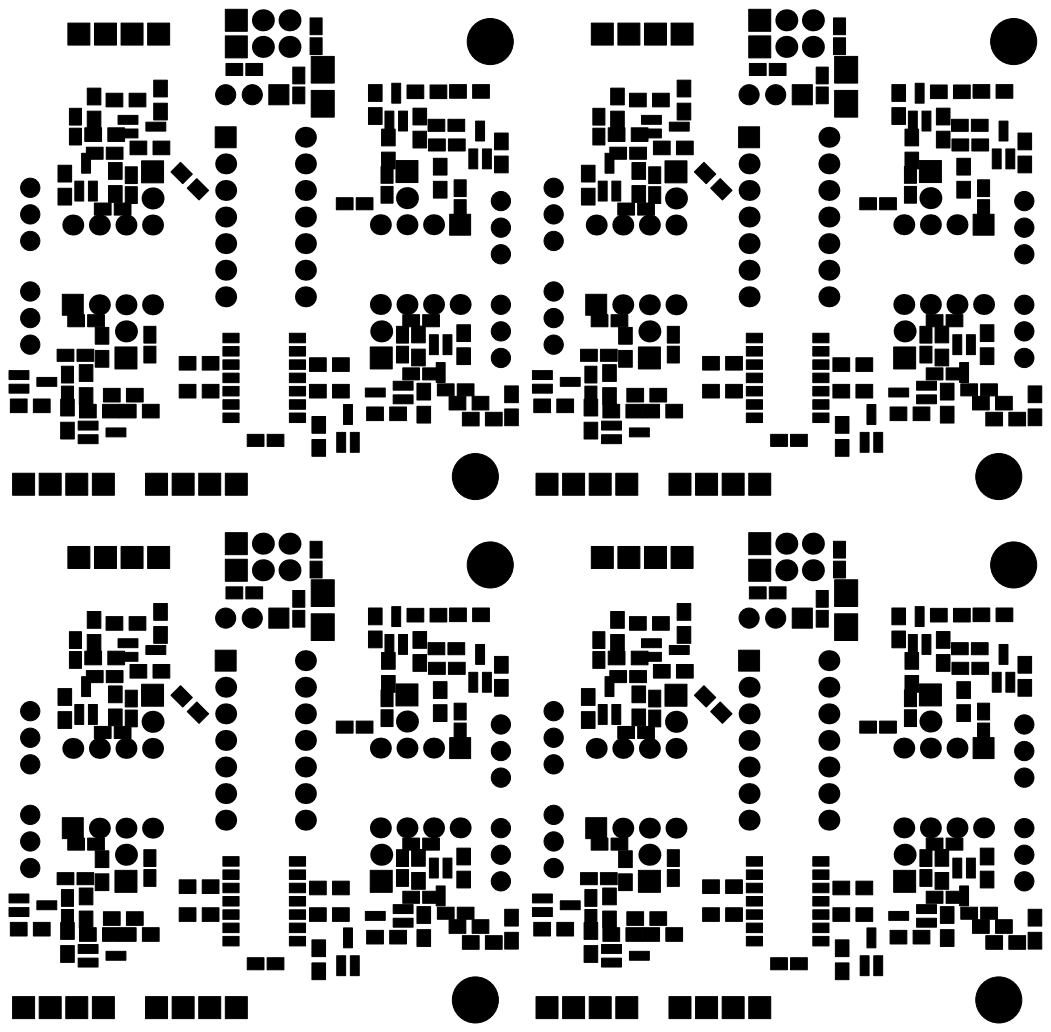
[picture p131: page 1]
