jensenr30/cad/kicad4/XPhone/Input_Board/gerbers/panel/Input Board-F.SilkS.pdf

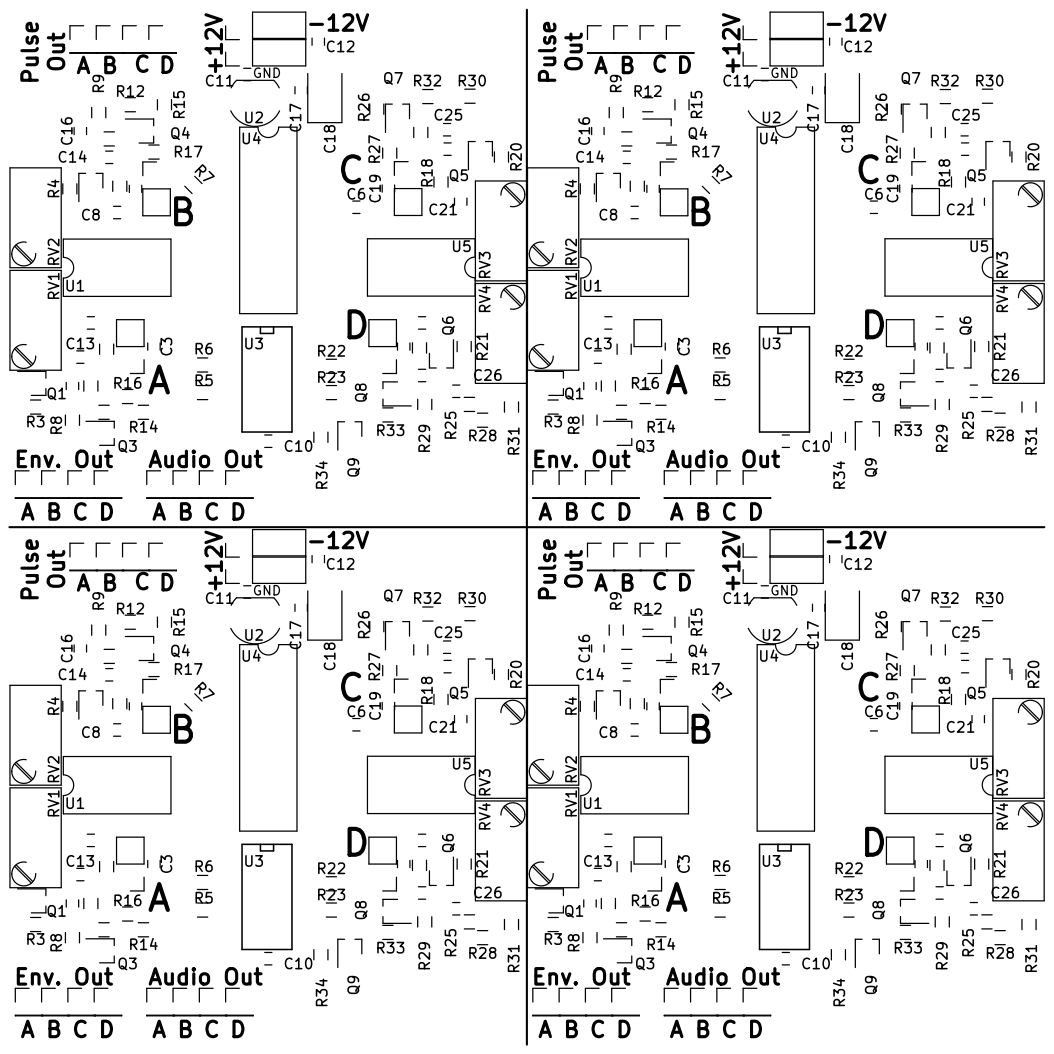
[picture p132: page 1]
