jensenr30/cad/eagle6/Analog Synth/VCO-v1/Voltage Controlled Oscillator v1.pdf

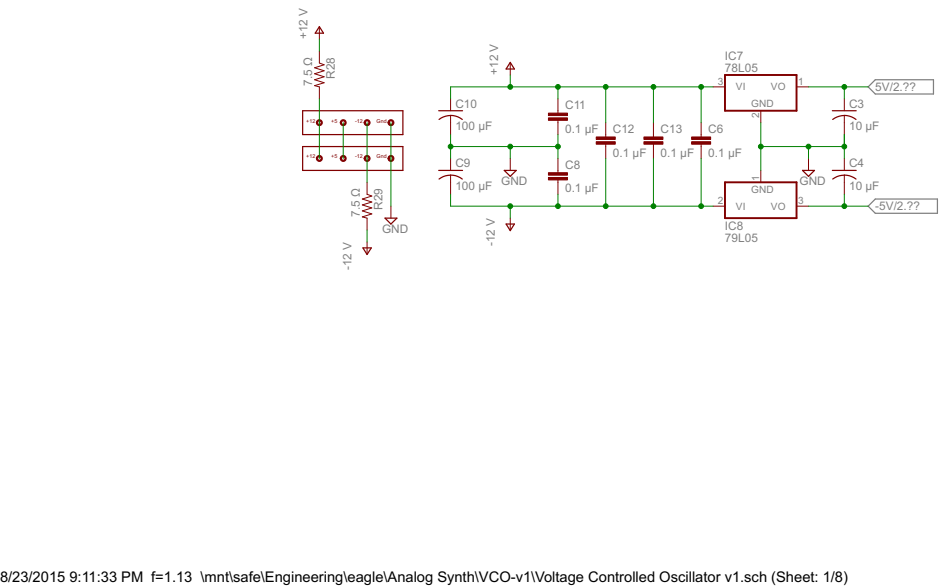
[picture p133: page 1]

8/23/2015 9:11:33 PM f=1.13 \mnt\safe\Engineering\eagle\Analog Synth\VCO-v1\Voltage Controlled Oscillator v1.sch (Sheet: 1/8)

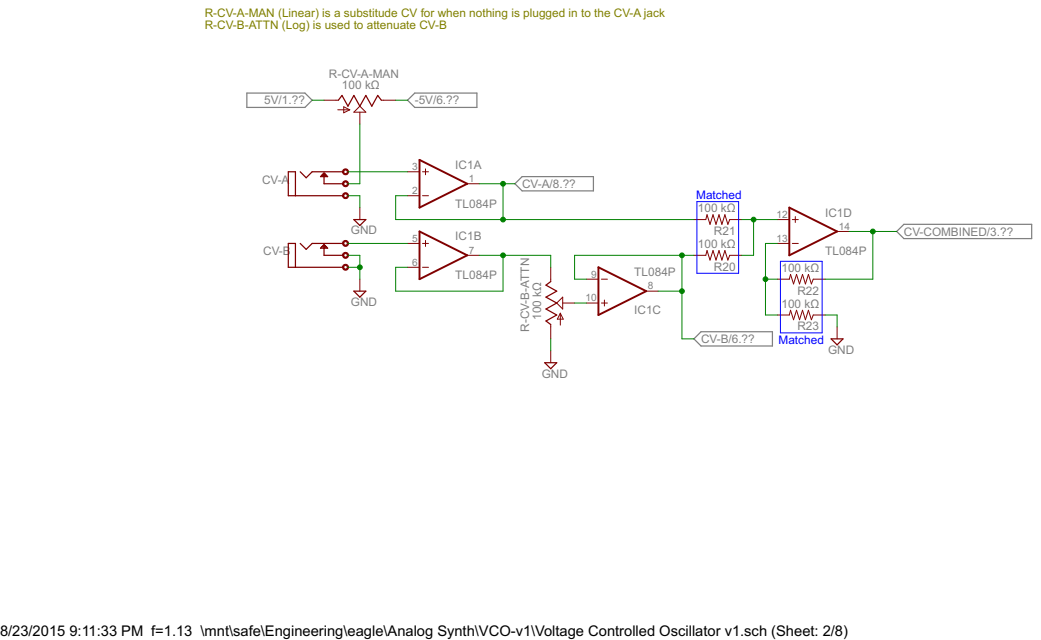
[picture p134: page 2]

R-CV-A-MAN (Linear) is a substitude CV for when nothing is plugged in to the CV-A jack
R-CV-B-ATTN (Log) is used to attenuate CV-B

8/23/2015 9:11:33 PM f=1.13 \mnt\safe\Engineering\eagle\Analog Synth\VCO-v1\Voltage Controlled Oscillator v1.sch (Sheet: 2/8)

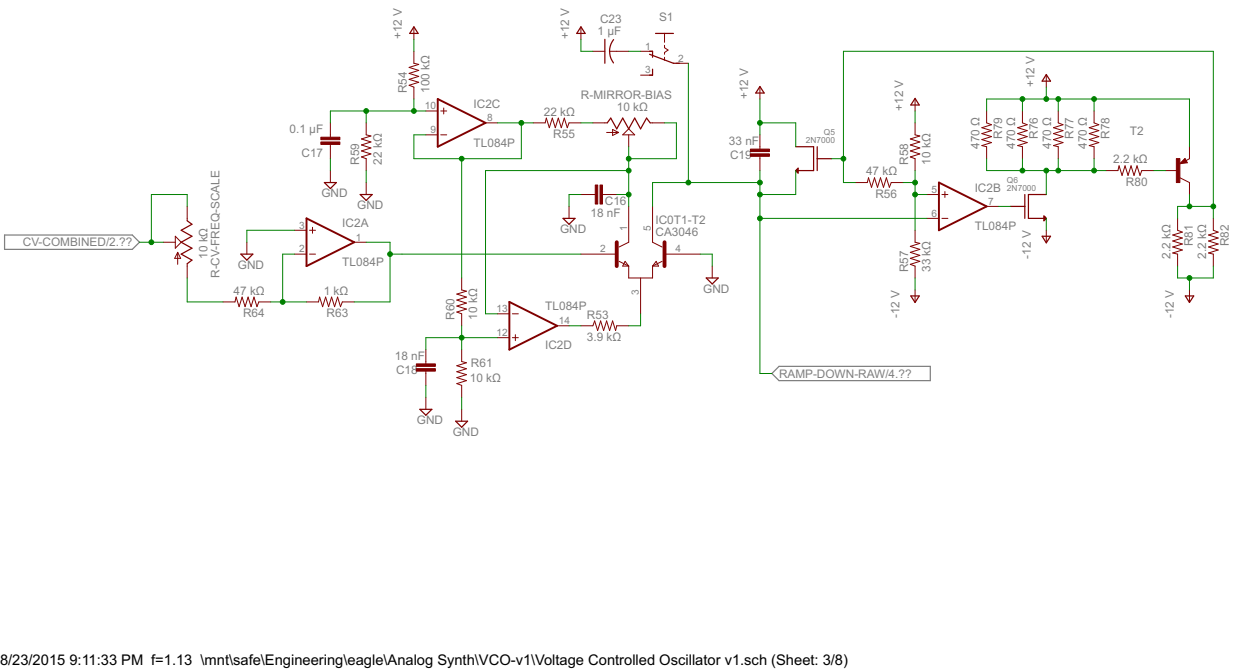
[picture p135: page 3]

8/23/2015 9:11:33 PM f=1.13 \mnt\safe\Engineering\eagle\Analog Synth\VCO-v1\Voltage Controlled Oscillator v1.sch (Sheet: 3/8)

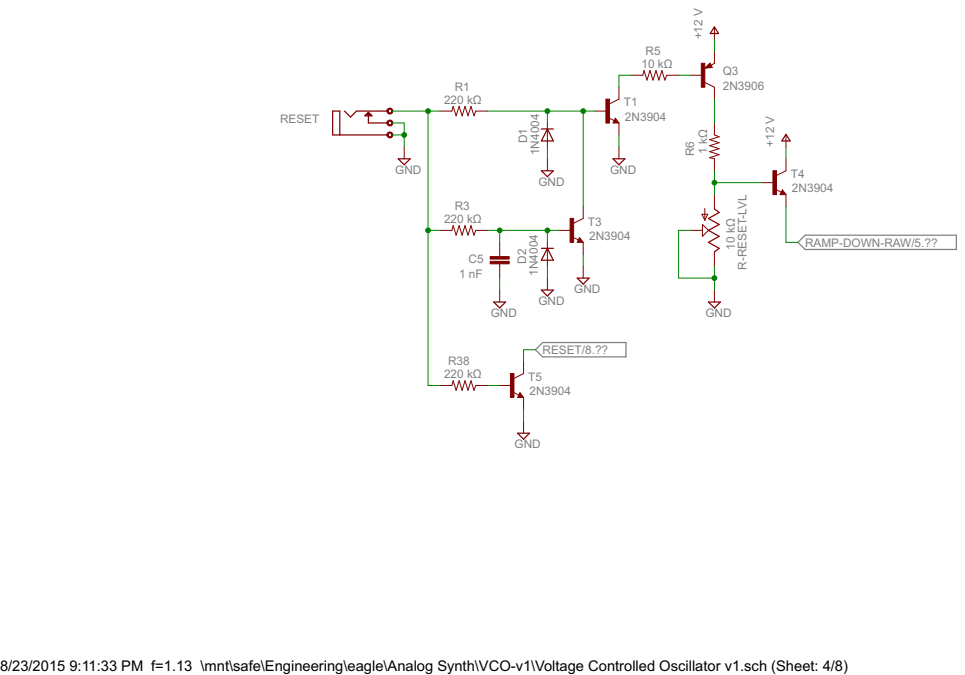
[picture p136: page 4]

8/23/2015 9:11:33 PM f=1.13 \mnt\safe\Engineering\eagle\Analog Synth\VCO-v1\Voltage Controlled Oscillator v1.sch (Sheet: 4/8)

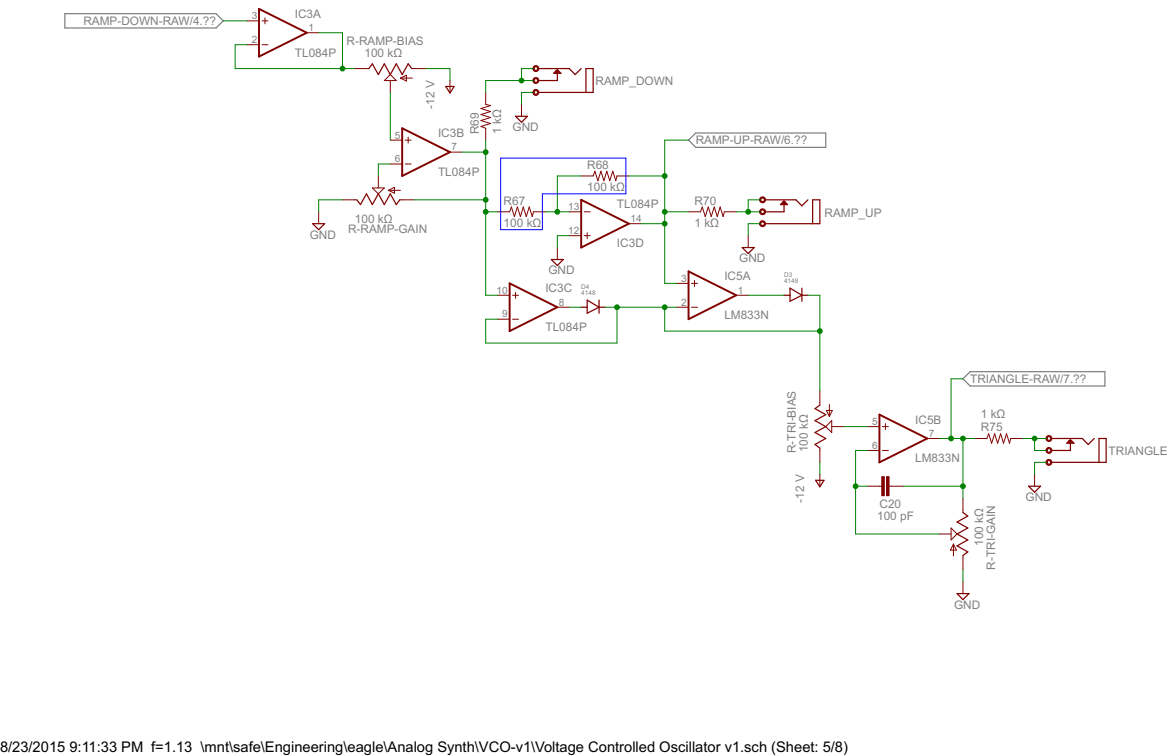
[picture p137: page 5]

8/23/2015 9:11:33 PM f=1.13 \mnt\safe\Engineering\eagle\Analog Synth\VCO-v1\Voltage Controlled Oscillator v1.sch (Sheet: 5/8)

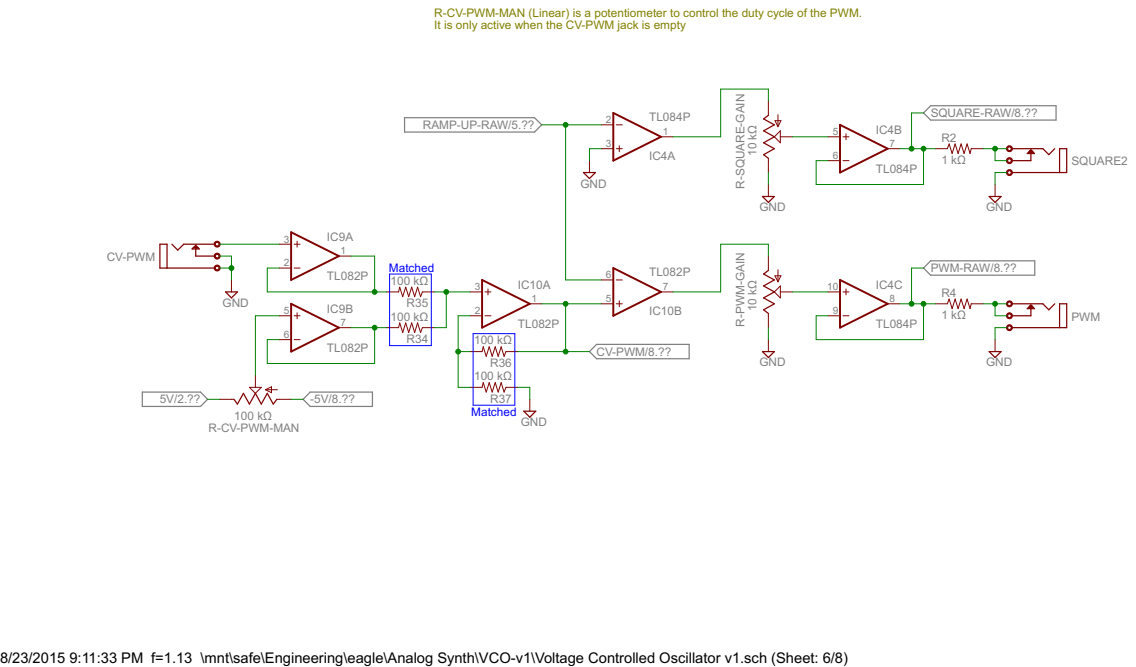
[picture p138: page 6]

R-CV-PWM-MAN (Linear) is a potentiometer to control the duty cycle of the PWM.
It is only active when the CV-PWM jack is empty

8/23/2015 9:11:33 PM f=1.13 \mnt\safe\Engineering\eagle\Analog Synth\VCO-v1\Voltage Controlled Oscillator v1.sch (Sheet: 6/8)

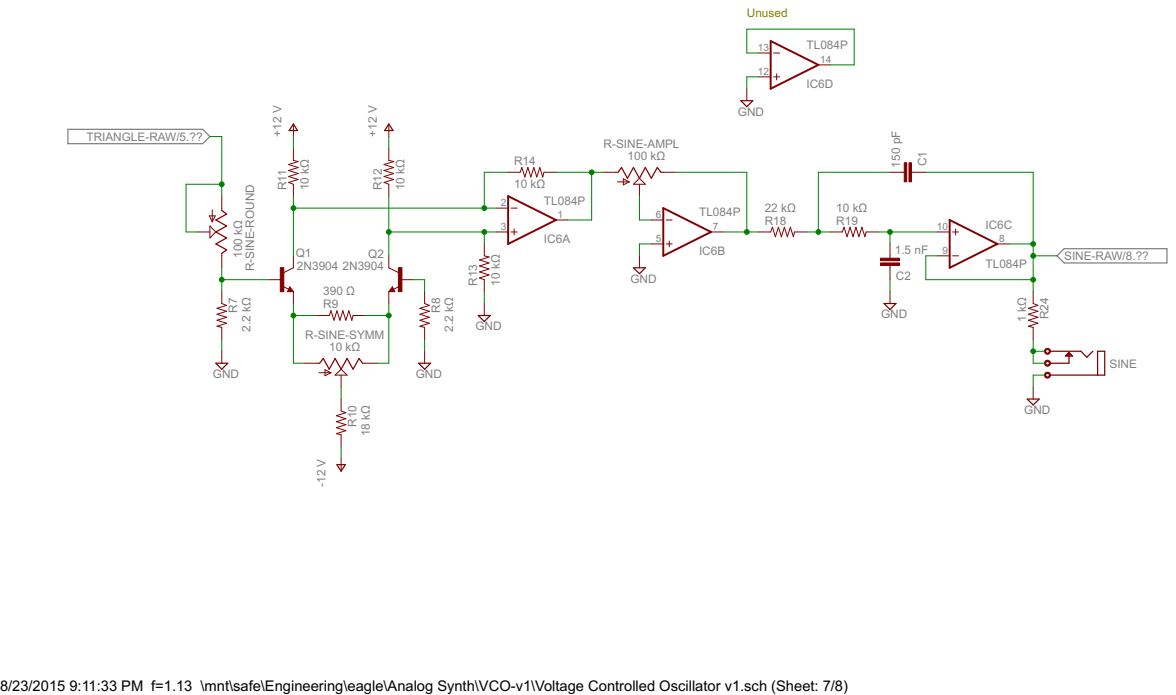
[picture p139: page 7]

8/23/2015 9:11:33 PM f=1.13 \mnt\safe\Engineering\eagle\Analog Synth\VCO-v1\Voltage Controlled Oscillator v1.sch (Sheet: 7/8)

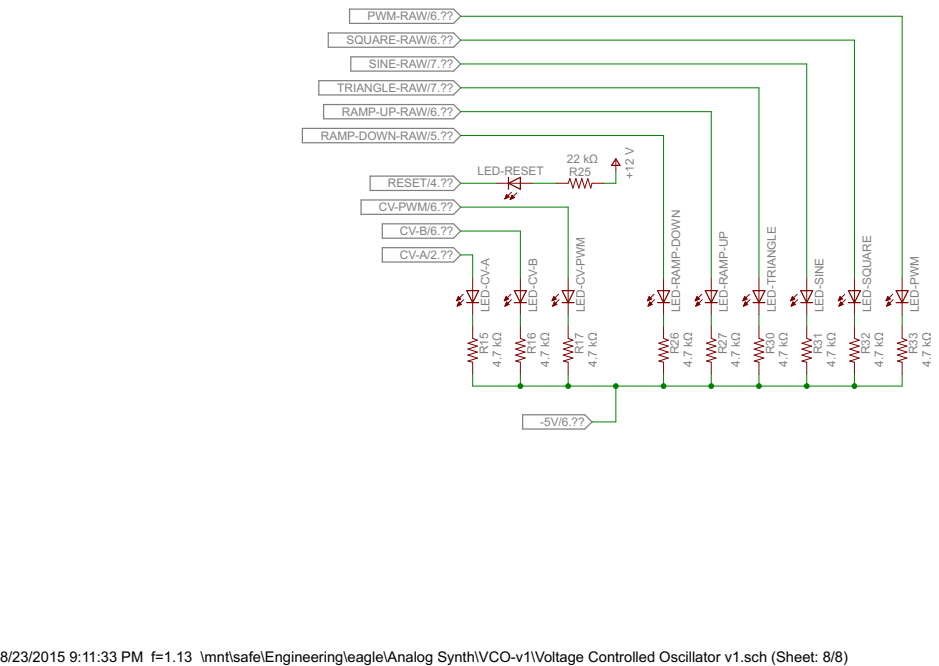
[picture p140: page 8]

8/23/2015 9:11:33 PM f=1.13 \mnt\safe\Engineering\eagle\Analog Synth\VCO-v1\Voltage Controlled Oscillator v1.sch (Sheet: 8/8)
