jensenr30/cad/eagle6/Analog Synth/CBS - Cigar Box Sequencer/Sequencer - 8 Step - Cigar Box v1.0.pdf

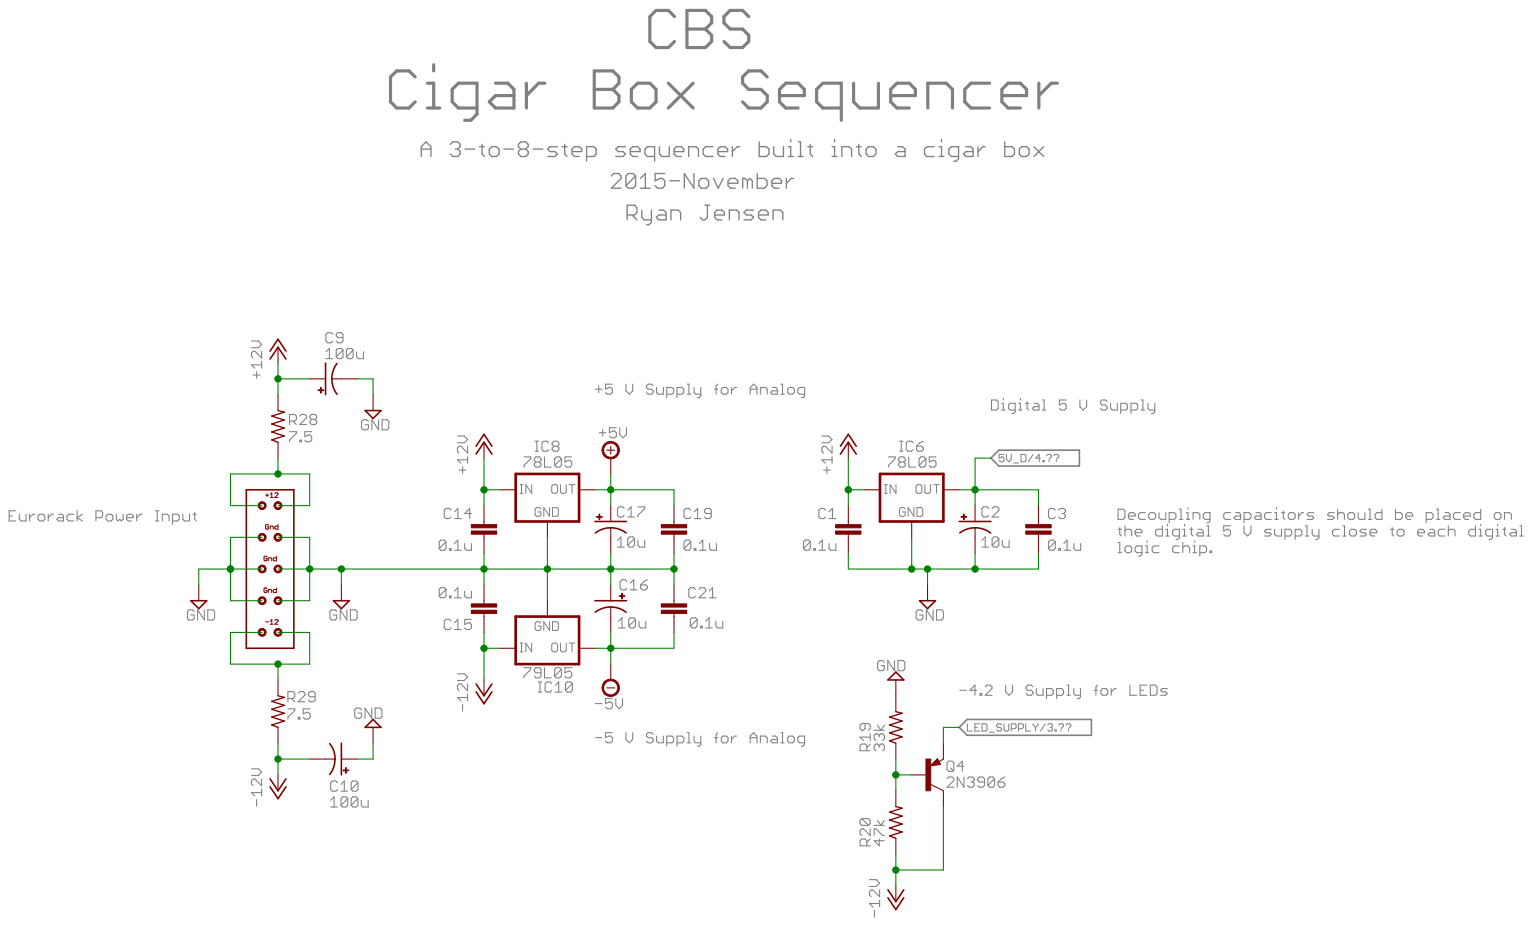
[picture p141: page 1]

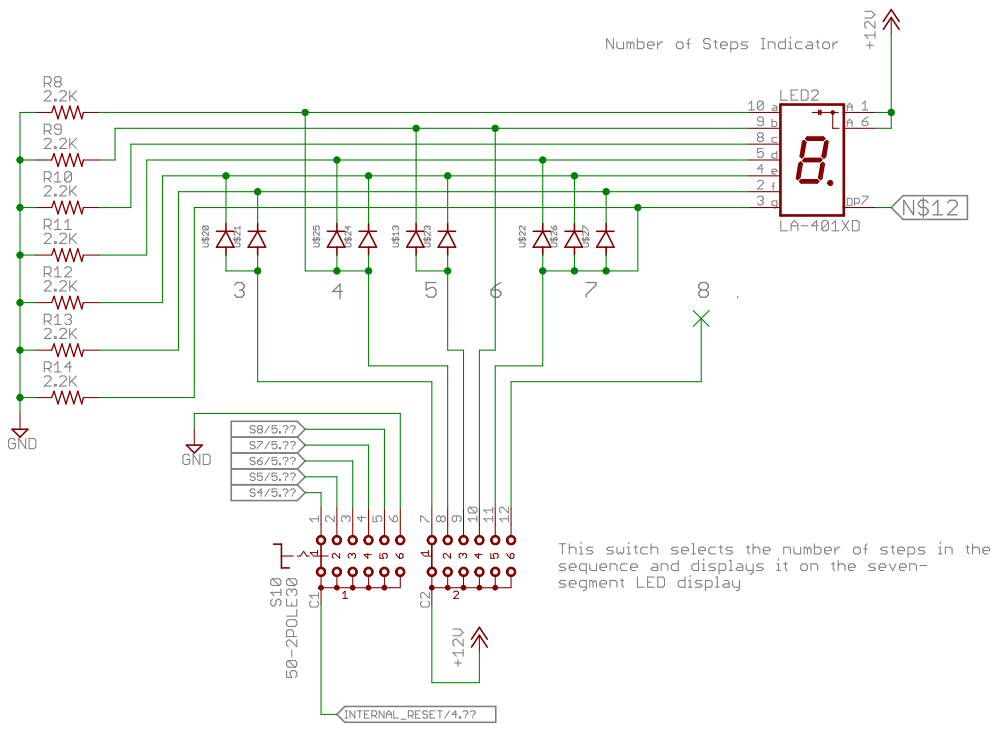
[picture p142: page 2]

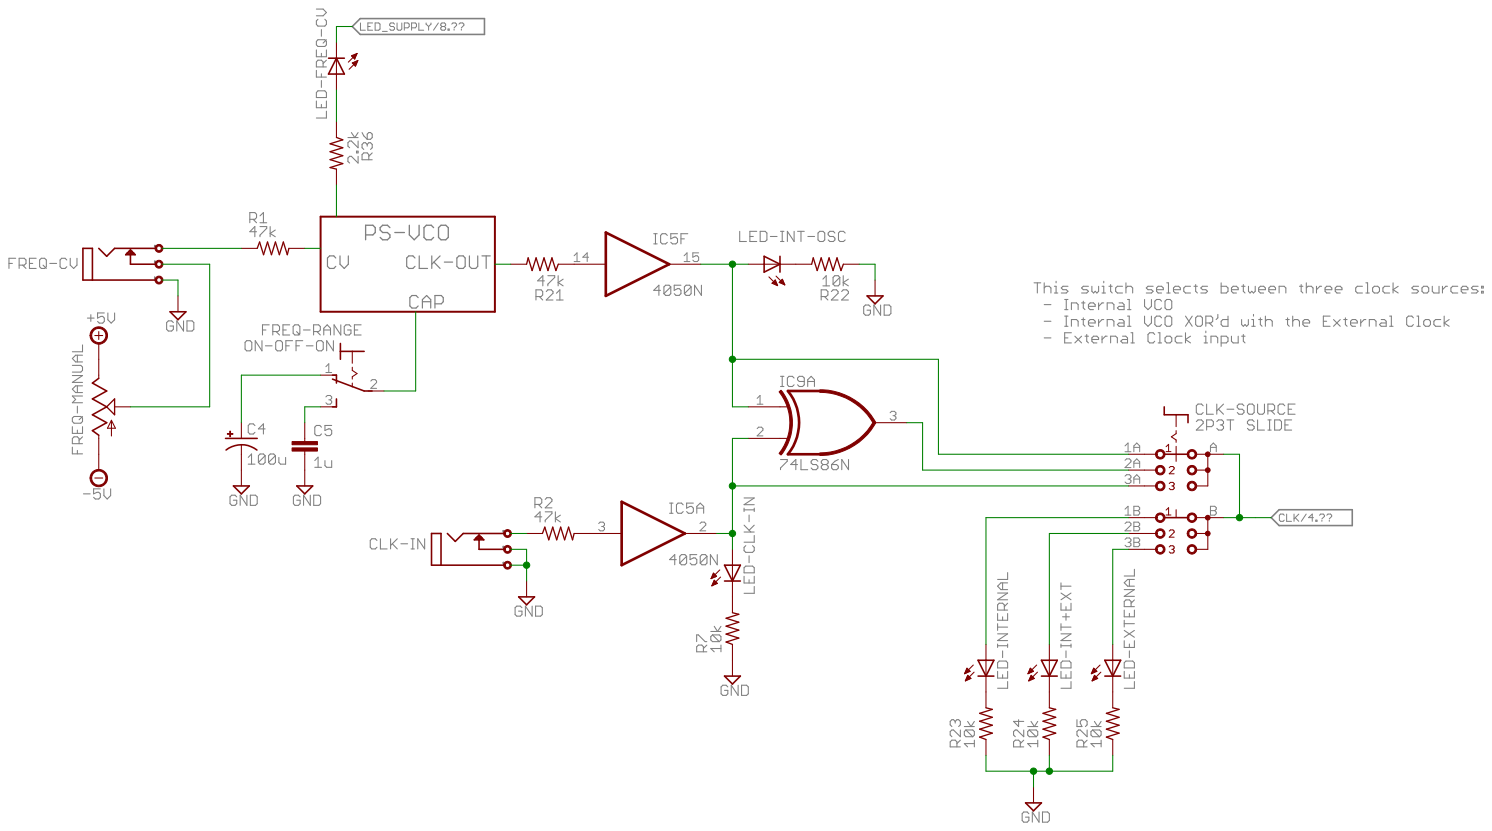
[picture p143: page 3]

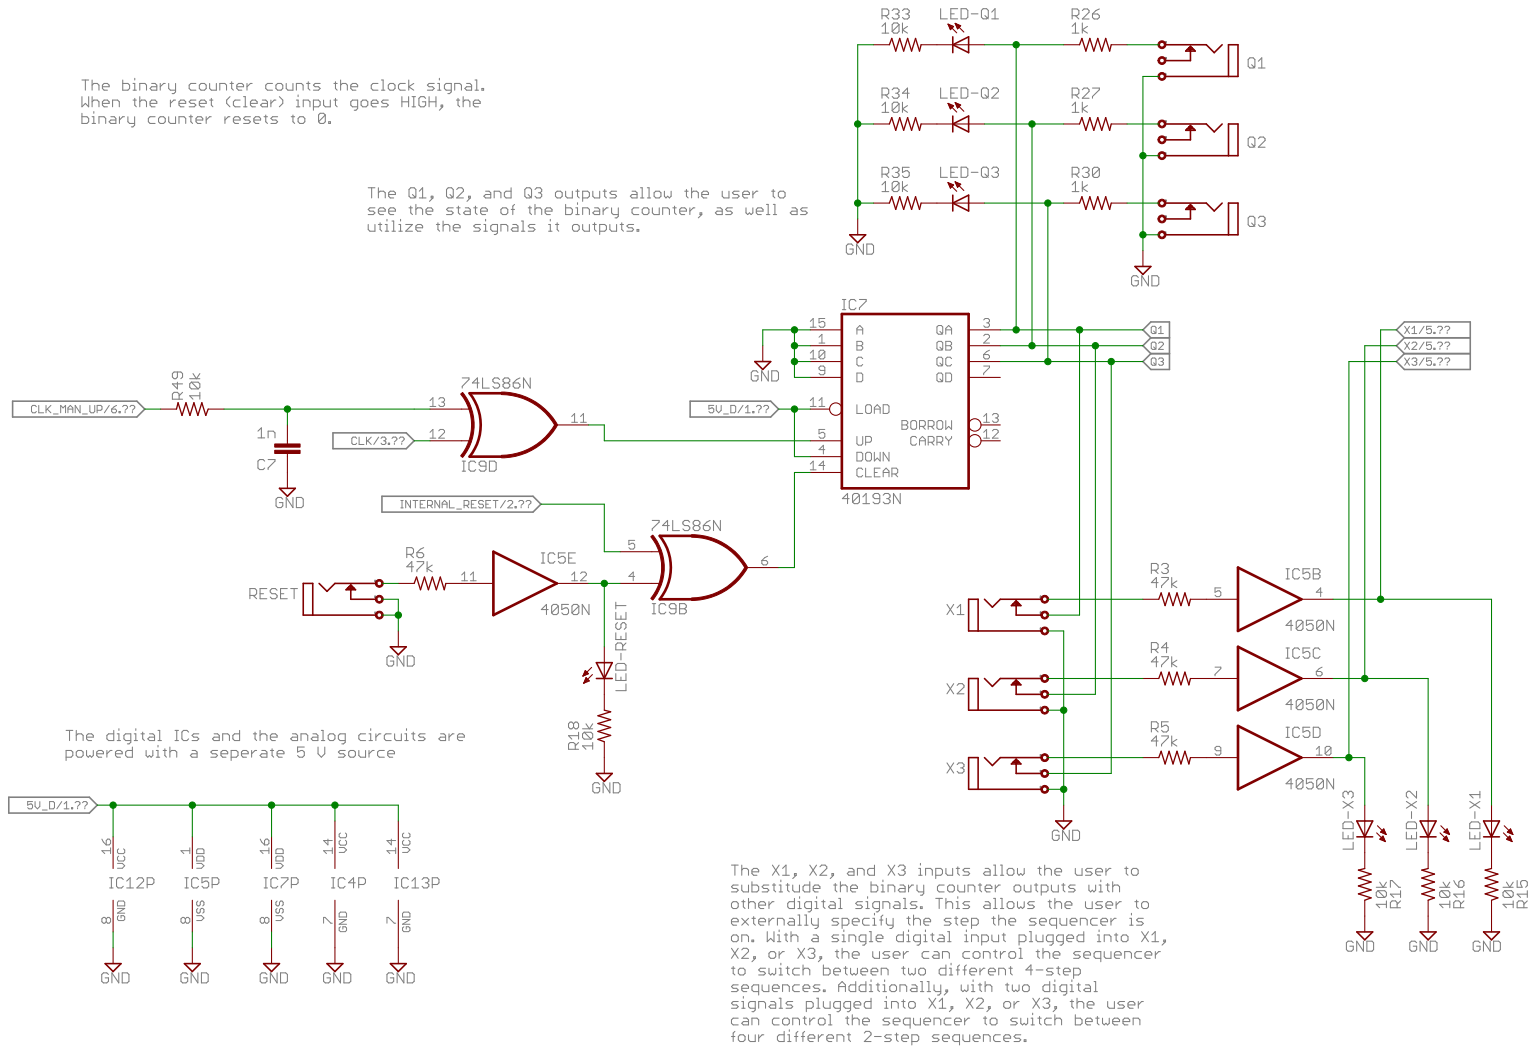
[picture p144: page 4]

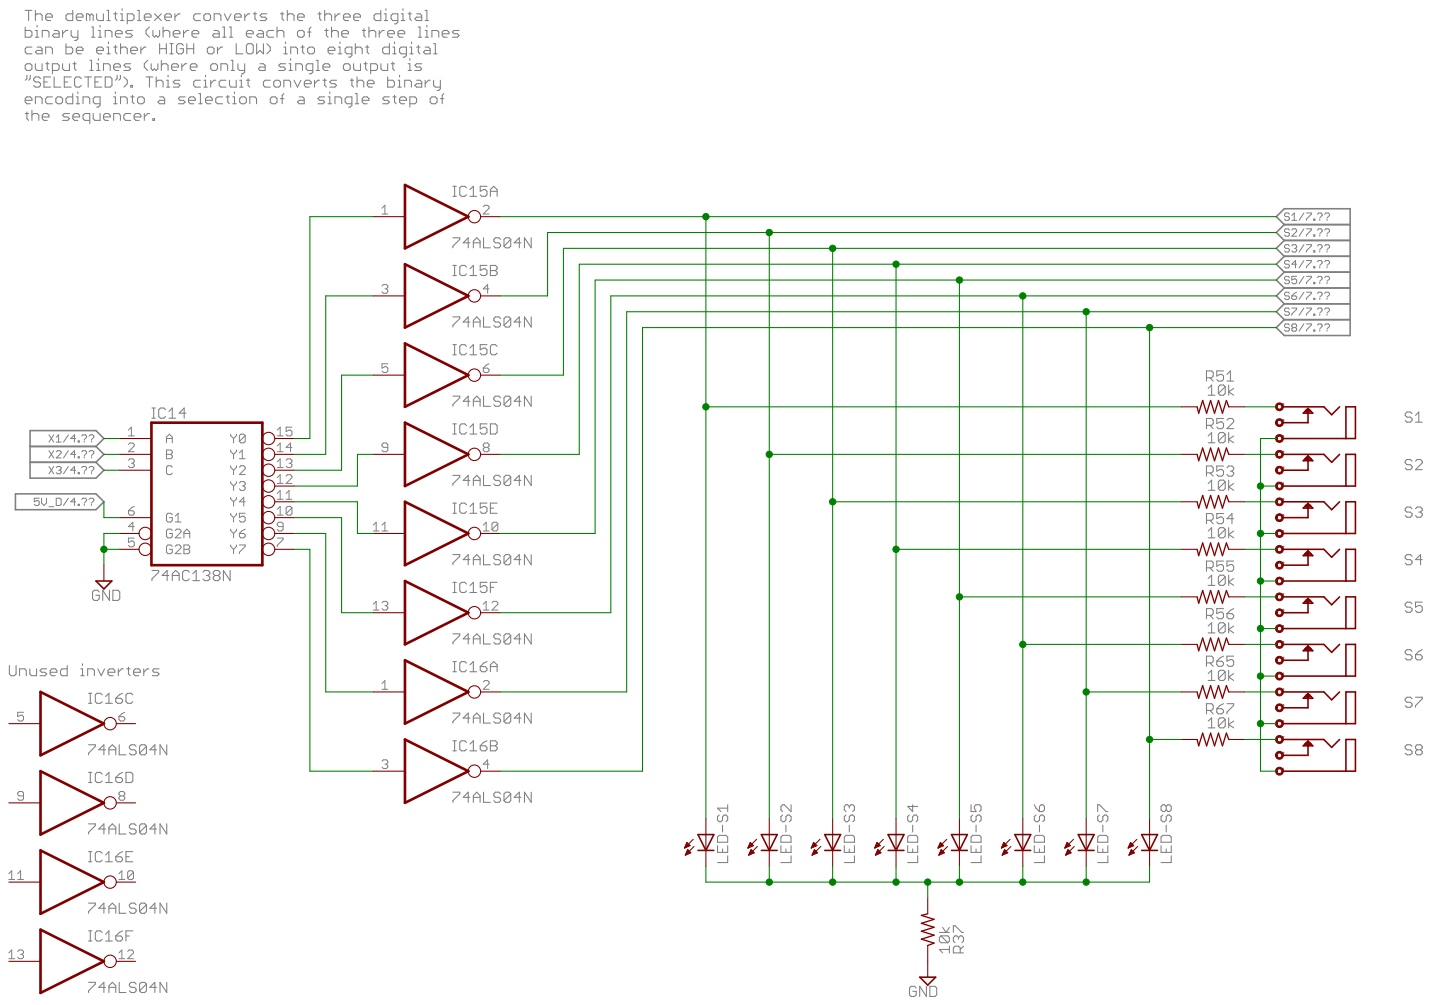
[picture p145: page 5]


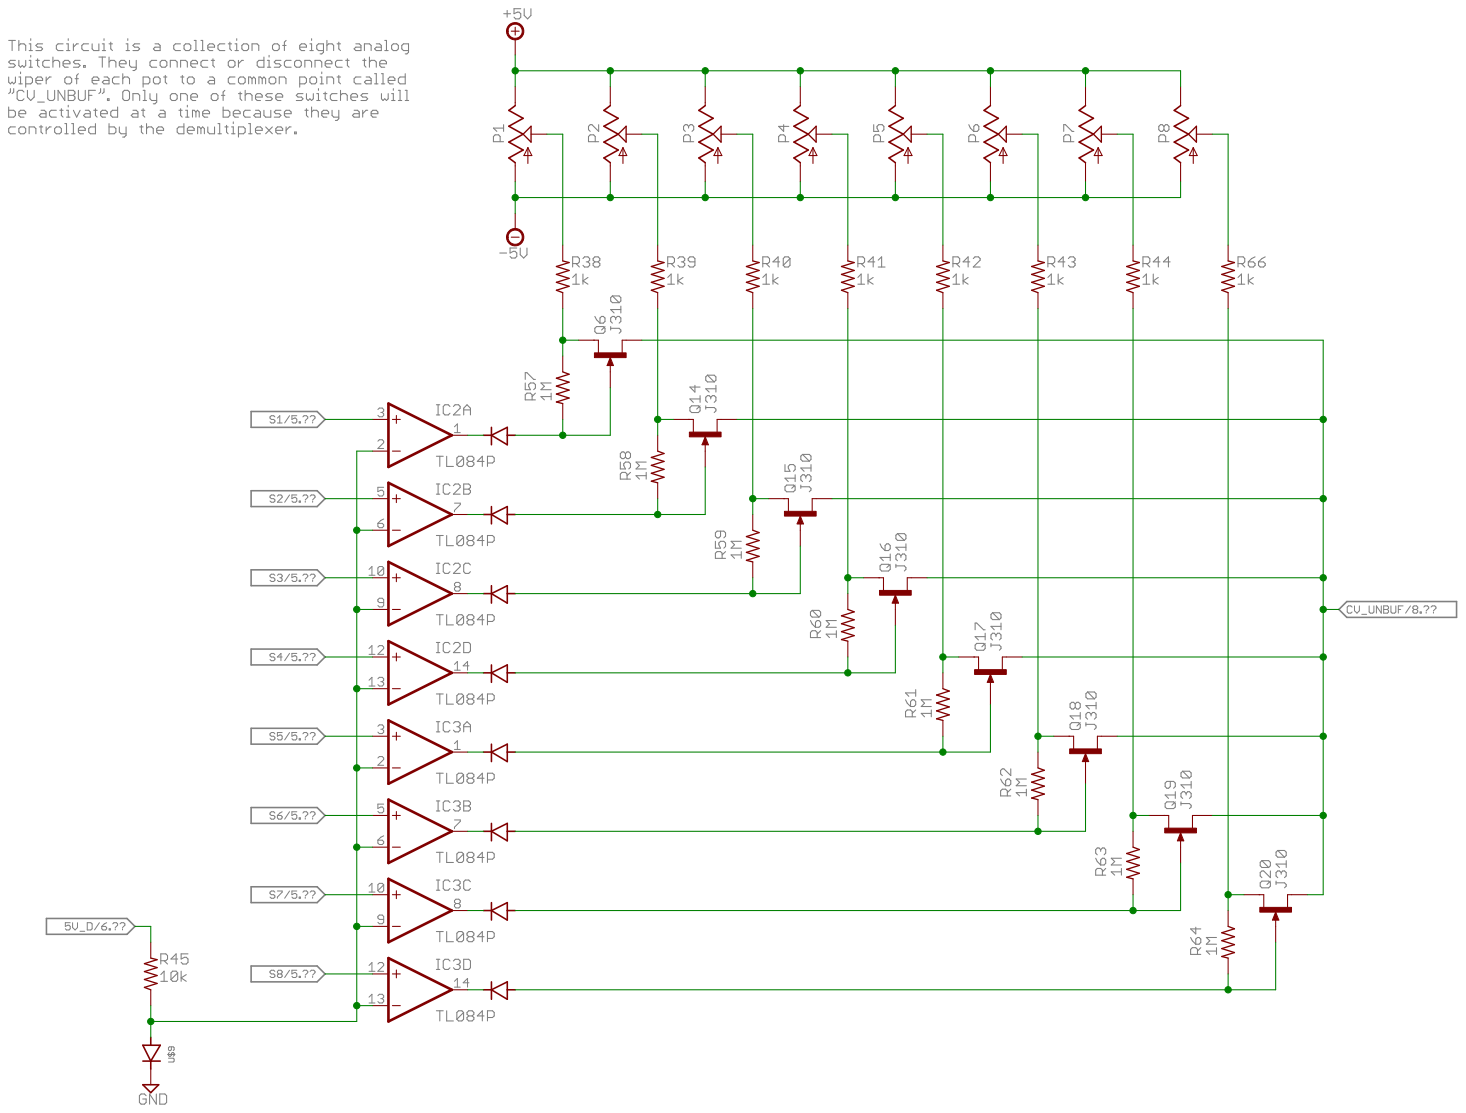
[picture p146: page 7]

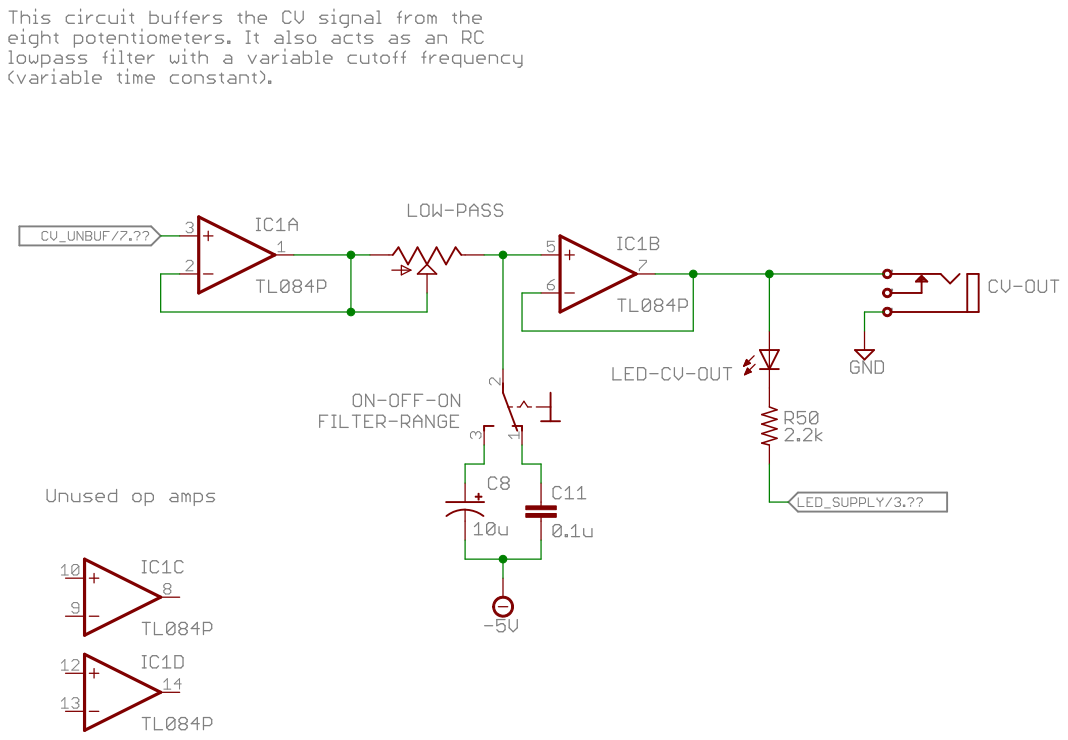
[picture p147: page 8]
