jensenr30/cad/eagle6/Analog Synth/CBS - Cigar Box Sequencer/Sequencer - 8 Step - Cigar Box v1.1.pdf

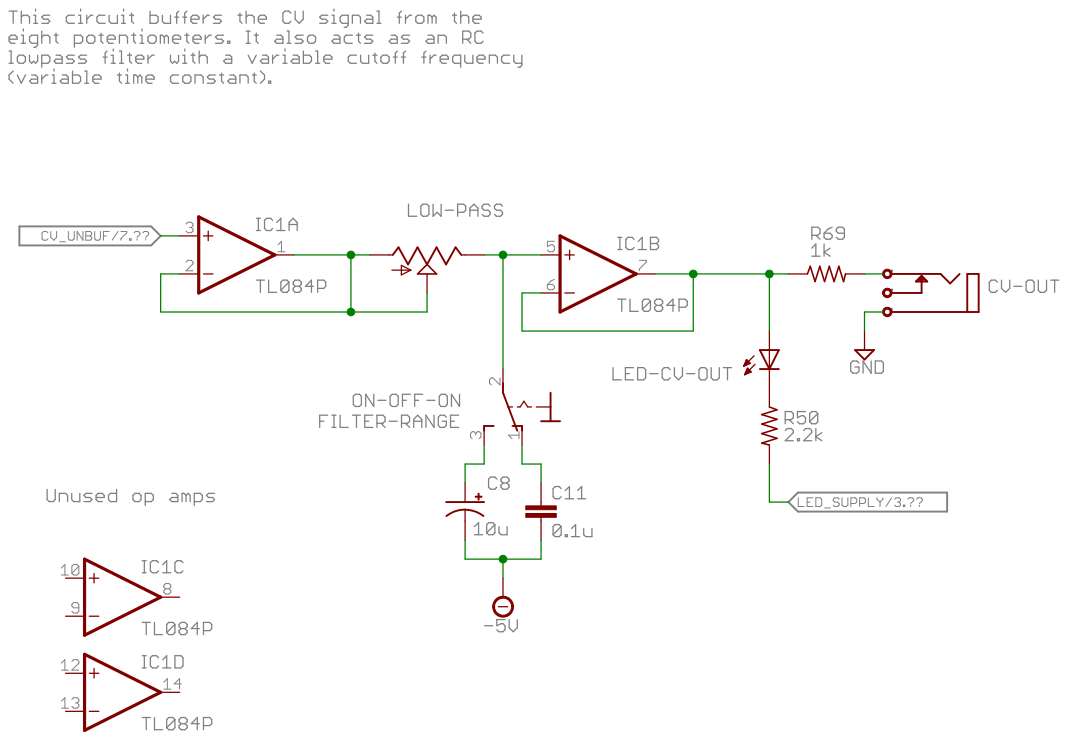
[picture p148: page 8]
