jensenr30/cad/eagle6/Analog Synth/Front Panels/VCA-v1.pdf

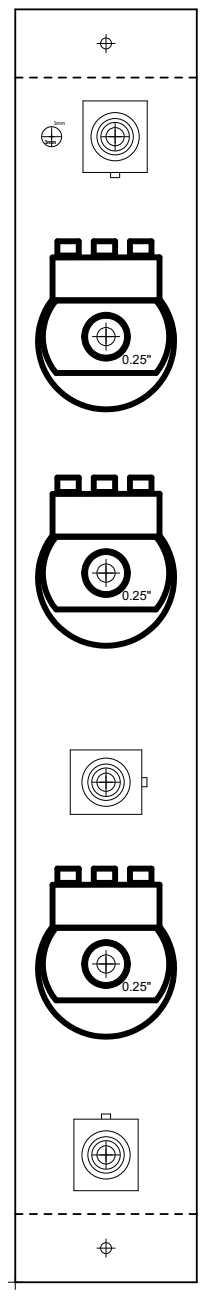
[picture p149: page 1]
