jensenr30/cad/eagle6/Analog Synth/ScreamFilter/ScreamFilter v1.0.pdf

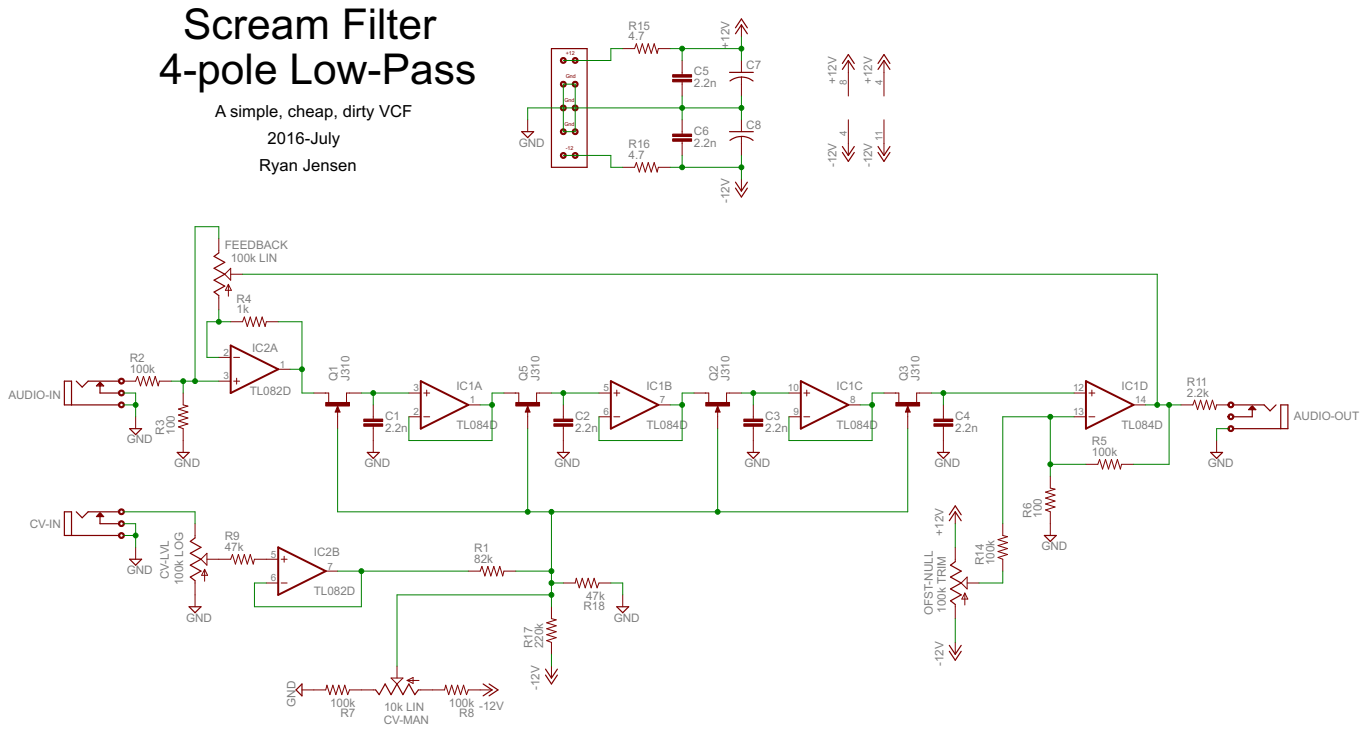
[picture p150: page 1]
