jensenr30/cad/ltspiceIV/switch a solenoid.asc

D2: schottky; 1N5819
I1: current; PULSE(0 50u 100m 1u 1u 100m 400m 2)
L1: ind; 1
Q1: npn; 2SCR512P
Q2: npn; 2N3904
R1: res; 3.9k
R2: res; 10k
R3: res; 192
V1: voltage; 24
Named nets: 0
.tran 1
