jensenr30/cad/ltspiceIV/DC analog to pulse wave.asc

Q1: npn
R1: res; 10k
R2: res; 1k
V1: voltage; 5
V2: voltage; SINE(0 5 10)
Named nets: 0
