jensenr30/cad/ltspiceIV/integration oscillator.asc

C1: cap; 0.001µ
D3: diode
R1: res; 1k
R3: res; 1k
R4: res; 2k
R6: res; 100k
R10: res; 100k
R11: res; 10k
S1: sw
S2: sw
U1: opamp
U3: LTC1441
U5: opamp
U6: opamp
V1: voltage; PWL(0 -0.4 1 -0.64)
V2: voltage; -5
V3: voltage; 5
Named nets: 0, Triangle_Out
.lib opamp.sub
.tran 1 uic
.model SW SW(Ron=0.001 Roff=1000Meg Vt=0 Vh=0.1)
