jensenr30/cad/ltspiceIV/low-pass with feedback unbuffered.asc

C1: cap; {C}
C2: cap; {C}
C3: cap; {C}
C4: cap; {C}
C5: cap; 10n
C6: cap; {C}
C7: cap; {C}
C8: cap; 2.2µ
R1: res; {R}
R2: res; 100k
R3: res; 1k
R4: res; 100k
R5: res; {R}
R6: res; {R}
R7: res; {R}
R8: res; {R}
R9: res; {Rf}
R10: res; {R}
U2: opamp
U3: opamp
V1: voltage; ""; AC 1
Named nets: 0, Vout
.lib opamp.sub
.ac dec 1000 2 2000000
.step param Rf list 100k 47k 22k 10k 5.6k 4.7k
.param R 10k
;.step dec param C 1n 1000n 1
.param C 10n
