jensenr30/cad/ltspiceIV/low-pass with feedback.asc

C1: cap; {C}
C2: cap; {C}
C3: cap; {C}
C4: cap; {C}
R1: res; {R}
R2: res; 100k
R4: res; 100k
R6: res; {R}
R7: res; {R}
R8: res; {R}
R9: res; {Rf}
U1: opamp
U2: opamp
U4: opamp
U5: opamp
U6: opamp
V1: voltage; ""; AC 1
Named nets: 0, Vout
.lib opamp.sub
.ac dec 1000 2 200000
.step dec param Rf 10k 200k 3
.param R 100k
.param C 10n
