jensenr30/cad/ltspiceIV/low-pass.asc

C1: cap; 0.1µ
C2: cap; 0.1µ
J1: njf
R1: res; 2.5k
R2: res; 10k
R3: res; 100k
R4: res; 100k
U1: opamp
V1: voltage; ""; AC 1
V2: voltage; {Vjfet}
Named nets: 0, out
.lib opamp.sub
.ac dec 4321 1 100k
.step param Vjfet 0 -2 -0.1
