jensenr30/cad/ltspiceIV/ScreamFilter CV.asc

R1: res; 100k
R2: res; 100k
R3: res; 220k
R4: res; 10k
R5: res; 47k
R6: res; 52.44k
R7: res; 82k
V1: voltage; SINE(0 5 1)
V2: voltage; -12
V3: voltage; -12
V4: voltage; SINE(-6 0.5714 20)
Named nets: 0, Vcv
.tran 2
