jensenr30/cad/ltspiceIV/Wavefolder.asc

C1: cap; 1
C2: cap; 1
Q1: npn
Q2: pnp
Q3: npn
Q4: pnp
R1: res; 15k
R2: res; 15k
R3: res; 22k
R4: res; 22k
R5: res; 10k
R6: res; 15k
R7: res; 15k
R8: res; 22k
R9: res; 22k
R10: res; 10k
R11: res; 10k
R12: res; 1k
U1: opamp
V1: voltage; 15
V2: voltage; -15
V3: voltage; SINE(0 {Vval} 440)
V4: voltage; 15
V5: voltage; -15
Named nets: 0
.tran 10ms
.step dec param Vval 0.05 5 2
.lib opamp.sub
